Chemcrin/IntelligentTransformCart/代码/VibeCoding/工程纠错/628问题核验与修复方案.md

# 628 问题审查核验与修复方案

> 核验对象：`D:\STM32CubeIDE\workspace_1.19.0\smart_logistics_car_integrated_route_2026-06-17`  
> 原始问题文档：`C:\Users\CloudyRain\Desktop\待办\个性化物流小车\代码\628问题审查.md`  
> 核验日期：2026-06-28  
> 说明：本报告仅核验问题和给出可行方案，未修改工程源码。

## 1. 总结结论

原 Markdown 文档中的核心问题大多真实存在，但有几处需要校正严重度或前提条件：系统 8 MHz、固定路线自动启动、电机反馈空桩、栈预留与 IOC 不一致都可以从源码或构建产物直接确认；RS485 方向控制和上电使能风险依赖实际硬件；部分“致命”描述更适合改为“高优先级风险”，否则后续修复容易被夸大的影响带偏。

| 分类 | 数量 | 结论 |
|---|---:|---|
| 确认存在，建议优先处理 | 6 | F1、F2、C1、C3、C4、M1 |
| 部分成立或依赖硬件确认 | 5 | C2、M2、M3、M4、S5 |
| 成立但不属于必须立即修复 | 7 | M5、S1、S2、S3、S4、S6、冗余代码清理 |
| 原文需校正 | 3 | F1 的外设影响表述偏重、F2 对当前固定路线的直接影响偏重、C1 的“通过 RPi 命令启动路线”当前没有现成命令 |

## 2. 问题逐项核验表

| 编号  | 原问题 | 是否存在 | 核验证据 | 严重度校正 |
| --- | --- | --- | --- | --- |
| F1  | 系统时钟仅 8 MHz HSI，未启用 PLL | 确认存在 | `Core/Src/main.c:154-172` 使用 HSI、`PLL_NONE`、`SYSCLKSource=HSI`；`.ioc` 中 `RCC.PLLCLKFreq_Value=8000000` | 高优先级。性能确实低于 72 MHz，但 UART/I2C 不必然异常，HAL 会按当前 PCLK 配置分频 |
| F2  | 电机反馈读取为空桩 | 确认存在 | `Core/Src/motor_manager.c:86-89` 只有 `return MECANUM_OK;`；`StraightControl_Apply()` 依赖 `rpm_fb` | 高优先级。对直线轮差闭环真实有影响；对当前 Standalone 固定路线的直接影响有限，因为路线本身关闭直线闭环 |
| C1  | Standalone 模式 200ms 后自动行驶 | 确认存在 | `config.h:5` 为 `FIXED_ROUTE_STANDALONE_ENABLE=1U`；`competition_route.h:23-24` 自动启动；`competition_route.c:159-175` 200ms 后放行 | P0 安全项。上电自动开始第一步 3.3m 前进，必须先处理或在物理上架空车轮 |
| C2  | RS485 方向控制依赖硬件 | 部分成立 | `mecanum_config.h:71` 为 `MODBUS_USE_RS485_DIR_GPIO=0u`；`modbus_rtu.c:27-39` GPIO 控制条件编译为空 | 依赖硬件。若模块自动方向，没问题；若 MAX485/SP3485 这类 DE/RE 必需，则通信会失败或不稳定 |
| C3  | 栈空间可能不足 | 确认存在风险 | `STM32F103C8TX_FLASH.ld:42` 为 `0x400`；`.ioc` 为 `ProjectManager.StackSize=0x800`；`remote_cmd.su` 显示 `remote_send_status=704B`、`RemoteCmd_Loop=136B` | 高优先级。不是必然溢出，但 1024B 对 `snprintf` 和多层调用余量过窄 |
| C4  | 上电即使能所有电机 | 确认存在 | `ChassisControl_Init()` 在 `chassis_control.c:45` 调用 `MotorManager_EnableAll(1u)`；`ZDTX42_EnableMotor()` 使用 `wait_response=0` | 安全风险。是否误动依赖驱动器行为，但上电即使能不利于调试安全 |
| M1  | Modbus 固定长度接收 | 确认存在 | `modbus_rtu.c:121` 直接 `HAL_UART_Receive(..., rx_max_len, timeout_ms)` | 中优先级。异常帧或短帧会等到超时，未来读反馈后会放大控制周期抖动 |
| M2  | CRC 错误无重试 | 基本成立 | `modbus_rtu.c:132-133` CRC 错误直接返回；上层暂无重试 | 中优先级。当前反馈为空影响有限；实现反馈后应加入重试和错误计数 |
| M3  | 直线控制默认值与文档不一致 | 需按现代码确认 | `mecanum_config.h:50` 为 `0u`；当前路线 `CompetitionRoute_StartDefault()` 又主动 `Mecanum_EnableStraightControl(0U)` | 低到中。属于文档和行为一致性问题，不是运行阻断 |
| M4  | 固定路线旋转未启用 IMU 闭环 | 确认存在 | `competition_route.h:67-68` 为 `0U`；`competition_route.c:269-288` 按时间开环旋转 | 中优先级。若比赛要求角度精度，应做；若当前只为跑通路线，可先调时间和速度 |
| M5  | 两套传感器快照重复 | 确认存在 | `sensors.h` 定义 `SENSOR_Snapshot_t`；`sensor_bridge.h` 定义 `SensorSnapshot_t`；`sensor_bridge.c` 转换 | 低优先级。主要是维护成本和少量 RAM/CPU，不是安全阻断 |
| S1  | CSV/状态帧建议 DMA | 成立 | `remote_cmd.c` 多处 `HAL_UART_Transmit`；`csv_debug.c:76-80` 明确 TODO | 优化项。状态帧 360B 级别阻塞发送会拖慢主循环，尤其非 Standalone 模式 |
| S2  | 建议 IWDG | 成立 | `stm32f1xx_hal_conf.h` 中 IWDG 模块未启用；未见 IWDG 初始化 | 可靠性增强，不是当前功能错误 |
| S3  | 确认优化级别 | 成立且已确认 Debug 为 O0 | `Debug/*/subdir.mk` 使用 `-O0` | 发布前应切换到优化构建；调试期 `-O0` 可接受 |
| S4  | 屏蔽未用正运动学 | 成立但不建议优先做 | `Mecanum_ForwardKinematics` 仅定义未见调用；但函数本身小 | 低优先级。先修安全和通信，最后再裁剪 |
| S5  | USART1 建议中断接收 | 部分成立 | `usart.c` 只给 USART2 配了中断，USART1 当前阻塞式 Modbus | 取决于是否改异步 Modbus。若保留阻塞主从问答，USART1 中断不是必须 |
| S6  | 主循环顺序建议 | 成立 | `main.c:130-137` 先执行其他任务，后执行 `Mecanum_PeriodicTask()` | 优化项。非 Standalone 模式下状态发送/传感器可能延迟底盘周期 |

## 3. 需要修正原文的点

| 原文说法 | 建议修正 |
| --- | --- |
| F1 被定为“致命”，并推断 UART/I2C 时序会严重偏差 | 8 MHz 确实降低性能，但 HAL 会基于 PCLK 配置 UART/I2C 分频；更准确说法是性能余量和 DWT 微秒延时精度下降，外设并非必然失效 |
| F2 被定为“致命”，并直接关联整体不可运行 | 反馈空桩会让轮速差闭环无效，但当前固定路线是开环时间控制，且 `CompetitionRoute_StartDefault()` 主动关闭直线控制；它是控制精度问题，不是当前上电自动路线的唯一阻断 |
| C1 建议关闭自动启动后“通过 RPi 命令启动” | 当前 `remote_cmd.c` 没有固定路线启动命令，只有 `VEL/STOP/SC/...`。若关闭自动启动，需要新增 `ROUTE START/STOP/STATUS` 之类命令或按钮 GPIO |

## 4. 推荐修复优先级

| 阶段 | 目标 | 建议动作 | 备注 |
|---|---|---|---|
| Phase 0 | 上电安全 | 关闭自动路线启动，或增加物理启动条件；烧录/调试前架空车轮 | 最优先，避免上电直接运动 |
| Phase 1 | 时钟和基础配置 | 将系统时钟调整到 72 MHz 或明确保留 8 MHz 的理由；同步 `.ioc` 和 `SystemClock_Config()` | 若没有外部 8 MHz 晶振，可使用 HSI/2 x PLL，但 USART 精度不如 HSE |
| Phase 1 | 栈余量 | 将链接脚本 `_Min_Stack_Size` 至少同步为 `0x800`；减少 `remote_cmd` 大栈缓冲 | `.su` 已显示单函数 704B，1024B 太紧 |
| Phase 2 | 电机通信可靠性 | `MotorManager_EnableAll/SetWheelRpm` 聚合返回错误，不要总返回 OK；使能命令按需等待响应 | 先有错误可见性，再谈闭环 |
| Phase 2 | 电机反馈 | 实现轮询式 `MotorManager_UpdateFeedback()`，每 50ms 读 1 个电机或每周期读 1 个，避免 4 路连续超时 | 不建议一次读 4 个阻塞 40ms |
| Phase 2 | RS485 硬件确认 | 确认模块是否自动方向；若需 DE/RE，启用 `MODBUS_USE_RS485_DIR_GPIO` 并配置 GPIO | 这条必须结合实物或原理图 |
| Phase 3 | 路线精度 | 固定路线旋转使用 IMU yaw 闭环；平移距离长期应引入编码器/里程计 | 当前仅靠时间开环，地面和电压变化会漂 |
| Phase 4 | 性能和维护 | 状态输出改 DMA 或拆短帧；合并传感器快照；裁剪未用功能 | 等 P0/P1 修完后再做 |

## 5. 可行解决方案

### 5.1 自动启动安全方案

| 方案 | 改动量 | 优点 | 缺点 | 推荐场景 |
|---|---:|---|---|---|
| A. 默认关闭 `COMPETITION_ROUTE_AUTO_START` | 小 | 最安全，上电不动 | 需要新增启动方式或手动改宏 | 调试、日常开发 |
| B. 保留自动启动，但增加 GPIO 按键/拨码使能 | 中 | 不依赖 RPi，比赛可一键启动 | 需要占用一个 GPIO 并做消抖 | 现场比赛 |
| C. 新增 RPi 命令 `ROUTE START/STOP/STATUS` | 中 | 可远程控制路线，便于测试 | 当前协议没有，需要加接口 | 带树莓派运行 |
| D. 保留当前自动启动，仅物理架空调试 | 零代码 | 不改软件 | 人为失误风险高 | 仅临时验证 |

建议采用 A + C：默认不上电自跑，同时补一个明确的路线启动命令。若最终比赛必须脱离 RPi，再加 B。

### 5.2 时钟方案

| 方案 | 条件 | 做法 | 风险 |
|---|---|---|---|
| HSE 8 MHz + PLL x9 到 72 MHz | 板上有外部 8 MHz 晶振 | `RCC_OSCILLATORTYPE_HSE`、`PLLSource=HSE`、`PLLMUL=9`、APB1 分频 2、Flash latency 2 | 需要确认晶振实物存在 |
| HSI/2 + PLL x16 到 64 MHz | 无 HSE | 使用 HSI 分频进 PLL | HSI 精度较差，串口波特率余量较差 |
| 保留 8 MHz | 性能需求低且已实测稳定 | 明确注释并调整控制周期/超时预期 | 不适合浮点控制和高频状态输出 |

### 5.3 电机反馈和 Modbus 方案

| 方案 | 说明 | 建议 |
|---|---|---|
| 轮询反馈 | `MotorManager_UpdateFeedback()` 每次只读一个电机，下一次读下一个 | 推荐，避免 4 个电机连续超时拖垮 20ms 控制周期 |
| 连续反馈 | 每 50ms 连续读 4 个电机 | 不推荐，任何掉线都会叠加超时 |
| 读反馈重试 | CRC/超时重试 1 次，累计 `timeout_cnt/crc_error_cnt` | 推荐，避免偶发总线噪声直接污染状态 |
| 命令错误上报 | `MotorManager_SetWheelRpm()` 只要任一电机失败就返回错误 | 推荐，让底盘层能进入故障或降级 |

### 5.4 栈和串口输出方案

| 问题 | 证据 | 方案 |
|---|---|---|
| 链接脚本仍是 1024B 栈 | `_Min_Stack_Size=0x400`，而 `.ioc` 是 `0x800` | 将 `.ld` 同步到 `0x800` 或 `0x1000` |
| 状态发送单函数栈大 | `remote_send_status=704B`、`remote_send_imu=672B`、`remote_send_sensors=600B` | 缩小局部 `tx[]`，拆分发送，减少局部小数组 |
| `snprintf` 引入 libc 栈和代码 | `.map` 显示 `snprintf/_svfprintf_r` 被引入 | 对高频状态帧改轻量格式化或固定字段发送 |

## 6. 建议先不做的事

| 项目 | 原因 |
|---|---|
| 立即大规模裁剪 VL53L1/JY61P/remote_cmd | 当前最大风险不是 Flash 空间，而是上电安全、时钟、栈、反馈和错误处理 |
| 直接把所有 Modbus 改成中断/DMA | 改动面大，先用轮询反馈和短超时把风险降下来 |
| 直接启用 IMU 旋转闭环 | Standalone 模式当前不初始化 I2C/IMU，必须先恢复传感器初始化或切回非 Standalone |
| 合并传感器快照结构 | 维护优化，放在安全和通信问题之后更稳 |

## 7. 最小落地路径

| 步骤  | 内容 | 验证方式 |
| --- | --- | --- |
| 1 | 关闭自动路线启动或增加启动门控 | 上电后状态保持 `IDLE/WAIT_ARM`，车轮不转 |
| 2 | 修正系统时钟并重新生成 Cube 配置 | `HAL_RCC_GetHCLKFreq()` 返回预期频率，串口通信正常 |
| 3 | 链接脚本栈改到 `0x800` 或 `0x1000` | `.map` 中 `_Min_Stack_Size` 更新 |
| 4 | 电机命令错误不再被吞掉 | 拔掉某个电机后 `online=0` 或返回错误可见 |
| 5 | 轮询读取电机反馈 | `rpm_fb` 能随电机转速变化，`SC ?` 能看到左右轮反馈 |
| 6 | 确认 RS485 模块方向控制 | 实测发送波形和响应稳定，无响应时再启用 GPIO DE/RE |
| 7 | 根据比赛需求做 IMU 旋转闭环 | 90 度旋转重复误差进入目标范围 |

## 8. 结论

原 Markdown 中的问题不是“凭空猜测”，大部分都能在当前工程中找到证据。真正需要马上拦住的是上电自动行驶、时钟配置、栈余量和电机通信错误不可见；电机反馈空桩也需要尽快补，但建议用轮询方式实现，避免把控制周期拖坏。RS485 方向控制必须结合实际模块型号判断，不能单靠源码定性为错误。

本次未修改任何源码。下一步如果要动代码，建议先按 Phase 0 和 Phase 1 做最小安全修复，再编译和上车验证。
