Chemcrin/IntelligentTransformCart/代码/VibeCoding/工程纠错/629工程整改指南.md

## 项目背景
基于STM32的智能物流小车，其底盘电机通过RS485总线控制。由于硬件设计限制，RS485接口当前仅具备单向发送能力，无法接收来自电机驱动器的状态回传信号。
#  核心需求
## 1. 电机只发不收开环控制确认
在保证小车能正常完成前进、后退、转向等基本运动功能的前提下，确认电机控制策略调整为**只发不收的开环控制**。软件架构必须彻底移除对电机反馈数据的依赖，仅保留控制指令下发通路。
故可以移除一些用于接收电机运行状态回传的函数比如空实现的`MotorManager_UpdateFeedback()` 

## 2. 陀螺仪辅助纠偏功能完善

### **总体思路**

| 项目 | 方案 B 设计 |
| ----- | --- |
| 保留内容  | 固定路线、ZDT 电机下发、原来的时间开环距离控制全部保留 |
| 新增内容  | 只启用 IMU yaw 数据；只在直线前进/后退时做轻量纠偏 |
| 控制方式  | 进入直线段时记录当前 yaw 为目标航向，行驶中持续比较当前 yaw 和目标 yaw |
| 修正方式  | yaw 偏左/偏右时叠加很小的 `wz`，让四轮 RPM 自动产生差速修正 |
| 回退策略  | IMU 无效、未校准、数据超时、偏差异常时，立即退回原来的开环直行 |
| 不启用内容 | 不启用激光、不启用树莓派、不启用完整 `Board_App`，避免旧逻辑干扰 |

推荐的数据流是：

```
固定路线目标速度 vy
        ↓
读取 IMU yaw
        ↓
计算 yaw_error = target_yaw - current_yaw
        ↓
PID/比例控制得到 correction_wz
        ↓
修正速度: vx 不变, vy 不变, wz += correction_wz
        ↓
麦轮逆运动学
        ↓
四个 ZDT 电机 RPM
```

**直线纠偏触发条件**

| 条件 | 建议规则 |
| --- | --- |
| 只在直线段启用 | `abs(vy) > 0.03 m/s` |
| 不在横移时启用 | `abs(vx) < 0.01 m/s` |
| 不在主动旋转时启用  | `abs(wz) < 0.01 rad/s` |
| IMU 必须有效 | `imu_valid == 1` |
| IMU 必须完成校准 | `imu_calibrated == 1` |
| yaw 数据不能超时 | 当前 tick 与 IMU 最后更新时间差不超过阈值 |
| 偏差异常时退出 | 例如 yaw 偏差超过 `20~30 deg`，不要强行纠偏 |

**关键点：不要边走边做陀螺仪零偏校准，启动前校准传感器，行驶中保持航向。**

| 概念 | 建议 |
| --- | --- |
| 陀螺仪零偏校准 | 在小车静止时完成，上电后静止 2~3 秒 |
| 直线行驶纠偏 | 不是重新校准陀螺仪，而是“保持进入直线段时的 yaw” |
| `ZERO`/yaw 归零 | 在出发前做，不在直线运动中频繁归零 |
| 直线段目标 yaw | 每进入一个新的前进/后退段时记录一次当前 yaw |
**推荐实施步骤**

|阶段|做什么|目的|
|---|---|---|
|1|保持 `FIXED_ROUTE_STANDALONE_ENABLE = 1U`|保证现有固定路线能力不被破坏|
|2|单独启用 `MX_I2C1_Init()`、`IMU_App_Init()`、`IMU_App_Loop()`|只接入陀螺仪，不拉起激光和树莓派逻辑|
|3|上电后等待 IMU 校准完成，或超时后继续开环|防止因为 IMU 不可用导致小车不跑|
|4|固定路线启动时允许直线纠偏|只改变直线段表现|
|5|`StraightControl_Apply()` 中根据 yaw 偏差输出小 `wz`|用麦轮差速修正方向|
|6|IMU 异常时自动关闭纠偏|保留原来的开环直行能力|
|7|实车逐步调小/调大 PID 参数|避免蛇形摆动或修正不足|

**建议参数初值**

|参数|建议初值|说明|
|---|---|---|
|yaw 纠偏最大 `wz`|`0.15 rad/s`|先小一点，避免摆动|
|yaw 死区|`1.0~2.0 deg`|小误差不修正|
|yaw 比例系数 `Kp`|`0.8~1.2`|先只用 P 或极小 PI|
|积分 `Ki`|`0~0.03`|初期可先不用|
|微分 `Kd`|`0~0.02`|抑制摆动，谨慎加|
|IMU 启动等待|`2000~3000 ms`|给静止校准留时间|
|IMU 失效超时|`200~500 ms`|超时直接开环|

**安全回退逻辑**

|场景|处理|
|---|---|
|IMU 没初始化成功|路线继续按原开环直行|
|`imu_valid = 0`|不叠加 `wz`|
|`imu_calibrated = 0`|不叠加 `wz`|
|yaw 突跳过大|本段放弃纠偏|
|修正量超过限制|clamp 到最大 `wz`|
|小车进入横移/旋转段|自动重置直线纠偏状态|

我建议最终做成两个开关：  
`IMU_ASSIST_ENABLE` 控制是否单独启用 IMU；  
`ROUTE_STRAIGHT_YAW_ASSIST_ENABLE` 控制固定路线直线段是否使用 yaw 纠偏。

## 3. 运行路径修改
根据实际的比赛场地进行小车实际运行路径的修改：单位mm
左移         180
前行       3400
逆时针转    90
前行        800
停止60s （夹球）
逆时针转    90
前行       1000
停止30s （扫码）
右移         220
前行       1350
左移         220
前行         500
右移         220

## 4. 串口信号微调
现在需要你将电机发送给uart3的信号，同时发送给uart1（pa9\pa10引脚），不需要调整发送的内容与格式，保证uart1发送的信号与uart3一致，也保证其他功能不受影响。先列举出你这次调整会涉及的代码文件以及main.c中的有关部分，暂不直接修改代码

## 5.激光模块移除

**审查结论**

| 问题 | 判断 |
| --- | --- |
| 项目里是否有激光传感器代码 | 有，主要是 [laser_app.c](D:/STM32CubeIDE/workspace_1.19.0/history/Core/Src/laser_app.c)、[atk_ms53l1m.c](D:/STM32CubeIDE/workspace_1.19.0/history/Core/Src/atk_ms53l1m.c) 及对应头文件 |
| `main.c` 是否写了激光相关控制 | 有，[main.c (line 44)](D:/STM32CubeIDE/workspace_1.19.0/history/Core/Src/main.c:44) 定义 `APP_LASER_STOP_LEVEL`，[151 行 (line 151)](D:/STM32CubeIDE/workspace_1.19.0/history/Core/Src/main.c:151) 根据 `snap.laser_valid` / `snap.laser_warning` 决定是否急停 |
| 激光模块是否实际生效 | 是，当前主循环把激光状态作为小车运动 Demo 的前置安全条件 |
| 未检测到激光会不会导致不发车 | 会。`laser_valid == false` 时会设置外部急停，且不会执行 `App_RunMotionDemo()` |
| 删除激光代码是否可行 | 可行，但不能只删 `laser_app.*`，需要同步改 `main.c`、`board_app.*`、`sensors.*`、`sensor_bridge.*` 等依赖点 |
| 删除后主要影响 | 小车不再因激光缺失/过近急停，能减少 I2C/VL53 编译依赖，但会失去前方近距保护 |

**关键调用链**

|环节|文件/位置|作用|
|---|---|---|
|初始化激光|[board_app.c (line 9)](D:/STM32CubeIDE/workspace_1.19.0/history/Core/Src/board_app.c:9)|`Board_App_Init()` 调用 `Laser_App_Init()`|
|周期轮询激光|[sensors.c (line 41)](D:/STM32CubeIDE/workspace_1.19.0/history/Core/Src/sensors.c:41)|`sensor_update()` 调用 `Laser_App_Loop()`|
|转换为上层状态|[sensor_bridge.c (line 43)](D:/STM32CubeIDE/workspace_1.19.0/history/Core/Src/sensor_bridge.c:43)|激光无效时 `distance_m = -1.0f`，`laser_valid = false`|
|主循环急停判断|[main.c (line 151)](D:/STM32CubeIDE/workspace_1.19.0/history/Core/Src/main.c:151)|激光无效或 warning 达到 3 级就 `ChassisControl_SetExternalEmergency(1U)`|
|急停落地|[chassis_control.c (line 129)](D:/STM32CubeIDE/workspace_1.19.0/history/Core/Src/chassis_control.c:129)|外部急停触发 `ChassisControl_EmergencyStop()`，最终调用电机急停|

**删除/移除激光相关代码时的改动范围**

| 类型  | 文件 | 建议处理 |
| --- | --- | --- |
| 可删除 | `Core/Src/laser_app.c`、`Core/Inc/laser_app.h` | 激光应用层 |
| 可删除 | `Core/Src/atk_ms53l1m.c`、`Core/Inc/atk_ms53l1m.h` | ATK-MS53L1M/VL53L1 驱动封装 |
| 必改  | [main.c](D:/STM32CubeIDE/workspace_1.19.0/history/Core/Src/main.c) | 移除 `APP_LASER_STOP_LEVEL` 和基于 `snap.laser_valid` 的急停门控，直接运行运动逻辑或改为其他安全条件 |
| 必改  | [board_app.c](D:/STM32CubeIDE/workspace_1.19.0/history/Core/Src/board_app.c) | 去掉 `#include "laser_app.h"` 和 `Laser_App_Init()` |
| 必改  | [sensors.c](D:/STM32CubeIDE/workspace_1.19.0/history/Core/Src/sensors.c) / [sensors.h](D:/STM32CubeIDE/workspace_1.19.0/history/Core/Inc/sensors.h) | 去掉激光字段、`Laser_App_Loop()`、`atk_ms53l1m.h` 依赖 |
| 必改  | [sensor_bridge.c](D:/STM32CubeIDE/workspace_1.19.0/history/Core/Src/sensor_bridge.c) / [sensor_bridge.h](D:/STM32CubeIDE/workspace_1.19.0/history/Core/Inc/sensor_bridge.h) | 去掉 `Laser_*` 查询接口、`laser_valid`、`laser_warning`、距离字段或改成固定安全值 |
| 可选  | `.ioc` / I2C1 配置 | 如果 IMU 仍使用 I2C1，就不能删除 I2C1；如果没有其他 I2C 设备，才可移除 PB6/PB7/I2C1 |
| 可选  | `.cproject` / include path | 若补过 VL53L1 API 路径，删除后可清理；当前项目内没有发现 `vl53l1_api.h/.c` |

补充一点：当前工程中 [atk_ms53l1m.c (line 2)](D:/STM32CubeIDE/workspace_1.19.0/history/Core/Src/atk_ms53l1m.c:2) 引用了 `vl53l1_api.h`，但我在该项目目录内没有找到 VL53L1 API 文件。如果没有外部 include/source 路径补齐，这部分本身就会造成编译问题。删除激光模块反而可以消除这条依赖，但代价就是失去激光避障/急停保护。

因为激光模块的删除，现在需要移除代码中有关激光避障/急停保护，要求你针对刚刚整理出来的文件进行修改包括：

| 类型 | 文件 | 建议处理 |
| --- | --- | --- |
| 删除 | `Core/Src/laser_app.c`、`Core/Inc/laser_app.h` | 激光应用层 |
| 删除 | `Core/Src/atk_ms53l1m.c`、`Core/Inc/atk_ms53l1m.h` | ATK-MS53L1M/VL53L1 驱动封装 |
| 必改 | [main.c](D:/STM32CubeIDE/workspace_1.19.0/history/Core/Src/main.c) | 移除 `APP_LASER_STOP_LEVEL` 和基于 `snap.laser_valid` 的急停门控，直接运行运动逻辑或改为其他安全条件 |
| 必改 | [board_app.c](D:/STM32CubeIDE/workspace_1.19.0/history/Core/Src/board_app.c) | 去掉 `#include "laser_app.h"` 和 `Laser_App_Init()` |
| 必改 | [sensors.c](D:/STM32CubeIDE/workspace_1.19.0/history/Core/Src/sensors.c) / [sensors.h](D:/STM32CubeIDE/workspace_1.19.0/history/Core/Inc/sensors.h) | 去掉激光字段、`Laser_App_Loop()`、`atk_ms53l1m.h` 依赖 |
| 必改 | [sensor_bridge.c](D:/STM32CubeIDE/workspace_1.19.0/history/Core/Src/sensor_bridge.c) / [sensor_bridge.h](D:/STM32CubeIDE/workspace_1.19.0/history/Core/Inc/sensor_bridge.h) | 去掉 `Laser_*` 查询接口、`laser_valid`、`laser_warning`、距离字段或改成固定安全值 |
| 可选（也进行修改） | `.cproject` / include path | 若补过 VL53L1 API 路径，删除后可清理；当前项目内没有发现 `vl53l1_api.h/.c` |
同时解决当前工程中 [atk_ms53l1m.c (line 2)](D:/STM32CubeIDE/workspace_1.19.0/history/Core/Src/atk_ms53l1m.c:2) 引用了 `vl53l1_api.h`的虚拟引用问题，删除该include path即可
现在需要你直接对代码进行修改，保证不影响其他模块的前提下移除干净有关激光的代码文件及main.c有关内容，

## 6. 树莓派上位机控制
现在我的树莓派通过一根typeC的数据线连接在了stm32开发板的typeC接口上，该C口连接的是连接了uart2的一颗ch340N芯片。现在我的stm32可以使用uart2串口通信接收相关树莓派信号，我需要你提供新增树莓派控制stm32从而控制小车底盘的硬件连接方式、控制逻辑，具体实现方式，32会接收到怎么样的数据，如何根据这些数据控制小车底盘移动，如何在现有运行路径中增加中断，从而调控小车位置。不需要你直接修改代码，先梳理思路，给出一份完整的方案Markdown文档
