Chemcrin/IntelligentTransformCart/代码/VibeCoding/Docs/STM32CubeIDE工程无法识别解决方案.md

# STM32CubeIDE 工程在工作区创建后无法识别的解决方案

本文档用于指导其他 Agent 处理以下常见问题：

- 已经把 STM32CubeIDE 工程目录放入 `workspace_1.19.0`，但 IDE 的 Project Explorer 中看不见。
- 工程目录内有 `.project`、`.cproject`、`.ioc`，但 STM32CubeIDE 仍无法识别或导入异常。
- 通过导入命令后项目出现，但构建失败，原因来自工程元数据或基础头文件缺失。

## 一、典型现象

| 现象 | 常见含义 |
|---|---|
| 工程文件夹在 workspace 目录内，但 IDE 不显示 | Eclipse/CubeIDE workspace 元数据未注册该项目 |
| 手工创建 `.metadata\.plugins\org.eclipse.core.resources\.projects\项目名` 后仍不显示 | Eclipse 的工程树状态不只依赖这个目录，还依赖内部索引和资源树 |
| `File > Import > Existing Projects into Workspace` 扫描不到或报错 | `.project` 或 `.cproject` 可能损坏，或选择的 workspace 不一致 |
| headless import 输出 `Opening '项目名'` | 工程已被 CubeIDE 正式打开/注册 |
| headless import 输出 XML fatal error | `.cproject`、`.project` 或 `.settings` 中 XML 格式有误 |
| IDE 打开后仍看不到项目 | 实际启动的 CubeIDE 可能使用了另一个 workspace |

## 二、根本原因分析

### 1. 把工程目录放进 workspace 不等于导入工程

STM32CubeIDE 基于 Eclipse/CDT。Eclipse 并不会因为某个文件夹出现在 workspace 下，就自动把它显示为项目。

一个可识别工程至少需要：

| 文件/目录 | 作用 |
|---|---|
| `.project` | Eclipse 项目描述，包含项目名和 nature |
| `.cproject` | CDT/CubeIDE 构建配置 |
| `.mxproject` | CubeMX/CubeIDE 生成记录 |
| `*.ioc` | CubeMX 外设和工程配置 |
| `.metadata` 注册信息 | 当前 workspace 内部项目索引 |

因此，仅复制目录通常不够，最可靠方式是使用 CubeIDE 自带 headless import 注册。

### 2. 可能存在多套 CubeIDE 安装路径

本机曾出现过类似情况：

| 路径 | 说明 |
|---|---|
| `D:\STM32CubeIDE\STM32CubeIDE_1.19.0\...` | 目录存在，但其中可能不是实际启动的 IDE |
| `D:\STM32CubeIDE_1.19.0\STM32CubeIDE\stm32cubeide.exe` | 快捷方式真实指向的 IDE |

如果 Agent 在错误的安装目录下找命令行工具，或用户打开的是另一套 IDE，就会出现“命令行注册了，但图形界面看不到”的错觉。

应优先解析开始菜单快捷方式，确认真实 `stm32cubeide.exe` 路径。

### 3. workspace 选择不一致

即使工程已经导入到：

```text
D:\STM32CubeIDE\workspace_1.19.0
```

如果用户启动 IDE 时选择了其他 workspace，Project Explorer 中仍然看不到该工程。

必须确认 STM32CubeIDE 启动时 Workspace Launcher 中选择的是目标 workspace。

### 4. `.cproject` XML 损坏会导致导入异常

示例错误：

```text
[Fatal Error] :67:11: 元素类型 "inputType" 必须由匹配的结束标记 "</inputType>" 终止。
```

实际原因可能是 `.cproject` 中标签写错，例如：

```xml
<inputType ...>
    <additionalInput kind="additionalinputdependency" paths="$(USER_OBJS)"/>
    <additionalInput kind="additionalinput" paths="$(LIBS)"/>
</additionalInput>
```

正确写法：

```xml
<inputType ...>
    <additionalInput kind="additionalinputdependency" paths="$(USER_OBJS)"/>
    <additionalInput kind="additionalinput" paths="$(LIBS)"/>
</inputType>
```

这种错误会让 CubeIDE 反复报 XML fatal error，并影响工程识别、索引、构建配置加载。

## 三、推荐处理流程

### Step 1：确认工程目录基础结构

目标工程目录示例：

```text
D:\STM32CubeIDE\workspace_1.19.0\Final_Smart627
```

检查根目录是否至少包含：

| 必需项 | 示例 |
|---|---|
| `.project` | `D:\STM32CubeIDE\workspace_1.19.0\Final_Smart627\.project` |
| `.cproject` | `D:\STM32CubeIDE\workspace_1.19.0\Final_Smart627\.cproject` |
| `.ioc` | `Final_Smart627.ioc` |
| `Core` | `Core\Inc`、`Core\Src` |
| `Drivers` | HAL、CMSIS |
| 链接脚本 | 如 `STM32F103C8TX_FLASH.ld` |

PowerShell 检查命令：

```powershell
Get-ChildItem -LiteralPath 'D:\STM32CubeIDE\workspace_1.19.0\Final_Smart627' -Force |
    Select-Object Name,Mode,Length,LastWriteTime
```

### Step 2：检查 `.project` 工程名

```powershell
Get-Content -LiteralPath 'D:\STM32CubeIDE\workspace_1.19.0\Final_Smart627\.project'
```

确认：

```xml
<name>Final_Smart627</name>
```

项目名必须与预期一致。大小写不一定必须和目录完全一致，但建议保持一致。

### Step 3：确认真实 CubeIDE 命令行工具路径

优先检查常见安装路径：

```powershell
Get-ChildItem -LiteralPath 'D:\STM32CubeIDE_1.19.0\STM32CubeIDE' -Force |
    Select-Object Name,Mode,Length,LastWriteTime
```

应能看到：

```text
stm32cubeide.exe
stm32cubeidec.exe
headless-build.bat
```

如果不确定用户实际打开的是哪一个 CubeIDE，可解析开始菜单快捷方式：

```powershell
$lnk = 'C:\ProgramData\Microsoft\Windows\Start Menu\Programs\STMicroelectronics\STM32CubeIDE 1.19.0\STM32CubeIDE 1.19.0.lnk'
$ws = New-Object -ComObject WScript.Shell
$s = $ws.CreateShortcut($lnk)
[pscustomobject]@{
    TargetPath       = $s.TargetPath
    Arguments        = $s.Arguments
    WorkingDirectory = $s.WorkingDirectory
    IconLocation     = $s.IconLocation
}
```

### Step 4：使用 CubeIDE headless import 正式导入项目

不要只手工改 `.metadata`，优先使用 CubeIDE 官方 headless import。

命令模板：

```powershell
& 'D:\STM32CubeIDE_1.19.0\STM32CubeIDE\stm32cubeidec.exe' `
  --launcher.suppressErrors `
  -nosplash `
  -application org.eclipse.cdt.managedbuilder.core.headlessbuild `
  -data 'D:\STM32CubeIDE\workspace_1.19.0' `
  -import 'D:\STM32CubeIDE\workspace_1.19.0\Final_Smart627'
```

成功时常见输出：

```text
Create.
Opening 'Final_Smart627'.
```

或：

```text
Opening 'Final_Smart627'.
```

说明工程已经被 CubeIDE 工程模型打开并注册。

### Step 5：确认 workspace 注册列表

```powershell
Get-ChildItem -LiteralPath 'D:\STM32CubeIDE\workspace_1.19.0\.metadata\.plugins\org.eclipse.core.resources\.projects' -Force |
    Select-Object Name,Mode,LastWriteTime
```

应能看到：

```text
Final_Smart627
```

注意：看到这个目录并不一定代表图形 IDE 一定显示，但 headless import 成功后再出现这个目录，可信度较高。

### Step 6：如导入时出现 XML 错误，先修复 `.cproject`

常用定位命令：

```powershell
$i = 0
Get-Content -LiteralPath 'D:\STM32CubeIDE\workspace_1.19.0\Final_Smart627\.cproject' |
    ForEach-Object {
        $i++
        if ($i -ge 45 -and $i -le 85) {
            '{0,4}: {1}' -f $i, $_
        }
    }
```

检查所有 `inputType`、`tool` 标签：

```powershell
Select-String -LiteralPath 'D:\STM32CubeIDE\workspace_1.19.0\Final_Smart627\.cproject' `
    -Pattern '<inputType|</inputType>|<tool |</tool>'
```

XML 校验：

```powershell
[xml](Get-Content -LiteralPath 'D:\STM32CubeIDE\workspace_1.19.0\Final_Smart627\.cproject' -Raw) | Out-Null
```

若报错：

```text
The 'inputType' start tag ... does not match the end tag of 'additionalInput'
```

可修复错误结束标签：

```powershell
$path = 'D:\STM32CubeIDE\workspace_1.19.0\Final_Smart627\.cproject'
$text = Get-Content -LiteralPath $path -Raw
$text = $text -replace '</additionalInput>', '</inputType>'
Set-Content -LiteralPath $path -Value $text -Encoding UTF8
[xml](Get-Content -LiteralPath $path -Raw) | Out-Null
```

修复后重新执行 headless import。

### Step 7：执行 Debug 构建验证

导入成功不代表源码一定能编译。建议继续跑一次构建：

```powershell
& 'D:\STM32CubeIDE_1.19.0\STM32CubeIDE\stm32cubeidec.exe' `
  --launcher.suppressErrors `
  -nosplash `
  -application org.eclipse.cdt.managedbuilder.core.headlessbuild `
  -data 'D:\STM32CubeIDE\workspace_1.19.0' `
  -printErrorMarkers `
  -markerType all `
  -cleanBuild 'Final_Smart627/Debug'
```

成功输出类似：

```text
Build Finished. 0 errors, 3 warnings.
Headless build completed successfully
```

生成文件示例：

```text
D:\STM32CubeIDE\workspace_1.19.0\Final_Smart627\Debug\Final_Smart627.elf
```

## 四、常见源码级补救

### 1. `unknown type name 'int32_t'`

错误示例：

```text
../Core/Inc/config.h:94:5: error: unknown type name 'int32_t'
```

原因：头文件中使用 `int32_t`，但未包含 `<stdint.h>`。

修复：

```c
#ifndef CONFIG_H
#define CONFIG_H

#include <stdint.h>

#ifdef __cplusplus
extern "C" {
#endif
```

PowerShell 自动补充示例：

```powershell
$path = 'D:\STM32CubeIDE\workspace_1.19.0\Final_Smart627\Core\Inc\config.h'
$text = Get-Content -LiteralPath $path -Raw
if ($text -notmatch '#include\s+<stdint\.h>') {
    $text = $text -replace '#define CONFIG_H\s*', "#define CONFIG_H`r`n`r`n#include <stdint.h>`r`n"
    Set-Content -LiteralPath $path -Value $text -Encoding UTF8
}
```

### 2. `implicit declaration of function 'Error_Handler'`

警告示例：

```text
warning: implicit declaration of function 'Error_Handler'
```

通常不阻塞构建，但建议确保 `main.h` 中声明：

```c
void Error_Handler(void);
```

并确保外设源文件包含了 `main.h`。

## 五、不推荐的做法

| 做法 | 原因 |
|---|---|
| 只复制工程目录到 workspace | Eclipse 不会自动显示项目 |
| 只手动创建 `.metadata\.plugins\org.eclipse.core.resources\.projects\项目名` | workspace 内部还有资源树/索引，容易不完整 |
| 直接删除整个 `.metadata` | 会破坏用户已有工作区、断开其他项目 |
| 盲目覆盖 `.cproject` | 可能丢失 MCU、include path、sourceEntries、linker script 配置 |
| 未确认实际 CubeIDE 安装路径就导入 | 可能导入到了用户没有打开的 IDE/workspace |

## 六、Agent 操作建议

| 阶段 | 建议 |
|---|---|
| 读取工程 | 先看 `.project`、`.cproject`、`.ioc` |
| 判断 IDE 路径 | 解析快捷方式或检查 `stm32cubeidec.exe` 所在目录 |
| 注册项目 | 使用 headless import |
| 修复元数据 | 优先做最小修改，如 XML 标签闭合 |
| 验证结果 | 检查 workspace 注册列表，并运行 headless cleanBuild |
| 用户提示 | 告诉用户必须选择同一个 workspace |

## 七、完整示例流程

以 `Final_Smart627` 为例：

```powershell
# 1. 检查工程目录
Get-ChildItem -LiteralPath 'D:\STM32CubeIDE\workspace_1.19.0\Final_Smart627' -Force |
    Select-Object Name,Mode,Length,LastWriteTime

# 2. 检查 .project
Get-Content -LiteralPath 'D:\STM32CubeIDE\workspace_1.19.0\Final_Smart627\.project'

# 3. 校验 .cproject XML
[xml](Get-Content -LiteralPath 'D:\STM32CubeIDE\workspace_1.19.0\Final_Smart627\.cproject' -Raw) | Out-Null

# 4. 如有错误，修复常见错误标签
$path = 'D:\STM32CubeIDE\workspace_1.19.0\Final_Smart627\.cproject'
$text = Get-Content -LiteralPath $path -Raw
$text = $text -replace '</additionalInput>', '</inputType>'
Set-Content -LiteralPath $path -Value $text -Encoding UTF8
[xml](Get-Content -LiteralPath $path -Raw) | Out-Null

# 5. 正式导入
& 'D:\STM32CubeIDE_1.19.0\STM32CubeIDE\stm32cubeidec.exe' `
  --launcher.suppressErrors `
  -nosplash `
  -application org.eclipse.cdt.managedbuilder.core.headlessbuild `
  -data 'D:\STM32CubeIDE\workspace_1.19.0' `
  -import 'D:\STM32CubeIDE\workspace_1.19.0\Final_Smart627'

# 6. 检查注册
Get-ChildItem -LiteralPath 'D:\STM32CubeIDE\workspace_1.19.0\.metadata\.plugins\org.eclipse.core.resources\.projects' -Force |
    Select-Object Name,Mode,LastWriteTime

# 7. 构建验证
& 'D:\STM32CubeIDE_1.19.0\STM32CubeIDE\stm32cubeidec.exe' `
  --launcher.suppressErrors `
  -nosplash `
  -application org.eclipse.cdt.managedbuilder.core.headlessbuild `
  -data 'D:\STM32CubeIDE\workspace_1.19.0' `
  -printErrorMarkers `
  -markerType all `
  -cleanBuild 'Final_Smart627/Debug'
```

## 八、给用户的最终提示模板

处理完成后可以这样回复用户：

```text
已完成导入并注册。请重启 STM32CubeIDE，启动时确认 workspace 选择：

D:\STM32CubeIDE\workspace_1.19.0

Project Explorer 中应能看到 项目名。
如果 IDE 已经开着，可先尝试 File > Refresh；仍不显示则重启 IDE。
我已用 CubeIDE headless build 验证 Debug 配置可以正常构建。
```
