Chemcrin/IntelligentTransformCart/代码/VibeCoding/Docs/项目审查报告_2026-06-09.md

# `smart_logistics_car_integrated` 工程审查报告

## 1. 审查结论

| 项目 | 结论 |
| --- | --- |
| 工程路径 | `D:\STM32CubeIDE\workspace_1.19.0\smart_logistics_car_integrated` |
| 审查日期 | `2026-06-09` |
| 审查方式 | 静态代码审查 + 构建配置核对 + 当日下午修改痕迹梳理 |
| 总体判断 | 这份工程已经具备“底盘基础联调固件”的骨架，但还不能认定为“可稳定跑长距离直线、可直接写固定路径、可完整对外回传 IMU/激光数据”的完成态。 |
| 当前可确认能力 | IMU 采集、激光测距、底盘麦轮速度指令下发、远程串口控制、激光联锁急停、基础故障锁定 |
| 当前不能确认/尚未闭环 | 陀螺仪完整外部回传、激光完整外部回传、自动化 Bringup、自主路径执行、长距离直线稳定性、急停实际物理停止距离 |
| 是否需要调整 | 需要，且建议先做 `P0` 级调整，再进入树莓派视觉和机械臂联动阶段。 |

## 2. 下午修改内容识别

| 时间 | 文件 | 作用 | 当前状态 |
| --- | --- | --- | --- |
| `2026-06-09 15:21:52` | `UserModules/remote_cmd/remote_cmd.c` | 新增树莓派/上位机串口控制协议、心跳、状态上报、激光急停联锁 | 已加入构建，已接入主循环 |
| `2026-06-09 15:38:32` | `UserModules/bringup_mode/bringup_mode.c` | 新增电机地址检查、单轮点动、方向检查、激光急停验证 | 未加入当前构建 |
| `2026-06-09 15:51:29` | `UserModules/sensor_uart3_stream_test/sensor_uart3_stream_test.c` | 新增 IMU/激光 CSV 数据流调试模块 | 未加入当前构建，且与电机串口冲突 |
| `2026-06-09 17:30:59` | `Core/Src/main.c` | 将 `RemoteCmd` 接入系统初始化和主循环 | 已生效 |
| `2026-06-09 17:53:39` | `Core/Src/motor_manager.c` | 电机方向符号、反馈与故障判定逻辑调整 | 已生效 |
| `2026-06-09 18:02:56` | `Debug/*.elf` `Debug/*.map` | 说明工程在该时刻重新构建过 | 当前固件对应“`remote_cmd` 已接入”的版本 |

## 3. 当前工程实际能实现什么

| 能力 | 代码依据 | 现状判断 | 说明 |
| --- | --- | --- | --- |
| IMU 轮询采集 | `board_app.c:11-18`、`imu_app.c:69-87`、`jy61p.h:42-52` | 已具备 | `JY61P` 以 `10 ms` 周期轮询，启动时自动做陀螺仪静止零偏标定。 |
| 激光测距采集 | `laser_app.c:37-82`、`atk_ms53l1m.c:213-221` | 已具备 | `VL53L1` 测距周期设置为 `50 ms`，软件轮询节拍 `20 ms`。 |
| 统一传感器快照 | `sensors.c:6-46`、`sensor_bridge.c:9-44` | 已具备 | 已有内部快照接口，便于上层统一取数。 |
| 麦轮速度控制 | `mecanum.c:6-76`、`chassis_control.c:48-170` | 已具备基础能力 | 可按 `vx / vy / wz` 发送目标速度，带 RPM 限幅与加速度限幅。 |
| Modbus 电机驱动 | `zdt_x42_modbus.c:24-104`、`modbus_rtu.c:58-199` | 已具备 | `USART3` 作为电机总线。 |
| 电机反馈故障锁定 | `chassis_control.c:138-146`、`motor_manager.c:85-148` | 已具备，但仅用于故障检测 | 反馈用于“在线/超时/CRC”判断，不用于车体闭环控制。 |
| 远程串口控制 | `main.c:117-130`、`remote_cmd.h:40-45`、`remote_cmd.c:226-314` | 已具备 | 支持 `HB`、`VEL`、`STOP`、`ESTOP`、`CLR`、`ZERO`、`STAT?`。 |
| 激光触发急停 | `remote_cmd.c:168-195`、`atk_ms53l1m.h:21-27`、`atk_ms53l1m.c:105-120` | 已具备逻辑闭环 | 激光无效或“过近”时会锁死运动并下发急停。 |
| 航向清零 | `board_app.c:28-31`、`imu_app.c:88-93`、`remote_cmd.c:265-272` | 已具备 | 可在停止状态下执行 `ZERO`。 |

## 4. 当前工程还不能实现什么

| 项目 | 现状 | 判断 |
| --- | --- | --- |
| 陀螺仪数据外部回传 | 当前已编译固件只提供 `STAT` 状态帧，内容不包含 IMU 原始值/姿态值，`remote_cmd.c:140` 仅上报链路、速度、激光距离等。 | 不能算“已完成”  |
| 激光完整外部回传  | 当前 `STAT` 仅含 `dist` 和 `laser_warn`，没有原始值、滤波值、错误码全量外发。 | 只能算“部分完成” |
| 长距离直线稳定行驶 | 没有航向闭环、没有里程闭环、没有路径控制器。 | 目前不能保证 |
| 固定路径执行 | 缺少“走指定距离/转指定角度/到达目标点”的基础动作层。 | 尚未准备好 |

## 5. 需要立即关注的结构性问题

| 优先级  | 问题 | 依据 | 影响 | 建议 |
| ---- | --- | --- | --- | --- |
| `P0` | `sensor_uart3_stream_test` 与电机总线抢占同一串口 | `sensor_uart3_stream_test.c:49` 明写 `PB10_TX PB11_RX`；`usart.c:186-188` 显示这就是 `USART3`；`main.c:110` 已把 `huart3` 用于 `Mecanum_Init` | 若直接启用，会与电机 RS485 冲突  | 修改方式见任务书[工程修改任务书](../工程纠错/工程修改任务书.md) |
| `P0` | 当前底盘不是闭环直线控制 | `chassis_control.c:138-161` 只做反馈检查与限幅；`mecanum_kinematics.c:49` 的正解未被使用 | 速度下发能跑，但无法保证直线与里程精度  | 增加航向环、速度环、里程估计。 |
| `P1` | 电机反馈更新频率偏低 | `MotorManager_UpdateFeedback()` 每次只轮询一个电机；`chassis_control.c:138` 每 `50 ms` 才调用一次，因此四轮全量更新周期约 `200 ms` | 适合故障探测，不适合高质量闭环与里程估计 | 调整为每周期全轮读取，或提高总线调度策略。 |
| `P1` | IMU 运行期校准入口未开放给上位机 | `board_app.c:33-40` 有接口，但 `remote_cmd` 没有对应命令 | 实车调零、重新标定不方便 | 增加 `GYROCAL`、`ACCCAL`、`IMU?` 命令。 |

## 6. 对“陀螺仪、激光、麦轮稳定性”的判断

### 6.1 传感器回传现状

| 项目 | 现状 | 结论 | 修改方法 |
| --- | --- | --- | --- |
| 激光数据回传 | 已编译版本可通过 `STAT` 获得 `laser_ok`、`laser_warn`、`dist` | 具备简化回传  | 保持现状 |
| 陀螺仪数据回传 | 当前协议没有外发 yaw / gyro / calibration 状态 | 还不具备 | 小车、 |
| 全量 CSV 调试流 | `sensor_uart3_stream_test` 已写，但未编译且串口冲突 | 还不能直接使用 | 见文档[CSV模块修改任务书](../工程纠错/CSV模块修改任务书.md) 的细则 |
| | | | |

### 6.2 建议的传感器调试改造

| 优先级  | 改造项 | 建议 |
| ---- | --- | --- |
| `P0` | 传感器调试串口 | 把 `sensor_uart3_stream_test` 从 `USART3` 改到 `USART1(PA9/PA10)`，因为 `USART1` 当前只初始化未被业务使用。 |
| `P0` | 外部协议补充  | 在 `remote_cmd` 中新增 `IMU?`、`LASER?`、`SENS?`、`SENS_STREAM ON/OFF`，避免单独维护两套串口模块。 |
| `P1` | 上位机记录工具 | 用树莓派或 PC 记录 CSV，至少包含 `yaw`、`gyro_z`、`imu_calibrated`、`laser_raw`、`laser_filtered`、`target_vx/vy/wz`。 |

### 6.3 麦轮组运行稳定性判断

| 项目 | 现状判断 | 原因 |
| --- | --- | --- |
| 能不能动起来 | 可以 | 已有逆解、Modbus 下发、急停、超时停机。 |
| 能不能稳定做方向动作 | 可以做基础联调，但需要实测校向 | `g_motor_dir_sign` 默认全为 `1`，真实装车后通常要逐轮确认方向。 |
| 能不能稳定直线跑 | 不能直接下结论 | 当前没有用 IMU 或轮速反馈去纠偏。 |
| 能不能为写固定路径做准备 | 只能说“做了底层准备”，还没到“可以直接写路径”的阶段 | 缺少距离控制、航向控制、动作完成判据。 |

## 7. 陀螺仪零漂与累计误差是否能解决

| 问题 | 当前代码已有措施 | 能解决到什么程度 | 仍然缺什么 |
| --- | --- | --- | --- |
| 上电零漂 | `imu_app.c:72` 启动即调用 `JY61P_StartGyroCalibration()`；`jy61p.h:45` 设定 `200` 个样本；`jy61p.h:42` 采样周期 `10 ms` | 若上电时车体静止，约 `2 s` 后可得到较好的陀螺零偏均值 | 需要规范“上电静止”流程，并能让上位机看到 `imu_calibrated` 状态 |
| 航向归零 | `ZERO` 命令调用 `JY61P_ZeroYawReference()` | 可以把当前朝向重置为 `0` | 这只是参考系重置，不等于漂移被根治 |
| 累计误差 | `jy61p.c:183` 使用角度项 `0.02` 做航向融合 | 只能“抑制一部分漂移”，不能从工程上宣称“已经解决累计误差” | 缺少运行期重标定、温漂补偿、里程/外参融合、航向闭环 |
| 长距离直线 | 当前没有“以 yaw 误差修正 `wz`”的控制器 | 不能保证长距离直线 | 需要增加航向 PID、速度闭环、里程标定 |

### 结论

| 问题 | 结论 |
| --- | --- |
| 陀螺仪零漂能否解决 | 可以“通过静止标定显著减弱”，但不能简单认定为彻底解决。 |
| 陀螺仪累计误差能否解决 | 目前不能。当前代码只有基础融合与零点重置，没有完整的长期抑漂方案。 |
| 小车能否长距离直线行驶 | 现阶段不建议直接给出“可以”。最多只能做低速、短距离联调验证。 |

## 8. 激光近距离急停能力与急停距离判断

### 8.1 代码层急停条件

| 条目 | 代码依据 | 数值 |
| --- | --- | --- |
| 预警距离 | `atk_ms53l1m.h:21` | `600 mm` |
| 减速提示距离 | `atk_ms53l1m.h:22` | `300 mm` |
| 急停判定距离 | `atk_ms53l1m.h:23` | `150 mm` |
| 过近确认次数 | `atk_ms53l1m.h:27` | 连续 `2` 次 |
| 激光测量周期 | `atk_ms53l1m.c:221` | `50 ms` |
| 上层急停联锁 | `remote_cmd.c:168-195` | 激光无效或 `laser_warning >= 3` 立即锁车 |

### 8.2 可以实现什么

| 问题 | 结论 |
| --- | --- |
| 小车能否在激光识别近距离物体时急停 | 可以，前提是当前运动链路走的是 `RemoteCmd` 这条主流程，且激光在线。 |
| 急停是软件急停还是物理继电器断电 | 当前是软件/协议层急停，通过 `Mecanum_EmergencyStop()` 下发给电机。 |

### 8.3 “急停距离是多少”的准确回答

| 口径 | 结论 |
| --- | --- |
| 代码触发距离 | `150 mm` 过滤距离以内，且连续 `2` 次确认后触发 |
| 实际物理停止距离 | 不能仅靠源码给出，需要实车标定 |
| 为什么不能直接下结论 | 真实停止距离还受到 `50 ms` 测量周期、`2` 次确认延迟、主循环调度、Modbus 下发延迟、电机驱动器响应、车体惯性影响 |

### 8.4 按当前参数的理论接近量估算

| 车速 | 仅由“两次确认延迟”带来的额外接近量 |
| --- | --- |
| `0.05 m/s` | 约 `5 mm` |
| `0.20 m/s` | 约 `20 mm` |
| `0.60 m/s` | 约 `60 mm` |

上表还没有把串口发送延迟和机械惯性算进去，所以它只能作为“下限级估算”，不能代替实测。  
建议把“安全急停门限”先从 `150 mm` 提高到一个更保守的实测值，再做高速测试。

## 9. 现在是否适合开始“书写确定运行路径”

| 条件 | 当前状态 | 是否满足 |
| --- | --- | --- |
| 姿态可稳定获取 | 部分满足 | 有 yaw，但尚未闭环验证 |
| 距离可稳定控制 | 不满足 | 没有里程闭环 |
| 直线和转角可重复 | 不满足 | 还未完成底盘标定 |
| 急停边界已知 | 不满足 | 代码阈值已知，物理停止距离未知 |
| 传感器回传可记录分析 | 不满足 | 全量外部回传还没接通 |

### 结论

| 项目 | 判断 |
| --- | --- |
| 是否已经可以直接写固定路径 | 不建议 |
| 是否已经具备写路径前的底层准备 | 具备一部分，但必须先补齐标定、回传和闭环 |

## 10. 下一步工程架构方向：树莓派 + 两块 STM32

### 10.1 建议的职责分层

| 节点 | 主要职责 | 不建议承担的职责 |
| --- | --- | --- |
| 树莓派 | 视觉识别、目标理解、任务调度、路径规划、日志记录、上位机通信 | 直接做电机实时闭环、直接输出底层 PWM |
| 底盘 STM32 | IMU/激光采集、急停联锁、底盘速度闭环、路径动作原语执行 | 视觉推理、大量字符串处理 |
| 机械臂 STM32 | 关节控制、夹爪控制、限位/原点管理、动作执行反馈 | 视觉识别、全局任务规划 |

### 10.2 通信架构建议

| 阶段 | 建议方案 | 原因 |
| --- | --- | --- |
| 短期联调 | 树莓派 <-> 底盘 STM32：沿用 `USART2` 文本协议；树莓派 <-> 机械臂 STM32：独立 UART/USB-UART | 改动最小，最快出结果 |
| 中期稳定版 | 统一成“帧头 + 长度 + `msg_id` + `payload` + `CRC`”的二进制协议 | 文本协议便于联调，但不适合长期双板协同 |
| 长期扩展 | 形成“树莓派主控 + 两块 STM32 从控”的统一消息总线 | 便于新增传感器、机械臂状态和任务反馈 |

### 10.3 结合当前板级资源的建议

| 资源 | 现状 | 建议用途 |
| --- | --- | --- |
| `USART3 / PB10 PB11` | 已用于底盘电机 Modbus | 保持专用，不要再挂传感器调试流 |
| `USART2 / PA2 PA3` | 已用于 `RemoteCmd` | 作为树莓派到底盘 STM32 的主控制链路 |
| `USART1 / PA9 PA10` | 已初始化，但业务层未使用 | 优先给“调试回传”或“第二块 STM32 通道”使用 |

### 10.4 推荐的消息层划分

| 方向 | 建议消息 |
| --- | --- |
| 树莓派 -> 底盘 STM32 | `HB`、`SET_VEL`、`STOP`、`ESTOP`、`ZERO_YAW`、`RUN_SEGMENT`、`CLEAR_FAULT` |
| 底盘 STM32 -> 树莓派 | `STATUS`、`IMU`、`LASER`、`ODOM`、`FAULT`、`ESTOP_REASON` |
| 树莓派 -> 机械臂 STM32 | `HOME`、`SET_JOINTS`、`SET_POSE`、`GRIP_OPEN/CLOSE`、`PICK`、`PLACE` |
| 机械臂 STM32 -> 树莓派 | `ARM_STATUS`、`AT_TARGET`、`LIMIT`、`FAULT` |

### 10.5 项目目录方向建议

| 目录 | 内容 |
| --- | --- |
| `chassis_stm32/` | 当前底盘工程，继续负责底盘、IMU、激光、安全联锁 |
| `arm_stm32/` | 新建机械臂控制工程 |
| `rpi_controller/` | 视觉识别、任务规划、日志记录、双 STM32 通信 |
| `protocol/` | 通用消息定义、CRC、帧格式、命令枚举 |

## 11. 建议的执行顺序

| 顺序 | 任务 | 目标 |
| --- | --- | --- |
| `1` | 修正调试模块接入问题 | 让 `bringup_mode` 能编译，让传感器回传真正可用 |
| `2` | 打通 IMU/激光完整回传 | 能记录数据，才能判断零漂、滤波、急停门限 |
| `3` | 完成麦轮方向与参数标定 | 解决轮向、轮径、底盘几何参数误差 |
| `4` | 增加航向闭环与基础里程控制 | 让“小车能走直、能转准、能走指定距离” |
| `5` | 实测急停门限 | 把 `150 mm` 代码阈值转成真实安全距离 |
| `6` | 建立路径动作原语 | 例如“前进 X 米”“左移 X 米”“转角 θ” |
| `7` | 接入树莓派视觉 | 让树莓派只发任务与目标，不直接做底层闭环 |
| `8` | 新建机械臂 STM32 协议与控制 | 与底盘分层解耦，避免后期逻辑缠绕 |

## 12. 最终结论

| 问题 | 结论 |
| --- | --- |
| 这份工程现在可以实现什么 | 可以完成传感器基础采集、底盘速度控制、树莓派/上位机串口控车、激光联锁急停。 |
| 这份工程是否需要调整 | 需要，而且应先完成调试链路、传感器回传、底盘闭环和急停标定，再进入视觉与机械臂阶段。 |
| 陀螺仪零漂和累计误差能否解决 | 当前只能部分减弱，不能认定已彻底解决。 |
| 小车能否长距离直线行驶 | 以当前代码状态，不建议直接下这个结论。 |
| 小车能否对近距离物体急停 | 逻辑上可以；代码触发门限约为 `150 mm` 且连续 `2` 次确认，但真实停止距离必须实测。 |
| 下一步项目方向 | 树莓派做视觉与任务层，两块 STM32 分别负责底盘实时控制和机械臂实时控制，统一通信协议逐步从文本联调协议升级为二进制帧协议。 |
