Chemcrin/IntelligentTransformCart/代码/VibeCoding/Docs/CubeIDE导入与IOC配置.md

# CubeIDE 导入与 IOC 配置

## 新建工程

| 项目 | 配置 |
|---|---|
| IDE | STM32CubeIDE |
| 工程类型 | STM32 Project |
| MCU | 选择实际控制板芯片；当前代码按 STM32F1 HAL 编写 |
| 代码生成 | 建议开启 Generate peripheral initialization as pair of `.c/.h` files |

## IOC 外设配置

| 外设 | 配置项 | 推荐值 |
|---|---|---|
| I2C1 | Mode | I2C |
| I2C1 | SCL/SDA | PB6/PB7 |
| I2C1 | Speed | 100 kHz 起步，稳定后可试 400 kHz |
| I2C1 | 用途 | JY61P 地址 `0x50`，ATK-MS53L1M 地址 `0x29` |
| USART3 | Mode | Asynchronous |
| USART3 | TX/RX | PB10/PB11 |
| USART3 | Baud | 115200 |
| USART3 | Word/Parity/Stop | 8 bit / None / 1 stop |
| RS485_DIR GPIO | 默认 | 不配置、不占用 GPIO |
| SYS | Debug | Serial Wire |

## RS485 接线说明

| 项目 | 说明 |
|---|---|
| 官方接线方式 | 电机/驱动板接 `12-32V`、`GND`、`RS485_A`、`RS485_B` |
| MCU 侧 | 只需要 UART TX/RX 连接到 RS485 模块；模块输出 A/B 接电机总线 |
| 方向控制 | 默认不使用 `RS485_DIR`，代码中 `MODBUS_USE_RS485_DIR_GPIO` 为 `0u` |
| 何时才需要 GPIO | 如果换成普通 TTL-RS485 模块，且模块需要 MCU 控制 DE/RE，才配置方向脚 |

如果将来需要 DE/RE 方向脚，请在 CubeMX 中把某个 GPIO 命名为 `RS485_DIR`，并把 [mecanum_config.h](</C:/Users/CloudyRain/Documents/New project/smart_logistics_car_integrated/Core/Inc/mecanum_config.h>) 中：

```c
#define MODBUS_USE_RS485_DIR_GPIO         0u
```

改为：

```c
#define MODBUS_USE_RS485_DIR_GPIO         1u
```

## 需要加入的 Include Paths

| 路径 |
|---|
| `Core/Inc` |
| `Drivers/VL53L1X/core/inc` |
| `Drivers/VL53L1X/platform/inc` |

## 需要参与编译的源码

| 路径 |
|---|
| `Core/Src/*.c` |
| `Drivers/VL53L1X/core/src/*.c` |
| `Drivers/VL53L1X/platform/src/*.c` |

## main.c 合并方式

将 [main_integrated_example.c](</C:/Users/CloudyRain/Documents/New project/smart_logistics_car_integrated/Templates/main_integrated_example.c>) 的用户代码合并到 CubeMX 生成的 `Core/Src/main.c`：

| 区域 | 操作 |
|---|---|
| Includes | 增加 `board_app.h`、`sensor_bridge.h`、`mecanum.h`、`chassis_control.h` |
| Init | 在 `MX_GPIO_Init()`、`MX_I2C1_Init()`、`MX_USART3_UART_Init()` 后调用 `Board_App_Init()` 和 `Mecanum_Init(&huart3)` |
| while(1) | 按示例顺序调用 `Board_App_Loop()`、`Sensor_GetSnapshot()`、安全判断、`Mecanum_PeriodicTask()` |

## 烧录前检查表

| 检查项 | 标准 |
|---|---|
| I2C | PB6/PB7 上拉正常，JY61P 与 ATK-MS53L1M 地址不冲突 |
| RS485 | A/B 未接反；默认不需要 RS485 方向脚 |
| 电机地址 | FL/FR/RL/RR 分别为 `0x01/0x02/0x03/0x04` |
| 车轮 | 首次测试必须架空 |
| 急停 | 激光遮挡到 150 mm 内时底盘停止 |
