Chemcrin/IntelligentTransformCart/代码/VibeCoding/项目链接文档/工程变量总览.md

# 智能物流小车 工程变量总览

> 文档版本：V1.0  
> 最后更新：2026-05-26  
> 作    用：汇总各模块使用的变量名，避免命名冲突和歧义
> 各个工程间的整合桥接请参考文档 [[智能物流小车-传感器桥接层文档]] （将持续更新，现在是传感器与麦轮模块的整合）

---

## 目录

1. [IMU 传感器变量](#1-imu-传感器变量)
2. [激光测距变量](#2-激光测距变量)
3. [桥接层 API](#3-桥接层-api)
4. [运动学与控制变量](#4-运动学与控制变量)
5. [电机 Modbus 变量](#5-电机-modbus-变量)
6. [配置宏参数](#6-配置宏参数)
7. [跨模块变量对照表](#7-跨模块变量对照表)

---

## 1. IMU 传感器变量

**来源：** `board_app.h` / `board_app.c`（V3 GPT 代码，`ATK_JY_NewVer_GPT` 工程）  
**类型：** 全局变量，`volatile` 修饰，供中断和主循环共享  
**物理层：** I2C1 → JY61P

### 1.1 全局变量（推荐使用 g_ 前缀）

```c
// ===== 姿态角 =====
extern volatile float  g_imu_car_yaw_est_deg;    /* 融合偏航角，deg */
extern volatile float  g_imu_car_pitch_deg;       /* 俯仰角，deg */
extern volatile float  g_imu_car_roll_deg;        /* 横滚角，deg */

// ===== 角速度 =====
extern volatile float  g_imu_gyro_yaw_dps;        /* 偏航角速度，deg/s */

// ===== 加速度 =====
extern volatile float  g_imu_acc_forward_g;       /* 前向加速度，g */
extern volatile float  g_imu_acc_right_g;         /* 右向加速度，g */
extern volatile float  g_imu_acc_down_g;          /* 向下加速度，g */

// ===== 温度与状态 =====
extern volatile float  g_imu_temperature_c;        /* 温度，℃ */
extern volatile uint8_t g_imu_valid;               /* 数据有效标志 */
extern volatile uint8_t g_imu_calibrated;          /* 校准完成标志 */
```

### 1.2 兼容变量名（无 g_ 前缀，供旧代码过渡）

| 兼容名 | 映射到 | 说明 |
|---|---|---|
| `car_yaw_est_deg` | `g_imu_car_yaw_est_deg` | 建议新代码用 g_ 前缀 |
| `car_pitch_deg` | `g_imu_car_pitch_deg` | |
| `car_roll_deg` | `g_imu_car_roll_deg` | |
| `gyro_yaw_dps` | `g_imu_gyro_yaw_dps` | |
| `acc_forward_g` | `g_imu_acc_forward_g` | |
| `acc_right_g` | `g_imu_acc_right_g` | |
| `acc_down_g` | `g_imu_acc_down_g` | |
| `temperature_c` | `g_imu_temperature_c` | |
| `imu_valid` | `g_imu_valid` | |
| `imu_calibrated` | `g_imu_calibrated` | |

### 1.3 已移除的旧字段

V2.3 及之前版本中存在，V3 已移除的变量名（不再使用）：

| 移除的旧名 | 移除原因 |
| --- | --- |
| `imu.ax_g` / `imu.ay_g` / `imu.az_g` | 改为独立全局变量 `g_imu_acc_*_g` |
| `imu.gx_dps` / `imu.gy_dps` / `imu.gz_dps` | 代码只保留 yaw 轴角速度 |
| `imu.error_count` | 代码中已无此变量 |
| `imu.last_update_ms` | 代码中已无此变量 |

---

## 2. 激光测距变量

**来源：** `board_app.h` / `board_app.c`（V3 GPT 代码）  
**物理层：** I2C1 → ATK-MS53L1M / VL53L1X

### 2.1 全局变量

```c
// ===== 距离数据 =====
extern volatile uint16_t g_laser_raw_distance_mm;         /* 最新原始距离，mm */
extern volatile uint16_t g_laser_filtered_distance_mm;     /* 滤波后稳定距离，mm */
extern volatile uint16_t g_laser_distance_mm;              /* 对外输出距离，mm */

// ===== 状态标志 =====
extern volatile uint8_t  g_laser_valid;                   /* 距离数据是否有效 */
extern volatile uint8_t  g_laser_ok;                      /* 模块是否在线 */
extern volatile uint8_t  g_laser_is_warning;              /* 预警标志，< 600 mm */
extern volatile uint8_t  g_laser_is_slow;                 /* 减速标志，< 300 mm */
extern volatile uint8_t  g_laser_is_too_close;            /* 停车标志，< 150 mm */

// ===== 时间 =====
extern volatile uint32_t g_laser_last_valid_ms;           /* 最近有效距离的时间戳 */
```

### 2.2 预警等级对照

```c
// 三个标志位组合 → 等级
// g_laser_is_warning  | g_laser_is_slow  | g_laser_is_too_close  →  等级
//        0            |        0         |         0             →  0（正常）
//        1            |        0         |         0             →  1（预警）
//        1            |        1         |         0             →  2（减速）
//        1            |        1         |         1             →  3（停车）
```

---

## 3. 桥接层 API

**来源：** `sensor_bridge.h` / `sensor_bridge.c`  
**作用：** 将传感器层变量转换为运动控制层需要的单位（rad/m）

### 3.1 函数接口

```c
// ===== IMU =====
float  JY61P_GetYawRad(void);           // g_imu_car_yaw_est_deg * DEG_TO_RAD → rad
float  JY61P_GetGyroZRadS(void);        // g_imu_gyro_yaw_dps * DEG_TO_RAD → rad/s
float  JY61P_GetPitchDeg(void);         // g_imu_car_pitch_deg → deg（直传）
float  JY61P_GetRollDeg(void);          // g_imu_car_roll_deg → deg（直传）
bool   JY61P_IsDataValid(void);         // g_imu_valid → bool
bool   JY61P_IsCalibrated(void);        // g_imu_calibrated → bool

// ===== 激光 =====
bool   Laser_GetDistance(float *d);     // g_laser_filtered_distance_mm / 1000 → m
uint16_t Laser_GetRawDistanceMm(void);  // g_laser_raw_distance_mm → mm（直传）
uint8_t  Laser_GetWarningLevel(void);   // 三标志组合 → 0/1/2/3
bool   Laser_IsOnline(void);            // g_laser_ok → bool
```

### 3.2 快照结构体

```c
typedef struct {
    float    yaw_rad;           /* 偏航角，单位 rad       ← g_imu_car_yaw_est_deg */
    float    gyro_z_rads;       /* 角速度，单位 rad/s     ← g_imu_gyro_yaw_dps */
    float    pitch_deg;         /* 俯仰角，单位 deg       ← g_imu_car_pitch_deg */
    float    roll_deg;          /* 横滚角，单位 deg       ← g_imu_car_roll_deg */
    float    distance_m;        /* 激光距离，单位 m       ← g_laser_filtered_distance_mm */
    bool     imu_valid;         /* IMU 有效               ← g_imu_valid */
    bool     imu_calibrated;    /* IMU 已校准             ← g_imu_calibrated */
    bool     laser_valid;       /* 激光有效               ← g_laser_valid */
    uint8_t  laser_warning;     /* 预警等级 0-3           ← 三标志组合 */
} SensorSnapshot_t;

// 获取快照
void Sensor_GetSnapshot(SensorSnapshot_t *snap);
```

### 3.3 内部缓存变量

```c
// sensor_bridge.c 内部使用，不对外暴露
static SensorSnapshot_t s_snap_cache;    /* 快照缓存 */
static bool             s_snap_valid;    /* 缓存有效性 */
```

---

## 4. 运动学与控制变量

**来源：** 麦轮运动控制系统设计文档  
**作用：** 底盘运动学计算、状态管理

### 4.1 运动学结构体

```c
// ===== 底盘速度 =====
typedef struct {
    float vx;       /* x 方向速度，m/s */
    float vy;       /* y 方向速度，m/s */
    float omega;    /* 绕 z 轴角速度，rad/s */
} ChassisVel_t;

// ===== 轮速 =====
typedef struct {
    float wheel_rpm[4];     /* FL, FR, RL, RR，带符号 RPM */
} WheelRpm_t;
```

### 4.2 运动学函数

```c
/* 逆运动学：底盘速度 → 四个轮子 RPM */
void Mecanum_InverseKinematics(
    const ChassisVel_t *cmd,
    float yaw_rad,          /* 当前偏航角，rad（来自桥接层） */
    bool field_oriented,    /* true = 全局坐标系速度 */
    float rpm_limit,        /* RPM 限幅 */
    WheelRpm_t *out
);

/* 正运动学：四个轮子 RPM → 底盘速度估计 */
void Mecanum_ForwardKinematics(
    const float wheel_rpm[4],
    float *vx_est, float *vy_est, float *omega_est
);
```

### 4.3 姿态估计（桥接层 + 运动学）

```c
// pose_estimator.c
static float pose_x;          /* 全局 x 坐标，m */
static float pose_y;          /* 全局 y 坐标，m */
// pose.theta 直接由 JY61P_GetYawRad() 提供，不自行积分
```

### 4.4 运动控制状态机

```c
// chassis_control.c
typedef enum {
    CHASSIS_IDLE,
    CHASSIS_ALIGN,
    CHASSIS_MOVE,
    CHASSIS_SLOWDOWN,
    CHASSIS_ARRIVED,
    CHASSIS_STOP,
    CHASSIS_FAULT,
    CHASSIS_EMERGENCY_STOP
} ChassisState_t;

static ChassisState_t g_chassis_state;           /* 当前状态 */
static float          g_theta_ref;               /* 航向锁定目标角度，rad */
static float          g_vx_user, g_vy_user;      /* 用户目标速度，m/s */
static float          g_omega_user;              /* 用户目标角速度，rad/s */
```

### 4.5 控制参数

```c
/* 航向保持 PD */
static float Kp_yaw;           /* 航向比例系数 */
static float Kd_yaw;           /* 航向阻尼系数 */

/* 转向角度环 */
static float Kp_turn;          /* 转向比例系数 */
static float Kd_turn;          /* 转向阻尼系数 */

/* 沿墙距离 P */
static float Kp_wall;          /* 沿墙比例系数 */

/* 安全检测 */
static float theta_tol;        /* 到达角度容差，rad */
static float gyro_tol;         /* 到达角速度容差，rad/s */
```

---

## 5. 电机 Modbus 变量

**来源：** 麦轮运动控制系统设计文档 + ZDT_X57_V2 Modbus 手册  
**物理层：** USART1 → RS485 → Modbus-RTU → ZDT-X42-V2 电机驱动器

### 5.1 电机地址

```c
#define MOTOR_ADDR_FL    0x01      /* 前左轮 FL */
#define MOTOR_ADDR_FR    0x02      /* 前右轮 FR */
#define MOTOR_ADDR_RL    0x03      /* 后左轮 RL */
#define MOTOR_ADDR_RR    0x04      /* 后右轮 RR */
#define MOTOR_ADDR_BROAD 0x00      /* 广播地址 */
```

### 5.2 Modbus 寄存器地址

```c
// ===== 写寄存器 =====
#define ZDT_REG_SPEED_CTRL    0x00E6   /* 速度模式控制（4 个寄存器） */
//   Reg1 (0x00E6): 方向 CW=0x0000 / CCW=0x0001
//   Reg2 (0x00E7): 加速度 RPM/s, uint16
//   Reg3 (0x00E8): 速度 RPM, uint16
//   Reg4 (0x00E9): 同步标志 0x0000=立即 / 0x0100=缓存

#define ZDT_REG_ENABLE        0x00E0   /* 使能控制（2 个寄存器） */
//   Reg1 (0x00E0): 0xAB01=使能 / 0xAB00=失能
//   Reg2 (0x00E1): 同步标志

#define ZDT_REG_STOP          0x00FE   /* 立即停止（1 个寄存器） */
//   Reg1 (0x00FE): 0x9800=紧急停止

#define ZDT_REG_SYNC_TRIGGER  0x00FF   /* 同步触发（1 个寄存器） */
//   Reg1 (0x00FF): 0x6600=触发所有缓存

#define ZDT_REG_CHANGE_ID     0x00A2   /* 修改设备地址（2 个寄存器） */

// ===== 读寄存器 =====
#define ZDT_REG_SPEED_FB      0x0044   /* 实时转速反馈（2 个寄存器） */
//   Reg1 (0x0044): 符号 0=正 / 1=负
//   Reg2 (0x0045): 转速绝对值, uint16

#define ZDT_REG_SYSTEM_STATUS 0x0078   /* 系统状态参数（17 个寄存器） */
```

### 5.3 Modbus 功能码

```c
#define MODBUS_FUNC_READ  0x04   /* 读输入寄存器 */
#define MODBUS_FUNC_WRITE_SINGLE 0x06  /* 写单个寄存器 */
#define MODBUS_FUNC_WRITE_MULTI  0x10  /* 写多个寄存器 */
```

### 5.4 电机管理变量

```c
// motor_manager.c
static uint16_t g_motor_rpm_fb[4];           /* 四轮反馈转速, RPM */
static uint8_t  g_motor_online[4];           /* 四轮在线状态 */
static uint8_t  g_motor_fault[4];            /* 四轮故障标志 */
static uint32_t g_motor_comm_timeout_cnt[4]; /* 通信超时计数 */

// 方向标定
static int8_t motor_dir_sign[4];             /* +1 或 -1，实车标定 */

// 当前命令
static uint16_t g_motor_cmd_speed[4];        /* 当前下发的目标转速 */
static uint8_t  g_motor_cmd_dir[4];          /* 当前下发的方向 */

// 缩放系数
static float ZDT_SPEED_MODE_SCALE;           /* 默认 1.0，联调后确认 */
static float ZDT_SPEED_FEEDBACK_SCALE;       /* 默认 1.0，联调后确认 */
```

### 5.5 Modbus 桥接中间变量

```c
// modbus_rtu.c
static uint8_t  modbus_tx_buf[32];           /* 发送缓冲区 */
static uint8_t  modbus_rx_buf[32];           /* 接收缓冲区 */
static uint16_t modbus_tx_len;               /* 发送长度 */
static uint16_t modbus_rx_len;               /* 已接收长度 */
static uint8_t  modbus_addr;                 /* 当前请求的目标地址 */

// Modbus 事务状态机
typedef enum {
    MB_IDLE,
    MB_BUILD,
    MB_TX_EN,
    MB_TX_SEND,
    MB_WAIT_TC,
    MB_RX_EN,
    MB_WAIT_RESP,
    MB_PARSE,
    MB_DONE,
    MB_ERROR,
    MB_GAP
} ModbusState_t;

static ModbusState_t g_modbus_state;
```

---

## 6. 配置宏参数

**来源：** 各模块的配置头文件

### 6.1 机械参数

```c
/* ===== 麦克纳姆轮底盘 ===== */
#define MECANUM_WHEEL_DIAMETER_M    0.075f     /* 轮径，m */
#define MECANUM_TRACK_WIDTH_M       0.320f     /* 轮距，m */
#define MECANUM_WHEEL_BASE_M        0.220f     /* 轴距，m */
#define MECANUM_K_M                 0.270f     /* 旋转耦合臂长，(L+W)/2 */
```

### 6.2 通信参数

```c
#define MODBUS_BAUDRATE             115200     /* Modbus 波特率 */
#define MODBUS_INTER_FRAME_GAP_MS   1u         /* 帧间保护间隔，ms */
#define MODBUS_RESPONSE_TIMEOUT_MS  5u         /* 响应超时，ms */
```

### 6.3 控制周期

```c
#define CHASSIS_CTRL_PERIOD_MS      20u        /* 主控制周期，ms */
#define MOTOR_FEEDBACK_PERIOD_MS    40u        /* 四轮反馈轮询周期，ms */
#define LASER_UPDATE_PERIOD_MS      50u        /* 激光数据更新周期，ms */
```

### 6.4 运动限制

```c
#define RPM_LIMIT                   500        /* 最大轮速限制，RPM */
#define OMEGA_LIMIT                 3.14f      /* 最大角速度，rad/s */
#define ACC_LIMIT_RPM_S             2000       /* 最大轮加速度，RPM/s */
```

### 6.5 传感器阈值

```c
/* 激光距离阈值（与 g_laser_is_* 对应） */
#define LASER_WARNING_MM            600        /* 预警阈值，mm */
#define LASER_SLOW_MM               300        /* 减速阈值，mm */
#define LASER_STOP_MM               150        /* 停车阈值，mm */

/* 姿态异常阈值 */
#define POSE_ABNORMAL_PITCH_DEG     12.0f      /* 俯仰异常阈值，deg */
#define POSE_ABNORMAL_ROLL_DEG      12.0f      /* 横滚异常阈值，deg */
```

### 6.6 其他配置

```c
#define PI                          3.14159265f
#define DEG_TO_RAD                  0.01745329252f
#define RAD_TO_DEG                  57.29577951f
```

---

## 7. 跨模块变量对照表

### 7.1 从传感器层到运动控制层

| 传感器层全局变量 | 桥接层 API | 运动控制层使用 | 单位变化 |
|---|---|---|---|
| `g_imu_car_yaw_est_deg` | `JY61P_GetYawRad()` | 航向保持、转向 | deg → rad |
| `g_imu_gyro_yaw_dps` | `JY61P_GetGyroZRadS()` | 角速度阻尼 | deg/s → rad/s |
| `g_imu_car_pitch_deg` | `JY61P_GetPitchDeg()` | 姿态安全检测 | deg 不变 |
| `g_imu_car_roll_deg` | `JY61P_GetRollDeg()` | 姿态安全检测 | deg 不变 |
| `g_laser_filtered_distance_mm` | `Laser_GetDistance()` | 距离限速、沿墙 | mm → m |
| `g_laser_is_too_close` | `Laser_GetWarningLevel()` | 紧急停车 | 标志 → 等级 |
| `g_imu_valid` | `JY61P_IsDataValid()` | 控制有效性判断 | uint8 → bool |
| `g_imu_calibrated` | `JY61P_IsCalibrated()` | 初始化状态检查 | uint8 → bool |

### 7.2 从运动控制层到 Modbus

| 运动控制变量 | 桥接转换 | Modbus 寄存器 |
|---|---|---|
| `ChassisVel_t.vx` | 逆运动学 → `WheelRpm_t` | `0x00E6 Reg3`（转速） + `Reg1`（方向） |
| `ChassisVel_t.vy` | 同上 | 同上 |
| `ChassisVel_t.omega` | 同上 | 同上 |
| 同步触发命令 | — | `0x00FF` 广播 `0x6600` |
| 紧急停止 | — | `0x00FE` 广播 `0x9800` |

### 7.3 物理层引脚

| 外设 | 传感器层（V3） | 运动控制层 | 备注 |
|---|---|---|---|
| I2C1 | PB6(SCL) / PB7(SDA) | 不直接使用 | JY61P + VL53L1X 共用 |
| USART1 | PA9(TX) / PA10(RX) | Modbus 通信（经 RS485） | 电机控制链路 |
| USART2 | PA2(TX) / PA3(RX) | 树莓派通信（经 CH340N） | 暂不涉及运动控制 |

---

## 变更记录

| 版本 | 日期 | 变更 |
|---|---|---|
| V1.0 | 2026-05-26 | 初始版本，汇总传感器层、桥接层、运动控制层、Modbus 所有变量 |
