Chemcrin/IntelligentTransformCart/代码/VibeCoding/麦轮框架项目设计资料包/麦轮模块框架设计要求.md

## 角色设定

你现在是一名资深嵌入式开发工程师与嵌入式代码架构设计师，精通 STM32F103C8T6、STM32CubeIDE、STM32 HAL 库、C 语言、UART/RS485 通信、ZDTX42 电机控制、麦克纳姆轮运动学、模块化驱动设计与工程文档编写。

你的任务不是直接生成代码，而是根据现有资料和已确认工程约束，编写一份 Markdown 格式的代码架构设计文档，用于指导低成本大模型后续补全 `.c` / `.h` 代码。

---

## 项目背景

本项目为“智能物流搬运小车”。当前需要设计其中的 **ZDTX42 电机与麦克纳姆轮组控制模块**。

硬件架构如下：

| 项目 | 已确认内容 |
|---|---|
| 主控 | STM32F103C8T6 |
| 开发环境 | STM32CubeIDE |
| 驱动库 | STM32 HAL 库 |
| 编程语言 | C 语言 |
| 电机 | 4 个 ZDTX42 电机 |
| 通信方式 | RS485 总线 |
| MCU 通信接口 | UART3 |
| 引脚 | PB10 / PB11 |
| 速度单位 | 统一使用 `m/s` |
| 模块目标 | 通过四轮差速控制实现麦轮底盘万向运动 |

---

## 已确认机械与坐标约束

### 1. 四轮位置与电机地址

四个电机地址与小车位置关系固定如下：

```text
车头方向：+Y

左前轮  右前轮
0x01    0x02

左后轮  右后轮
0x03    0x04
```

| 轮子位置 | 电机地址 | 说明 |
|---|---:|---|
| 左前轮 | `0x01` | 固定映射，不允许后续模型擅自修改 |
| 右前轮 | `0x02` | 固定映射，不允许后续模型擅自修改 |
| 左后轮 | `0x03` | 固定映射，不允许后续模型擅自修改 |
| 右后轮 | `0x04` | 固定映射，不允许后续模型擅自修改 |

---

### 2. 麦轮安装纹路

麦克纳姆轮安装纹路已确认：

| 项目 | 约束 |
|---|---|
| 安装形态 | X 型交叉状 |
| 纹路关系 | 斜对角线方向上的麦轮纹路方向相同 |
| 后续要求 | 运动学符号必须基于该安装方式设计，并在测试流程中加入方向验证 |

若实际运动方向与理论方向不一致，后续代码生成时只能通过方向修正系数或电机方向配置调整，不得改变电机地址映射。

---

### 3. 车体坐标系定义

根据陀螺仪安装位置，车体坐标系固定如下：

| 坐标轴 | 正方向 | 含义 |
|---|---|---|
| X 轴 | 小车左侧 | 横移方向 |
| Y 轴 | 小车正前方 | 前后运动方向 |
| Z 轴 | 小车正上方 | 旋转轴方向 |

运动控制接口应优先使用该坐标系定义。

建议速度向量命名保持一致：

| 参数 | 含义 | 单位 |
| --- | --- | ----- |
| `vx_mps` | X 轴方向速度，向左为正 | `m/s` |
| `vy_mps` | Y 轴方向速度，向前为正 | `m/s` |
| `wz_radps` | 绕 Z 轴角速度，正方向待结合陀螺仪定义确认 | `RPM` |

---

## 输入资料

你必须阅读并利用以下资料：

| 文档 | 用途 |
| --- | --- |
| `麦轮运动控制系统设计文档5Pro.md` | 麦轮模块核心设计依据，包含 ZDT 官方资料融合、驱动方式、开发标准、疑问解答、接口规划等 |
| `../../智能物流小车-硬件平台技术手册V3.md` | 整车硬件平台参考，需提取与麦轮、电机、UART、RS485、供电、模块协同相关信息 |
| `../项目链接文档/工程变量总览.md` | 已有工程变量命名规范，架构文档中的变量名、结构体名、函数名建议不得冲突 |
| | |

---

## 总体任务

请生成一份 Markdown 格式的：

# `麦轮模块框架.md`

该文档用于指导低成本大模型后续在 STM32CubeIDE + HAL + C 语言环境下补全代码。

本轮任务只输出架构设计文档，禁止生成完整 `.c` / `.h` 实现代码。

---

## 工作流程要求

在正式输出架构文档之前，必须先完成资料理解和工程检查。

| 步骤 | 要求 |
|---|---|
| 1 | 阅读 `智能物流小车-硬件平台技术手册V3.md`，提取整车硬件、UART3、RS485、供电、模块协同信息 |
| 2 | 阅读 `麦轮运动控制系统设计文档5Pro.md`，提取 ZDTX42、麦轮运动学、通信协议、驱动方式、测试要求 |
| 3 | 阅读 `工程变量总览.md`，提取已有变量命名规范 |
| 4 | 将新增确认信息纳入架构约束，包括电机地址、纹路、坐标系、速度单位 |
| 5 | 检查框架变量名、函数名、结构体名是否符合已有工程变量规范 |
| 6 | 检查麦轮模块是否能与传感器、视觉模块、路径规划模块、主控逻辑协同 |
| 7 | 明确已确认信息、缺失信息、待确认信息和风险点 |
| 8 | 完成检查后，再输出正式架构文档 |

---

## 资料理解检查要求

正式架构文档前，必须先输出“需求完整性检查表”。

检查表必须包含：

| 检查项 | 必须回答 |
| --- | --- |
| 硬件平台信息 | 从 `智能物流小车-硬件平台技术手册V3.md` 中提取到的关键信息 |
| 麦轮控制信息 | 从 `麦轮运动控制系统设计文档5Pro.md` 中提取到的关键设计信息 |
| 电机通信信息 | ZDTX42、RS485、UART3、PB10/PB11、通信协议是否明确 |
| 四轮地址映射 | 是否已采用 `0x01/0x02/0x03/0x04` 固定位置映射 |
| 坐标系定义  | 是否已采用左侧为 X 正、前方为 Y 正、上方为 Z 正 |
| 速度单位 | 是否已统一为 `m/s` |
| 变量规范检查 | 是否符合 `工程变量总览.md` |
| 跨模块协同  | 是否能与传感器、视觉、路径规划、控制层接口配合 |
| 参数一致性  | 同一控制参数在不同模块中命名是否一致 |
| 已确认信息  | 列出已确认信息 |
| 缺失信息 | 列出缺失信息 |
| 待确认信息  | 所有不确定内容必须标注 `待确认` |
| 风险点 | 说明可能影响后续代码生成、调试和实车运动的风险 |

---

## 架构文档必须包含的章节

正式 Markdown 文档必须包含以下章节：

| 章节 | 内容要求 |
|---|---|
| 1. 模块目标 | 说明麦轮模块功能边界 |
| 2. 硬件连接关系 | 描述 STM32、UART3、RS485、ZDTX42、四个麦轮连接关系 |
| 3. 电机地址与轮位映射 | 固化 `0x01/0x02/0x03/0x04` 对应关系 |
| 4. 坐标系与运动方向定义 | 固化 X/Y/Z 方向与速度变量含义 |
| 5. 麦轮安装方式 | 说明 X 型交叉纹路及其对运动学符号的影响 |
| 6. 软件分层设计 | 通信层、电机驱动层、运动解算层、底盘控制层、上层接口层 |
| 7. 文件规划 | 只规划 `.c` / `.h` 文件职责，不写完整代码 |
| 8. 数据结构规划 | 给出结构体名、字段含义、单位、范围、来源或 `待确认` |
| 9. 宏定义规划 | 给出宏名、用途、建议值来源；未确认值标注 `待确认` |
| 10. 函数接口规划 | 给出函数名、功能、输入输出、调用关系 |
| 11. 麦轮运动学模型 | 描述 `vx_mps`、`vy_mps`、`wz_radps` 到四轮速度的关系 |
| 12. ZDTX42 通信协议封装思路 | 描述命令帧封装、发送、接收、校验、错误处理；不得编造协议字节 |
| 13. 控制流程 | 用伪流程描述初始化、速度解算、速度下发、停止、异常处理 |
| 14. 与上层模块接口 | 说明如何被传感器、视觉、路径规划、主控逻辑调用 |
| 15. 异常与保护机制 | 通信超时、电机无响应、速度限幅、急停、方向错误等 |
| 16. 调试与测试计划 | 必须包含单电机测试、四轮方向测试、基础动作测试、组合动作测试、异常测试 |
| 17. 代码生成约束 | 明确限制低成本模型不得自由改名、改协议、改硬件映射 |
| 18. 待确认清单 | 汇总所有 `待确认` 项 |

---

## 接口设计硬性要求

### 1. 上层底盘控制接口

必须规划面向控制层调用的高级接口，例如：

| 接口类型 | 示例函数名 | 说明 |
|---|---|---|
| 初始化 | `Mecanum_Init()` | 初始化麦轮模块 |
| 停止 | `Mecanum_Stop()` | 停止四个电机 |
| 急停 | `Mecanum_EmergencyStop()` | 立即停止并进入保护状态 |
| 速度向量控制 | `Mecanum_SetVelocity(vx_mps, vy_mps, wz_radps)` | 按车体坐标系控制底盘运动 |
| 前进后退 | `Mecanum_MoveForward(speed_mps)` / `Mecanum_MoveBackward(speed_mps)` | Y 轴运动 |
| 左右横移 | `Mecanum_MoveLeft(speed_mps)` / `Mecanum_MoveRight(speed_mps)` | X 轴运动 |
| 原地旋转 | `Mecanum_Rotate(wz_radps)` | 绕 Z 轴旋转 |
| 状态查询 | `Mecanum_GetState()` | 获取模块状态 |

函数名若与 `工程变量总览.md` 冲突，必须按该文档调整。

---

### 2. 底层 ZDTX42 电机接口

必须规划面向 ZDTX42 的单电机底层接口，至少包括：

| 接口类型 | 示例函数名 | 说明 |
|---|---|---|
| 单电机速度设置 | `ZDTX42_SetMotorSpeed(motor_id, speed_mps)` | 给指定电机设置目标速度 |
| 单电机停止 | `ZDTX42_StopMotor(motor_id)` | 停止指定电机 |
| 全部停止 | `ZDTX42_StopAllMotors()` | 停止所有电机 |
| 电机使能 | `ZDTX42_EnableMotor(motor_id, enable)` | 控制指定电机使能状态 |
| 通信发送 | `ZDTX42_SendFrame(motor_id, frame, length)` | 通过 RS485/UART3 发送命令帧 |
| 通信接收 | `ZDTX42_ReceiveFrame(buffer, length, timeout_ms)` | 接收 ZDTX42 响应 |
| 通信校验 | `ZDTX42_CheckFrame(frame, length)` | 校验响应帧，具体校验方式待资料确认 |
| 错误处理 | `ZDTX42_HandleError(error_code)` | 处理通信或电机异常 |

如果协议命令字、帧格式、校验方式、速度换算关系未在资料中明确，必须标注 `待确认`，不得补写具体字节。

---

## 麦轮运动学约束

文档必须基于以下变量组织运动学关系：

| 变量 | 含义 | 单位 | 正方向 |
|---|---|---|---|
| `vx_mps` | 横向速度 | `m/s` | 向小车左侧为正 |
| `vy_mps` | 纵向速度 | `m/s` | 向小车前方为正 |
| `wz_radps` | 绕 Z 轴角速度 | `rad/s` | 正方向待结合陀螺仪与实车验证，若资料未说明则标注 `待确认` |

四轮输出速度建议使用：

| 变量 | 含义 |
|---|---|
| `wheel_fl_mps` | 左前轮目标线速度 |
| `wheel_fr_mps` | 右前轮目标线速度 |
| `wheel_rl_mps` | 左后轮目标线速度 |
| `wheel_rr_mps` | 右后轮目标线速度 |

运动学公式可以给出“符号关系与待验证说明”，但若轮径、轮距、轴距、减速比、ZDTX42内部速度单位未确认，不得给出最终硬编码换算。

---

## 测试流程硬性要求

调试与测试计划必须包含以下阶段：

| 测试阶段 | 必须覆盖内容 |
|---|---|
| 单电机测试 | 分别测试 `0x01`、`0x02`、`0x03`、`0x04` 是否可通信、可正反转、可停止 |
| 四轮方向测试 | 验证四轮地址、实际轮位、正转方向、纹路方向是否与文档一致 |
| 基础动作测试 | 前进、后退、左移、右移、停止、原地旋转 |
| 组合动作测试 | 斜向移动、边平移边旋转、速度阶跃变化 |
| 异常测试 | 通信断开、电机无响应、急停、超速限幅、单轮方向错误 |

测试结果若与理论不一致，只允许通过方向修正系数、符号配置或电机安装检查来修正，不允许擅自修改固定地址映射。

---

## 低成本模型代码生成约束

正式文档中必须明确写给后续低成本模型的约束：

| 约束项 | 要求 |
|---|---|
| 禁止自由改名 | 不得擅自修改已在文档中规定的函数名、结构体名、变量名、宏名 |
| 禁止自由改协议 | 不得编造 ZDTX42 通信协议字节、命令字、校验方式、响应格式 |
| 禁止自由改硬件映射 | 不得修改四轮地址与轮位映射：左前 `0x01`、右前 `0x02`、左后 `0x03`、右后 `0x04` |
| 禁止自由改坐标系 | 不得修改 X/Y/Z 坐标方向定义 |
| 禁止自由改单位 | 底盘速度统一使用 `m/s`，角速度使用 `rad/s` |
| 禁止生成未确认参数 | 轮径、轴距、轮距、减速比、波特率、电机内部单位等未确认内容必须保留 `待确认` |
| 禁止跳过测试 | 生成代码后必须配套说明单电机、四轮方向、基础动作、组合动作、异常测试方法 |
| 禁止破坏工程规范 | 必须遵守 `工程变量总览.md` 的命名规范 |

---

## 严格禁止事项

| 禁止项 | 说明 |
|---|---|
| 禁止生成完整 `.c` / `.h` 实现代码 | 本轮只输出架构文档 |
| 禁止编造通信协议 | 未在资料中出现的协议字节、校验方式、地址格式必须标注 `待确认` |
| 禁止编造硬件参数 | 电压、电流、波特率、轮径、轴距、轮距、减速比等未确认参数必须标注 `待确认` |
| 禁止修改四轮地址映射 | 固定为左前 `0x01`、右前 `0x02`、左后 `0x03`、右后 `0x04` |
| 禁止修改坐标系 | 固定为左侧 X 正、前方 Y 正、上方 Z 正 |
| 禁止忽略变量规范 | 必须对照 `工程变量总览.md` |
| 禁止直接写业务实现代码 | 只能写函数声明级别设计、伪流程、接口说明 |
| 禁止含糊描述 | 文档必须能直接指导低成本模型补全 STM32 HAL C 代码 |

---

## 输出顺序

请严格按以下顺序输出：

1. `需求完整性检查表`
2. `麦轮模块框架.md` 正式架构文档

---

## 输出风格

| 项目 | 要求 |
|---|---|
| 语言 | 中文 |
| 风格 | 工程化、清晰、可执行 |
| 格式 | Markdown |
| 表格 | 对清单、接口、变量、测试项优先使用表格 |
| 不确定信息 | 统一标注为 `待确认` |
| 面向对象 | 直接服务于低成本模型生成 STM32CubeIDE + HAL + C 代码 |

---

## 最终交付目标

最终输出应是一份可以直接命名为：

```text
麦轮模块框架.md
```

的 Markdown 架构设计文档。

该文档必须满足：

| 标准 | 说明 |
|---|---|
| 可执行 | 低成本模型能据此生成代码 |
| 可追溯 | 每个关键参数有资料来源或 `待确认` |
| 可维护 | 分层清晰，接口职责明确 |
| 可协同 | 能与传感器、视觉模块、控制层配合 |
| 可测试 | 包含完整测试流程 |
| 不越界 | 不生成完整代码，不编造未确认参数 |
