Chemcrin/IntelligentTransformCart/代码/VibeCoding/项目链接文档/工程整合指南.md

# 智能物流小车 工程整合指南

> 文档版本：V1.0  
> 最后更新：2026-05-26  
> 作用：基于 GPT 版传感器工程（ATK_JY_NewVer_GPT），整合桥接层与麦轮运动控制

---

## 1. 整体架构

```
主循环 (while(1))
    │
    ├── Board_App_Loop()
    │       ├── IMU_App_Loop()      ← 读 JY61P → 更新全局变量 g_imu_*
    │       └── Laser_App_Loop()    ← 读 VL53L1X → 更新全局变量 g_laser_*
    │
    ├── Sensor_GetSnapshot()        ← 桥接层：deg→rad, mm→m → SensorSnapshot_t
    │
    ├── Chassis_ControlTask()       ← 运动控制层（新建）
    │       ├── 读快照 → 航向保持 / 距离限速 / 安全检测
    │       └── Mecanum_InverseKinematics() → WheelRpm_t
    │
    └── Motor_Manager_Send()       ← Modbus：将轮速发到四轮电机
```

---

## 2. 文件清单（新工程需要有的文件）

### 2.1 来自 GPT 版（已有，不要动）

| 文件 | 路径 | 作用 |
|---|---|---|
| `jy61p.c` / `jy61p.h` | `Core/Src` / `Core/Inc` | JY61P I2C 驱动（硬件读写 + 滤波 + 校准） |
| `imu_app.c` / `imu_app.h` | 同上 | IMU 应用层，同步全局变量 `g_imu_*` |
| `atk_ms53l1m.c` / `atk_ms53l1m.h` | 同上 | VL53L1X I2C 驱动 |
| `laser_app.c` / `laser_app.h` | 同上 | 激光应用层，同步全局变量 `g_laser_*` |
| `board_app.c` / `board_app.h` | 同上 | 板级聚合，`Board_App_Loop()` 统一调度 |

### 2.2 桥接层（新建 ✅ 已写完）

| 文件 | 路径 | 作用 |
|---|---|---|
| `sensor_bridge.c` / `sensor_bridge.h` | `Core/Src` / `Core/Inc` | 单位转换，SensorSnapshot_t |

### 2.3 运动控制层（需从零新建）

| 文件 | 路径 | 作用 |
|---|---|---|
| `mecanum_kinematics.c` / `.h` | `Core/Src` / `Core/Inc` | 麦克纳姆轮正/逆运动学 |
| `chassis_control.c` / `.h` | `Core/Src` / `Core/Inc` | 底盘控制状态机 + 安全逻辑 |
| `motor_manager.c` / `.h` | `Core/Src` / `Core/Inc` | Modbus 电机管理（发送/接收） |
| `modbus_rtu.c` / `.h` | `Core/Src` / `Core/Inc` | Modbus-RTU 协议层 |

---

## 3. 在 CubeIDE 中的添加步骤

### 第 1 步：新建 STM32 工程

- 以 GPT 版工程为基础直接复制一份
- 或者新建 CubeMX 工程后，把 GPT 版的 `Core/Src` 和 `Core/Inc` 文件全部拷贝进去
- **注意保持** `main.h` 中 I2C1 的配置（PB6/PB7）

### 第 2 步：添加桥接层文件

将 `sensor_bridge.c` 复制到 `Core/Src/`，`sensor_bridge.h` 复制到 `Core/Inc/`

### 第 3 步：在 CubeIDE 中将新文件加入编译

```
Project → Properties → C/C++ Build → Settings → MCU GCC Compiler → Include paths
添加：Core/Inc

然后在 Project Explorer 中右键 Core/Src → Add Files... 添加新的 .c 文件
```

### 第 4 步：修改 main.c

```c
#include "board_app.h"
#include "sensor_bridge.h"
// #include "chassis_control.h"    // 后续添加

int main(void)
{
    HAL_Init();
    SystemClock_Config();
    MX_GPIO_Init();
    MX_I2C1_Init();
    MX_USART1_UART_Init();      /* Modbus 用 */
    // MX_USART2_UART_Init();    /* 树莓派通信，可选 */

    Board_App_Init();            /* 初始化 IMU + 激光 */

    while (1)
    {
        Board_App_Loop();        /* 更新传感器数据 */

        SensorSnapshot_t snap;
        Sensor_GetSnapshot(&snap);  /* 桥接层：获取单位转换后的快照 */

        /* 在这里插入 Chassis_ControlTask(&snap) */

        HAL_Delay(10);           /* 约 100 Hz 主循环 */
    }
}
```

---

## 4. 传感器数据流验证

加完桥接层后，先在 main loop 里验证数据是否畅通：

```c
// main.c —— 验证代码
void Debug_PrintSnapshot(void)
{
    SensorSnapshot_t snap;
    Sensor_GetSnapshot(&snap);

    printf("yaw=%.1f deg (%.3f rad), ", snap.yaw_rad * 57.3f, snap.yaw_rad);
    printf("gyro_z=%.1f dps (%.3f rad/s), ", snap.gyro_z_rads * 57.3f, snap.gyro_z_rads);
    printf("dist=%.0f mm (%.3f m), ", snap.distance_m * 1000.0f, snap.distance_m);
    printf("warning=%d, imu_ok=%d, laser_ok=%d\r\n",
           snap.laser_warning, snap.imu_valid, snap.laser_valid);
}
```

预期输出（转车时）：
```
yaw=45.2 deg (0.789 rad), gyro_z=12.5 dps (0.218 rad/s), dist=320 mm (0.320 m), warning=2, imu_ok=1, laser_ok=1
```

---

## 5. 后续开发路线图

```
阶段 1 ─── 传感器验证（本周）
    ✅ 确认 I2C 正常通信
    ✅ 确认 g_imu_car_yaw_est_deg 随车转动变化
    ✅ 确认 g_laser_filtered_distance_mm 随距离变化
    ✅ 桥接层验证：Sensor_GetSnapshot() 返回值正确
                      ↓
阶段 2 ─── 电机控制（下周）
    □ USART1 → RS485 → Modbus 通信调通
    □ 单电机正反转 + 速度控制
    □ 四电机广播同步
    □ motor_manager 流程验证
                      ↓
阶段 3 ─── 运动学 + 状态机（再下周）
    □ Mecanum_InverseKinematics 算法验证
    □ Chassis_ControlTask 状态机
    □ 航向保持 PD 调参
    □ 激光距离限速 + 安全停障
                      ↓
阶段 4 ─── 整机联调
    □ 直行/后退
    □ 横移
    □ 原地旋转
    □ 航向保持直行
    □ 遇障停车
```

---

## 6. 注意事项

| 注意点 | 说明 |
|---|---|
| **I2C 总线** | JY61P + VL53L1X 共用 I2C1（PB6/PB7），不要同时占用 |
| **IMU 安装方向** | GPT 版默认 +Y 向前，+X 向右。如果实际安装方向不同，改 `jy61p.h` 中的 `JY61P_SIGN_CAR_*` 宏 |
| **Modbus 优先级** | 电机控制通过 USART1 走 RS485，和传感器 I2C 两条独立链路，不冲突 |
| **主循环频率** | 建议 50~100 Hz（10~20 ms），太快则 I2C 频繁读取可能增加噪声 |
| **快照一致性** | `Board_App_Loop()` 先更新传感器，`Sensor_GetSnapshot()` 紧接着读取，保证快照内所有数据来自同一时刻 |
| **调试串口** | 建议用 USART2（PA2/PA3）接 CH340N 打印调试信息，不干扰 USART1 的 Modbus 通信 |

---

## 变更记录

| 版本 | 日期 | 变更 |
|---|---|---|
| V1.0 | 2026-05-26 | 初始版本，整合 GPT 版 + 桥接层 + 麦轮运动控制 |
