Chemcrin/IntelligentTransformCart/代码/VibeCoding/姿态模块资料包/传感器代码架构设计_决策标注版.md

# JY61P 与 ATK-MS53L1M / VL53L1X 传感器模块代码架构设计文档（决策标注版）

> 项目：智能物流搬运小车  
> 主控：STM32C8T6，按 STM32F103C8T6 类资源进行架构设计  
> 开发环境：STM32CubeIDE 1.19.0、STM32 HAL、C 语言  
> 本文档边界：只输出 Markdown 架构设计，不生成 `.c` / `.h` 完整实现代码。  
> 标注规则：凡资料或需求未完全明确、但为了后续代码实现必须确定的内容，均使用 `【已决策，需验证】` 标注。

---

## 0. 代决策标注清单

| 编号 | 不清晰点 | 本文决策 | 标注 |
|---|---|---|---|
| D-01 | “STM32C8T6”具体完整型号未展开 | 架构按 STM32F103C8T6 类资源处理，外设名使用 STM32F1 HAL 常见命名 | 【已决策，需验证】 |
| D-02 | JY61P 的 Z 轴方向未由用户明确说明 | 默认 JY61P 板面朝上，软件中预留符号宏修正 Z 轴和 yaw 方向 | 【已决策，需验证】 |
| D-03 | JY61P 姿态角与车体系 Roll/Pitch/Yaw 的映射存在安装旋转 | 以“+Y 朝前、+X 朝右”为准，输出车体系姿态字段，不直接让上层使用 JY61P 原始 Roll/Pitch | 【已决策，需验证】 |
| D-04 | JY61P 累计误差无法靠单一算法彻底消除 | 使用上电静止零偏校准、运行中零速更新、分段航向归零、互补滤波、控制误差限幅组合抑制 | 【已决策，需验证】 |
| D-05 | 是否使用卡尔曼滤波 | 默认不使用卡尔曼滤波；采用一阶低通、互补滤波、中值滤波、滑动平均和异常值剔除 | 【已决策，需验证】 |
| D-06 | ATK-MS53L1M 官方资料与 VL53L1X 直连关系 | 直接按 VL53L1X 直连 I2C 设备设计，模块命名保留 `ms53l1m_`，底层语义按 VL53L1X | 【已决策，需验证】 |
| D-07 | VL53L1X 初始化细节是否展开 | 不展开 ID、Long 模式、Timing Budget、Inter-measurement 等寄存器细节，只保留“默认启动封装”接口 | 【已决策，需验证】 |
| D-08 | 电机 UART1 协议未提供 | 传感器层不定义电机协议，只提供传感器快照和安全标志给运动控制层；电机层通过 UART1 PA9/PA10 自行发送命令 | 【已决策，需验证】 |
| D-09 | I2C 总线恢复是否允许重新初始化 I2C1 | 允许统一传感器层在故障恢复时调用 HAL I2C DeInit/Init 或重新进入 `MX_I2C1_Init()` | 【已决策，需验证】 |
| D-10 | I2C 上拉到 5V 后软件恢复方式 | 总线恢复 GPIO 操作只允许开漏或拉低，不允许主动输出高电平 | 【已决策，需验证】 |

---

# 需求完整性检查表

| 检查项 | 判断 | 说明 | 建议补充内容 |
|---|---|---|---|
| 1. 是否说明了最终目标，而不是只描述了一个模糊愿望？ | 是 | 目标明确：生成 JY61P 与 ATK-MS53L1M/VL53L1X 的 Markdown 代码架构设计文档，用于指导后续 `.c/.h` 补全。 | 无。 |
| 2. 是否提供了当前工程状态、文件路径、代码或日志？ | 部分满足 | 用户已说明工程路径可忽略；未提供现有源码和编译日志。本轮是架构设计，不强依赖。 | 后续真正写代码前，建议提供 `Core/Inc`、`Core/Src`、`.ioc`、已有 `main.c` 和编译日志。 |
| 3. 是否写清了硬件、工具链、库版本和外设连接？ | 是 | 已明确 STM32C8T6、STM32CubeIDE 1.19.0、I2C1 PB6/PB7、JY61P I2C1、VL53L1X 直连、I2C 上拉 5V、UART1 PA9/PA10 电机。 | 无。 |
| 4. 是否说明了本轮允许修改和禁止修改的范围？ | 是 | 本轮只生成 Markdown 架构文档，不生成 `.c/.h` 完整实现代码。 | 无。 |
| 5. 是否定义了可观察、可测试的验收标准？ | 是 | 本文第 14 节定义编译、初始化、IMU、激光测距、I2C 总线、电机接口等验收标准。 | 无。 |
| 6. 是否说明了旧功能中哪些必须回归验证？ | 部分满足 | 已明确电机使用 UART1 PA9/PA10；其他旧功能未说明。本文把最低回归项定义为 UART1 电机通信、主循环实时性、I2C1 双传感器读取。 | 若后续已有树莓派通信、急停、上位机协议等旧功能，需要补充回归项。 |
| 7. 是否要求输出测试步骤和未验证风险？ | 是 | 本文第 15 节为测试步骤，第 16 节为未验证风险。 | 无。 |
| 8. 如果是改进需求，是否同步修改了验收标准？ | 是 | 本文按用户补充条件删除 RTOS/DMA/I2C 初始化细节验收，新增 UART1 电机接口、I2C 总线恢复、车体系映射、JY61P 累计误差抑制等验收项。 | 无。 |

---

# 正式 Markdown 架构文档

## 资料理解与确认结论

### 从项目 Markdown / 任务说明中提取到的需求

| 类别 | 提取到的需求 |
|---|---|
| 项目类型 | 智能物流搬运小车。 |
| 主控 | STM32C8T6，架构按 STM32F103C8T6 类资源设计。 |
| 开发环境 | STM32CubeIDE 1.19.0、STM32 HAL、C 语言。 |
| 负责模块 | JY61P 姿态传感器；ATK-MS53L1M 激光测距模块，实际按 VL53L1X 直连处理。 |
| 当前边界 | 只输出 Markdown 架构设计，不生成 `.c/.h` 完整实现代码。 |
| 传感器总线 | 两个传感器共用 I2C1，SCL = PB6，SDA = PB7。 |
| 电机接口 | UART1，TX = PA9，RX = PA10。 |
| 数据目标 | JY61P 输出姿态、角速度、加速度；VL53L1X 输出车头前方距离。 |
| 控制目标 | 为后续电机控制、避障、姿态修正、路径控制提供实时数据。 |
| 特别要求 | JY61P 必须设计累计误差抑制方案，不能只写读取角度。 |

### 从 JY61P 资料中提取到的关键点

| 类别 | 关键点 | 设计结论 |
|---|---|---|
| 通信方式 | JY61P 支持 I2C/IIC 与 UART | 本项目按 I2C1 设计。 |
| I2C 地址 | 默认 7-bit 地址 `0x50` | HAL 地址为 `0xA0`。 |
| I2C 速率 | JY61P 支持较高 I2C 速率 | 本项目线长远小于 10 cm，但共总线，建议先使用 100 kHz；稳定后可评估 400 kHz。 |
| 数据寄存器 | 加速度、角速度、姿态角、温度寄存器可连续读取 | 推荐读取 `0x34~0x40`。 |
| 字节序 | 16 bit 数据，低字节在前 | 解析时按 little-endian 合成 `int16_t`。 |
| 加速度换算 | `raw / 32768 * 16g` | 输出单位建议保留 g。 |
| 角速度换算 | `raw / 32768 * 2000 °/s` | 输出单位为 deg/s。 |
| 角度换算 | `raw / 32768 * 180°` | 输出单位为 deg。 |
| 温度换算 | `raw / 100 ℃` | 温度保留为诊断字段。 |
| 校准 | 支持内部校准和 offset 寄存器 | 本项目优先做软件零偏，不频繁写传感器内部配置。 |
| 累计误差 | 航向角可能随时间和震动漂移 | 使用软件组合策略抑制。 |

### 从 ATK-MS53L1M / VL53L1X 资料与用户补充中提取到的关键点

| 类别 | 关键点 | 设计结论 |
|---|---|---|
| 模块定位 | ATK-MS53L1M 为激光测距模块 | 本项目用于车头正前方测距。 |
| 实际芯片 | 用户确认使用 VL53L1X 直连 | 直接按 VL53L1X I2C 设备设计。 |
| 通信方式 | I2C1 | SCL = PB6，SDA = PB7。 |
| I2C 地址 | VL53L1X 默认 7-bit `0x29` | HAL 地址为 `0x52`。 |
| 初始化细节 | 用户要求 VL53L1X ID、Long、Timing Budget、Inter-measurement 等参数可忽略 | 架构中只保留默认启动封装接口，不展开底层寄存器。 |
| 距离单位 | mm | 上层统一使用 mm。 |
| 有效范围 | 4 m 级测距模块 | 默认有效范围 40~4000 mm。 |
| 稳定性 | 单个车头激光存在毛刺和视野限制 | 使用中值滤波、滑动平均、异常值剔除、近距离优先策略。 |

### 从原理图 / 补充信息中确认的引脚连接

| 信号 | STM32C8T6 引脚 | 用途 | 状态 |
|---|---|---|---|
| I2C1_SCL | PB6 | JY61P + VL53L1X 共用 SCL | 已确认 |
| I2C1_SDA | PB7 | JY61P + VL53L1X 共用 SDA | 已确认 |
| UART1_TX | PA9 | 电机通信发送 | 已确认 |
| UART1_RX | PA10 | 电机通信接收 | 已确认 |
| I2C 上拉 | 5V | I2C 高电平上拉 | 已确认，但软件需严格保持开漏 |
| JY61P 轴向 | +Y 朝前，+X 朝右 | 车体系映射依据 | 已确认 |

---

## 1. 总体设计目标

JY61P 与 VL53L1X 组成小车底层感知模块，向运动控制层提供实时、稳定、带状态标志的数据。

| 模块 | 作用 | 主要输出 | 上层用途 |
|---|---|---|---|
| JY61P | 姿态与惯性测量 | 车体系 yaw、pitch、roll、角速度、加速度、温度、校准状态 | 直线纠偏、坡度判断、侧倾保护、震动/急停检测、姿态异常检测 |
| ATK-MS53L1M / VL53L1X | 车头前方距离检测 | 原始距离、滤波距离、近距离标志、超时/错误状态 | 避障、减速、停车、安全距离判断 |
| 统一传感器层 | 调度、状态聚合、快照缓存 | `SENSOR_Snapshot_t` | 电机控制、任务控制、调试上报 |

总体目标：

1. 传感器采集不阻塞主循环。
2. 任一 I2C 设备异常时，不永久拖死另一设备。
3. JY61P 累计误差通过代码侧校准与控制策略抑制。
4. VL53L1X 距离输出需要滤波、异常剔除和近距离优先保护。
5. 传感器层不直接控制电机，只向运动控制层提供可信数据和故障标志。

---

## 2. 模块拆分

### 2.1 推荐文件结构

```text
Core/
  Inc/
    jy61p.h
    atk_ms53l1m.h
    sensors.h
    car_pose.h          可选
  Src/
    jy61p.c
    atk_ms53l1m.c
    sensors.c
```

### 2.2 文件职责

| 文件 | 职责 | 必须包含内容 | HAL 关系 | 主循环关系 |
|---|---|---|---|---|
| `jy61p.h` | JY61P 对外接口和类型声明 | 寄存器宏、状态枚举、姿态结构体、校准结构体、API 声明 | 声明需要 `I2C_HandleTypeDef *` | 被 `sensors.h` 或 `main.c` 引用 |
| `jy61p.c` | JY61P I2C 读写、解析、校准、滤波、状态机 | 寄存器读写、连续读取、物理量换算、车体系映射、累计误差抑制 | 使用传入的 `hi2c1` 指针 | 由 `sensor_update()` 周期调用 |
| `atk_ms53l1m.h` | VL53L1X/ATK 测距模块对外接口 | 地址宏、距离结构体、状态枚举、API 声明 | 声明需要 `I2C_HandleTypeDef *` | 被 `sensors.h` 或 `main.c` 引用 |
| `atk_ms53l1m.c` | VL53L1X 默认启动、距离读取、滤波、错误处理 | 默认启动封装、距离读取、滤波、超时处理 | 使用传入的 `hi2c1` 指针 | 由 `sensor_update()` 周期调用 |
| `sensors.h` | 统一传感器管理层接口 | 统一快照结构体、故障位、统一 API | 接收 `&hi2c1` | 供 `main.c` 与电机控制层调用 |
| `sensors.c` | 调度两个传感器、生成快照、总线恢复 | 周期调度、错误隔离、I2C bus recovery、快照缓存 | 可调用 HAL I2C 恢复流程 | 主循环每轮或按周期调用 |
| `car_pose.h` | 可选车体系类型定义 | 车体系姿态、速度、坐标轴说明 | 无 | 供传感器层和控制层共用 |

### 2.3 与 DMA / 中断 / 定时器关系

| 项目 | 设计 |
|---|---|
| RTOS | 不使用。 |
| I2C DMA | 不使用。 |
| I2C 中断 | 不使用。 |
| I2C 读取 | 主循环轮询 + 短超时。 |
| SysTick | 只提供 `HAL_GetTick()` 时间基准，不在中断里读 I2C。 |
| UART1 电机 | 可由电机模块决定轮询或中断；传感器架构只要求不被传感器轮询阻塞。 |

---

## 3. 命名规范

### 3.1 文件命名

| 模块 | 文件名 |
|---|---|
| JY61P | `jy61p.h`、`jy61p.c` |
| ATK-MS53L1M / VL53L1X | `atk_ms53l1m.h`、`atk_ms53l1m.c` |
| 统一传感器层 | `sensors.h`、`sensors.c` |
| 车体姿态类型 | `car_pose.h` |

### 3.2 前缀规范

| 类型 | 前缀 | 示例 |
|---|---|---|
| JY61P 宏 | `JY61P_` | `JY61P_I2C_ADDR_7BIT` |
| JY61P 函数 | `jy61p_` | `jy61p_update()` |
| JY61P 类型 | `JY61P_..._t` | `JY61P_Device_t` |
| ATK/VL53L1X 宏 | `MS53L1M_` | `MS53L1M_I2C_ADDR_7BIT` |
| ATK/VL53L1X 函数 | `ms53l1m_` | `ms53l1m_get_distance()` |
| 统一传感器宏 | `SENSOR_` | `SENSOR_DATA_TIMEOUT_MS` |
| 统一传感器函数 | `sensor_` | `sensor_get_snapshot()` |
| 车体系变量 | `car_` | `car_yaw_est_deg` |

### 3.3 禁止或避免的命名

| 不推荐命名 | 推荐替代 |
|---|---|
| `data` | `jy61p_raw_frame`、`ms53l1m_distance_data` |
| `buf` | `jy61p_rx_buffer`、`ms53l1m_i2c_buffer` |
| `angle` | `jy61p_yaw_deg`、`car_pitch_deg` |
| `distance` | `ms53l1m_filtered_distance_mm` |
| `state` | `jy61p_state`、`sensor_system_state` |

---

## 4. 硬件连接与外设配置

### 4.1 I2C1 硬件连接

| 设备 | 信号 | STM32C8T6 引脚 | 外设 | 地址 |
|---|---|---|---|---|
| JY61P | SCL | PB6 | I2C1 | `0x50` |
| JY61P | SDA | PB7 | I2C1 | `0x50` |
| VL53L1X | SCL | PB6 | I2C1 | `0x29` |
| VL53L1X | SDA | PB7 | I2C1 | `0x29` |

### 4.2 UART1 电机连接

| 设备 | 信号 | STM32C8T6 引脚 | 外设 |
|---|---|---|---|
| 电机控制器 | TX | PA9 | UART1 |
| 电机控制器 | RX | PA10 | UART1 |

### 4.3 I2C 地址分配

| 设备 | 7-bit 地址 | HAL 地址 | 冲突情况 |
|---|---:|---:|---|
| JY61P | `0x50` | `0xA0` | 无冲突 |
| VL53L1X | `0x29` | `0x52` | 无冲突 |

### 4.4 CubeIDE 配置要求

| 项目 | 配置 |
|---|---|
| I2C 初始化 | 由 CubeIDE 生成 `MX_I2C1_Init()`，传感器驱动不负责初始化外设。 |
| I2C 模式 | 7-bit 地址模式。 |
| I2C 速率 | 建议 100 kHz 起步；若稳定，可评估 400 kHz。 |
| PB6/PB7 | I2C 复用开漏。 |
| I2C 上拉 | 已确认上拉到 5V，软件不得主动输出高电平。 |
| DMA | 不启用。 |
| RTOS | 不使用。 |
| HAL 句柄 | `hi2c1`，通过初始化函数传给传感器模块。 |

### 4.5 I2C 5V 上拉注意事项

I2C 上拉到 5V 已由用户确认。软件侧必须遵守：

1. PB6/PB7 必须保持开漏或输入状态，不得配置为推挽输出高电平。
2. 总线恢复时，如果临时切 GPIO 模式，只允许输出低电平或释放总线，不允许主动输出高电平。
3. 传感器读取必须短超时，避免因 SDA 被拉低导致主循环长时间阻塞。
4. I2C 恢复完成后必须恢复 CubeIDE 生成的 I2C1 配置。

---

## 5. JY61P 架构设计

### 5.1 模块目标

JY61P 模块对上层提供车体系姿态与惯性数据：

| 输出 | 单位 | 用途 |
|---|---|---|
| `car_yaw_est_deg` | deg | 直线纠偏、转向判断。 |
| `car_pitch_deg` | deg | 坡度、车头上抬/下压判断。 |
| `car_roll_deg` | deg | 侧倾判断。 |
| `gyro_yaw_dps` | deg/s | 转向角速度辅助。 |
| `acc_forward_g` | g | 启动、急停、碰撞检测。 |
| `acc_right_g` | g | 侧向冲击检测。 |
| `acc_down_g` | g | 震动和重力方向判断。 |
| `temperature_c` | ℃ | 诊断。 |
| `imu_valid` | bool | 是否允许用于控制。 |
| `imu_calibrated` | bool | 是否完成零偏校准。 |

### 5.2 通信方式

| 项目 | 设计 |
|---|---|
| 外设 | I2C1。 |
| 引脚 | PB6/PB7。 |
| 7-bit 地址 | `0x50`。 |
| HAL 地址 | `0xA0`。 |
| 数据访问 | 主机主动读取寄存器。 |
| UART 模式 | 不使用。 |

### 5.3 初始化流程

| 步骤 | 处理 |
|---|---|
| 1 | `jy61p_init()` 接收 `I2C_HandleTypeDef *` 和当前时间戳。 |
| 2 | 保存 `hi2c1` 指针、地址、默认参数。 |
| 3 | 等待或确认模块上电稳定，建议系统上电后 1000 ms 内不强依赖数据。 |
| 4 | 使用短超时检测 `0x50` 是否应答。 |
| 5 | 读取 `0x34~0x40` 一组数据，确认不是全 0 或全 `0xFF`。 |
| 6 | 初始化滤波器、状态机、错误计数、校准缓存。 |
| 7 | 进入 `JY61P_STATE_RUNNING` 或 `JY61P_STATE_CALIBRATING`。 |

### 5.4 寄存器读取规划

推荐一次连续读取 `0x34~0x40` 共 13 个 16-bit 寄存器，即 26 字节。

| 数据 | 寄存器 | 字节数 | 换算 |
|---|---:|---:|---|
| AX | `0x34` | 2 | `raw / 32768 * 16g` |
| AY | `0x35` | 2 | `raw / 32768 * 16g` |
| AZ | `0x36` | 2 | `raw / 32768 * 16g` |
| GX | `0x37` | 2 | `raw / 32768 * 2000 °/s` |
| GY | `0x38` | 2 | `raw / 32768 * 2000 °/s` |
| GZ | `0x39` | 2 | `raw / 32768 * 2000 °/s` |
| Roll | `0x3D` | 2 | `raw / 32768 * 180°` |
| Pitch | `0x3E` | 2 | `raw / 32768 * 180°` |
| Yaw | `0x3F` | 2 | `raw / 32768 * 180°` |
| TEMP | `0x40` | 2 | `raw / 100 ℃` |

### 5.5 数据帧格式理解

| 数据来源 | 本项目是否使用 | 说明 |
|---|---|---|
| I2C 寄存器读取 | 使用 | 每个寄存器为 16 bit，低字节在前。没有 UART 帧头和 SUM 校验。 |
| UART 主动输出帧 | 不使用 | 不解析 `0x55` 帧头格式。 |

I2C 模式下数据有效性依靠：

1. HAL I2C 返回值。
2. 数据范围检查。
3. 连续样本跳变检查。
4. 时间戳超时检查。
5. 静止物理约束检查。

### 5.6 数据接收方式

| 方式 | 是否使用 | 原因 |
|---|---|---|
| I2C 轮询 | 使用 | 裸机主循环、数据量小、实现稳定。 |
| I2C 中断 | 不使用 | 当前需求不需要。 |
| I2C DMA | 不使用 | 用户明确不使用 DMA。 |
| UART 中断/DMA | 不使用 | JY61P 不走 UART。 |

### 5.7 车体系映射

已知安装方向：JY61P +Y 朝车前，+X 朝车右。

| 车体系字段 | 来源 | 标注 |
|---|---|---|
| `acc_forward_g` | JY61P `acc_y_g` | 已确认 |
| `acc_right_g` | JY61P `acc_x_g` | 已确认 |
| `acc_down_g` | 默认 `-acc_z_g` | 【已决策，需验证】 |
| `gyro_pitch_dps` | JY61P `gyro_x_dps` | 【已决策，需验证】 |
| `gyro_roll_dps` | JY61P `gyro_y_dps` | 【已决策，需验证】 |
| `gyro_yaw_dps` | JY61P `gyro_z_dps` | 符号需实测 |
| `car_pitch_deg` | JY61P `roll_deg` 加符号修正 | 【已决策，需验证】 |
| `car_roll_deg` | JY61P `pitch_deg` 加符号修正 | 【已决策，需验证】 |
| `car_yaw_deg` | JY61P `yaw_deg` 加符号修正 | 【已决策，需验证】 |

建议预留符号宏：

| 宏名 | 默认值 | 用途 |
|---|---:|---|
| `JY61P_SIGN_CAR_PITCH` | `+1` | 修正车体 pitch 方向。 |
| `JY61P_SIGN_CAR_ROLL` | `+1` | 修正车体 roll 方向。 |
| `JY61P_SIGN_CAR_YAW` | `+1` | 修正车体 yaw 方向。 |
| `JY61P_SIGN_ACC_DOWN` | `-1` | 修正 down 方向。 |

### 5.8 数据解析流程

| 步骤 | 处理 |
|---|---|
| 1 | 从 `0x34` 连续读取 26 字节。 |
| 2 | 每两个字节按低字节在前合成为 `int16_t`。 |
| 3 | 换算加速度、角速度、姿态角、温度。 |
| 4 | 扣除软件角速度零偏。 |
| 5 | 执行车体系映射和符号修正。 |
| 6 | 执行一阶低通滤波和 yaw wrap。 |
| 7 | 执行静止判据、跳变检查、范围检查。 |
| 8 | 数据有效才更新对外缓存和 `last_valid_ms`。 |
| 9 | 数据无效只更新错误计数，不覆盖最近有效快照。 |

### 5.9 数据有效性判断

| 检查项 | 建议规则 |
|---|---|
| I2C 返回值 | 必须为 `HAL_OK`。 |
| 原始数据 | 不应连续多次全 0 或全 `0xFF`。 |
| 加速度 | 单轴不超过 ±16 g；静止时模长接近 1 g。 |
| 角速度 | 单轴不超过 ±2000 °/s。 |
| 姿态角 | yaw/roll 在 -180~180，pitch 按实际输出范围检查。 |
| 时间戳 | 超过 `JY61P_DATA_TIMEOUT_MS` 未更新则 invalid。 |
| 跳变 | 静止状态下姿态角大跳变标记为可疑。 |

### 5.10 滤波策略

| 数据 | 滤波方式 | 说明 |
|---|---|---|
| Roll/Pitch | 一阶低通 | 抑制震动毛刺。 |
| Yaw | 互补滤波 + wrap | 结合 gyro 积分与 JY61P yaw。 |
| 加速度 | 原始值 + 轻低通双输出 | 原始值用于急停/冲击，滤波值用于趋势判断。 |
| 角速度 | 扣零偏后一阶低通 | 用于 yaw 估计与运动状态判断。 |
| 温度 | 慢速更新 | 仅诊断，不参与闭环。 |

### 5.11 累计误差抑制方案

本项目不使用卡尔曼滤波。JY61P 累计误差通过组合策略抑制。

#### 5.11.1 上电静止零偏校准

| 项目 | 设计 |
|---|---|
| 触发条件 | 系统上电、电机未使能、小车静止。 |
| 采样周期 | 10 ms。 |
| 采样次数 | 200 次，约 2 s。 |
| 采样内容 | 三轴 gyro、三轴 acc、yaw。 |
| 静止判据 | 三轴角速度小于阈值，加速度模长在 0.95~1.05 g，姿态变化小。 |
| 输出 | `gyro_bias_x/y/z_dps`、`yaw_zero_deg`、`imu_calibrated`。 |
| 保存 | 默认 RAM 保存，不频繁写 Flash。 |

#### 5.11.2 运行中静止零速更新

| 条件 | 建议值 |
|---|---:|
| 电机目标速度 | 0 |
| 静止持续时间 | ≥ 800 ms |
| 三轴角速度 | < 1.5 °/s |
| 加速度模长 | 0.95~1.05 g |

零速更新只缓慢修正 gyro 零偏，不频繁改 `yaw_zero_deg`，防止控制中 yaw 突跳。

#### 5.11.3 分段航向归零

| 场景 | 处理 |
|---|---|
| 每段直线开始 | 记录当前 `car_yaw_est_deg` 为 `yaw_target_deg`。 |
| 直线行驶中 | 使用 `wrap(yaw_target_deg - car_yaw_est_deg)` 作为纠偏误差。 |
| 到达目标点并静止 | 允许重置段内 yaw 参考。 |
| 转弯完成后 | 建立下一段直线的 yaw 目标。 |

#### 5.11.4 互补滤波

| 参数 | 建议值 |
|---|---:|
| gyro 积分权重 | 0.95~0.98 |
| JY61P yaw 修正权重 | 0.02~0.05 |
| yaw 控制误差限幅 | ±30° |
| 静止漂移报警 | 5 分钟超过 5°，需实测调整 |

概念流程：

1. 用扣零偏后的 `gyro_yaw_dps` 积分得到短期 yaw。
2. 用 JY61P 原始 yaw 作为低频参考。
3. 每次融合前对角度差做 wrap 到 -180~180。
4. 数据无效时冻结或降低 yaw 控制权重。
5. 数据超时时禁用 yaw 闭环。

### 5.12 与运动控制接口

| 传感器层提供 | 运动控制层使用 |
|---|---|
| `car_yaw_est_deg` | 直线纠偏。 |
| `car_pitch_deg` | 坡度限速。 |
| `car_roll_deg` | 侧倾保护。 |
| `acc_forward_g` | 急停、碰撞、启动检测。 |
| `gyro_yaw_dps` | 转向角速度辅助。 |
| `imu_valid`、`imu_calibrated` | 是否启用姿态闭环。 |

---

## 6. ATK-MS53L1M / VL53L1X 架构设计

### 6.1 模块目标

| 输出 | 单位 | 用途 |
|---|---|---|
| `raw_distance_mm` | mm | 原始测距，调试和滤波输入。 |
| `filtered_distance_mm` | mm | 避障与减速控制。 |
| `is_warning` | bool | 进入预警距离。 |
| `is_too_close` | bool | 进入硬停车距离。 |
| `range_valid` | bool | 距离是否可信。 |
| `last_valid_ms` | ms | 判断数据是否过期。 |
| `state` | enum | 初始化、运行、错误、超时状态。 |

### 6.2 通信与地址

| 项目 | 设计 |
|---|---|
| 实际芯片 | VL53L1X 直连。 |
| 模块命名 | 仍使用 `atk_ms53l1m.*` 和 `ms53l1m_` 前缀，方便对应硬件模块名。 |
| 外设 | I2C1。 |
| 引脚 | PB6/PB7。 |
| 7-bit 地址 | `0x29`。 |
| HAL 地址 | `0x52`。 |

### 6.3 初始化流程

| 步骤 | 处理 |
|---|---|
| 1 | `ms53l1m_init()` 接收 `I2C_HandleTypeDef *` 和当前时间戳。 |
| 2 | 保存地址 `0x29` 和 HAL 地址 `0x52`。 |
| 3 | 使用短超时检测设备 ready。 |
| 4 | 调用 VL53L1X 默认启动封装。 |
| 5 | 清空滤波缓存、错误计数、距离缓存。 |
| 6 | 进入 `MS53L1M_STATE_RUNNING`。 |

> VL53L1X 的 ID、Long 模式、Timing Budget、Inter-measurement 等细节按用户要求忽略，后续实现时由选定的底层 VL53L1X 库或默认启动函数内部处理。

### 6.4 测距模式选择

| 模式 | 是否使用 | 说明 |
|---|---|---|
| 连续测量 | 使用 | 适合小车实时避障。 |
| 单次测量 | 不作为默认 | 可作为调试接口保留。 |
| UART 输出 | 不使用 | 本项目 VL53L1X 直连 I2C。 |

### 6.5 测距周期和有效范围

| 参数 | 默认值 | 说明 |
|---|---:|---|
| 轮询周期 | 20 ms | 主循环查询是否有新距离。 |
| 数据超时 | 300~500 ms | 超过后禁止高速前进。 |
| 最小有效距离 | 40 mm | 小于该值通常不作为普通有效值，但可触发近距离异常。 |
| 最大有效距离 | 4000 mm | 4 m 级测距上限。 |
| 预警距离 | 600 mm | 限速或提醒。 |
| 减速距离 | 300 mm | 明显减速。 |
| 停车距离 | 150 mm | 请求电机立即停车。 |

### 6.6 数据读取流程

| 步骤 | 处理 |
|---|---|
| 1 | 检查状态是否为 `RUNNING`。 |
| 2 | 到达 20 ms 轮询周期后读取距离或查询 ready。 |
| 3 | 如果无新数据，立即返回，不阻塞等待。 |
| 4 | 如果有新数据，读取 raw distance。 |
| 5 | 执行范围检查和状态检查。 |
| 6 | 有效样本进入中值滤波。 |
| 7 | 中值结果进入滑动平均。 |
| 8 | 更新 `filtered_distance_mm`、`last_valid_ms`、标志位。 |
| 9 | 异常样本只更新错误计数，不覆盖稳定距离。 |

### 6.7 滤波与异常剔除

| 层级 | 方法 | 默认值 | 说明 |
|---|---|---:|---|
| 第一层 | 范围检查 | 40~4000 mm | 超出范围不进入普通滤波。 |
| 第二层 | 中值滤波 | 3 点 | 抑制单点毛刺。 |
| 第三层 | 滑动平均 | 5 点 | 平滑稳定距离。 |
| 第四层 | 跳变剔除 | 300 mm | 跳变过大时要求连续确认。 |
| 安全例外 | 近距离优先 | 2 次确认 | 连续两次低于停车阈值则立即置位 `is_too_close`。 |

### 6.8 单车头激光限制

| 限制 | 处理 |
|---|---|
| 只能检测正前方 | 控制层不得把它当成全向避障。 |
| 斜面、黑色、透明目标可能异常 | 用滤波与无效状态处理。 |
| 快速靠近障碍 | 近距离样本优先触发停车，不被平均滤波延迟。 |
| 数据失效 | 限速或停车。 |

---

## 7. 持续测量与实时更新机制

### 7.1 初始化阶段

| 顺序 | 操作 |
|---|---|
| 1 | `HAL_Init()`。 |
| 2 | 系统时钟初始化。 |
| 3 | GPIO、I2C1、UART1 等 CubeIDE 生成初始化。 |
| 4 | 调用 `sensor_init_all(&hi2c1)`。 |
| 5 | JY61P 检测地址 `0x50`，VL53L1X 检测地址 `0x29`。 |
| 6 | 启动 VL53L1X 默认连续测距。 |
| 7 | 启动或执行 JY61P 上电静止校准。 |
| 8 | 初始化统一快照和故障标志。 |

### 7.2 主循环调度

| 周期 | 任务 |
|---|---|
| 每轮循环 | 获取 `HAL_GetTick()`。 |
| 10 ms | `jy61p_update()`。 |
| 20 ms | `ms53l1m_update()`。 |
| 20 ms | `sensor_update_snapshot()`。 |
| 10~20 ms | 电机控制层读取快照，计算 UART1 电机命令。 |
| 500~1000 ms | 输出诊断日志。 |

### 7.3 数据缓存方式

| 缓存 | 说明 |
|---|---|
| JY61P 内部缓存 | 原始数据、滤波数据、校准参数、状态。 |
| VL53L1X 内部缓存 | 原始距离、滤波窗口、稳定距离、状态。 |
| 统一快照 | 将两个模块最近有效数据复制为 `SENSOR_Snapshot_t`。 |
| 旧数据策略 | 旧数据可用于显示和诊断；超时后 `valid=false`，不得用于闭环控制。 |

### 7.4 避免阻塞主循环

1. 不在 update 函数中使用长 `HAL_Delay()`。
2. I2C 读写使用 5~10 ms 短超时。
3. VL53L1X 未 ready 时直接返回。
4. JY61P 校准分步执行，不一次阻塞 2 秒。
5. 总线恢复有限次数执行，不无限重试。

### 7.5 I2C 总线恢复

建议统一传感器层提供：

| 接口 | 作用 |
|---|---|
| `sensor_i2c_check_bus()` | 检查 bus busy、SDA/SCL 状态。 |
| `sensor_i2c_recover_bus()` | 释放 I2C 总线，必要时 SCL 产生有限脉冲。 |
| `sensor_try_recover_device()` | 对单个设备按间隔重新检测。 |
| `sensor_mark_device_fault()` | 标记单设备故障，避免错误扩散。 |

总线恢复注意事项：

1. 因 I2C 上拉为 5V，恢复 GPIO 不能推挽输出高电平。
2. 恢复完成后重新进入 I2C 外设模式。
3. 恢复时不要无限阻塞主循环。
4. 一个设备错误时，先标记单设备 fault，再判断总线是否整体异常。

---

## 8. 与电机控制模块的配合方式

### 8.1 电机接口

| 项目 | 设计 |
|---|---|
| 电机通信外设 | UART1。 |
| TX | PA9。 |
| RX | PA10。 |
| 传感器层是否直接发电机命令 | 否。 |
| 电机协议 | 未提供，本文不定义协议帧。 |

### 8.2 传感器快照给电机控制层的数据

| 字段 | 用途 |
|---|---|
| `car_yaw_est_deg` | 直线纠偏。 |
| `car_yaw_rate_dps` | 转向动态判断。 |
| `car_pitch_deg` | 坡度/地形变化判断。 |
| `car_roll_deg` | 侧倾风险判断。 |
| `acc_forward_g` | 启动、急停、碰撞检测。 |
| `acc_right_g` | 侧向冲击检测。 |
| `laser_filtered_distance_mm` | 正前方避障。 |
| `laser_is_warning` | 限速。 |
| `laser_is_too_close` | 停车。 |
| `sensor_fault_flags` | 降级控制或报警。 |

### 8.3 典型控制策略

| 场景 | 控制层策略 |
|---|---|
| 正常直线行驶 | 使用 yaw 误差做 PID 或 P 修正。 |
| 坡度变大 | 降低最大速度。 |
| Roll 超安全阈值 | 停车或报警。 |
| 距离小于预警阈值 | 限速。 |
| 距离小于减速阈值 | 明显减速。 |
| 距离小于停车阈值 | 通过 UART1 请求电机立即停车。 |
| IMU 无效 | 禁用 yaw 闭环，限制速度。 |
| 激光无效 | 禁止高速前进或停车。 |
| 两传感器都无效 | 停车。 |

---

## 9. 状态机与错误处理

### 9.1 通用状态

| 状态 | 含义 |
|---|---|
| `UNINIT` | 未初始化。 |
| `INITING` | 初始化中。 |
| `RUNNING` | 正常运行。 |
| `CALIBRATING` | 校准中，主要用于 JY61P。 |
| `DATA_TIMEOUT` | 数据超时。 |
| `COMM_ERROR` | I2C 通信错误。 |
| `DATA_INVALID` | 数据不可信。 |
| `NEED_REINIT` | 需要重新初始化。 |
| `DISABLED` | 被上层禁用。 |

### 9.2 JY61P 状态机

| 状态 | 进入条件 | 退出条件 | 上层处理 | 是否允许旧数据 |
|---|---|---|---|---|
| `UNINIT` | 上电默认 | 调用初始化 | 不使用 | 否 |
| `INITING` | 初始化开始 | 成功或失败 | 等待 | 否 |
| `CALIBRATING` | 上电或命令触发校准 | 校准成功/失败 | 禁止高速运动 | 可显示，不建议闭环 |
| `RUNNING` | 初始化成功且数据有效 | 超时/错误/校准 | 正常使用 | 是 |
| `DATA_TIMEOUT` | 超时未更新 | 新有效数据恢复 | 禁用 yaw 闭环 | 只诊断 |
| `COMM_ERROR` | 连续 I2C 失败 | 恢复成功 | 降级或停车 | 只诊断 |
| `DATA_INVALID` | 数据范围或物理约束失败 | 连续有效样本恢复 | 不用于控制 | 否 |
| `NEED_REINIT` | 错误累计超阈值 | 重新初始化成功 | 触发恢复 | 否 |

### 9.3 VL53L1X 状态机

| 状态 | 进入条件 | 退出条件 | 上层处理 | 是否允许旧数据 |
|---|---|---|---|---|
| `UNINIT` | 上电默认 | 调用初始化 | 不使用 | 否 |
| `INITING` | 初始化开始 | 成功或失败 | 等待 | 否 |
| `RUNNING` | 初始化成功且距离有效 | 超时/错误 | 正常避障 | 是 |
| `DATA_TIMEOUT` | 长时间无新距离 | 新有效距离恢复 | 限速或停车 | 只短时显示 |
| `COMM_ERROR` | 连续 I2C 错误 | 恢复成功 | 禁止高速前进 | 否 |
| `DATA_INVALID` | 距离异常 | 连续有效样本恢复 | 不使用该距离 | 否 |
| `NEED_REINIT` | 错误超阈值 | 重新初始化成功 | 触发恢复 | 否 |

### 9.4 错误处理原则

| 错误等级 | 示例 | 处理 |
|---|---|---|
| 轻微 | 单次 I2C 失败、单次距离毛刺 | 错误计数加一，保留旧值。 |
| 中等 | 连续数次失败、短时超时 | 标记 invalid，控制层降级。 |
| 严重 | 总线卡死、长时间无数据 | 停车或禁止自动运行，触发总线恢复。 |
| 恢复 | 连续有效样本达到阈值 | 清除连续错误，恢复 running。 |

---

## 10. 推荐 API 设计

### 10.1 JY61P API

| 函数名 | 功能 | 输入参数 | 输出参数 | 返回值含义 | 调用时机 | 是否阻塞 | HAL 依赖 |
|---|---|---|---|---|---|---|---|
| `jy61p_init` | 初始化设备对象和通信检测 | I2C 句柄、地址、时间戳 | 设备对象状态 | 成功/失败 | 系统初始化 | 短阻塞 | I2C1 |
| `jy61p_update` | 周期读取并更新姿态 | 设备对象、时间戳 | 内部缓存 | 成功/错误/无效 | 10 ms 周期 | 短阻塞 | I2C1 |
| `jy61p_read_raw` | 读取原始寄存器 | 设备对象 | 原始缓存 | 成功/I2C 错误 | update 内部 | 短阻塞 | I2C1 |
| `jy61p_parse_raw` | 原始数据换算物理量 | 原始缓存 | 姿态/惯性数据 | 成功/无效 | update 内部 | 不阻塞 | 无 |
| `jy61p_get_attitude` | 获取最近姿态 | 设备对象 | 姿态副本 | 成功/无效 | 电机控制 | 不阻塞 | 无 |
| `jy61p_start_calibration` | 启动校准 | 设备对象、校准类型 | 状态变化 | 成功/条件不满足 | 上电或命令 | 不阻塞 | 无 |
| `jy61p_calibration_step` | 分步执行校准 | 设备对象、时间戳 | 进度 | 进行中/成功/失败 | 主循环 | 短阻塞 | I2C1 |
| `jy61p_set_yaw_zero` | 设置当前 yaw 为段内零位 | 设备对象 | 校准参数 | 成功/无效 | 直线段开始 | 不阻塞 | 无 |
| `jy61p_recover` | 错误恢复 | 设备对象、时间戳 | 状态变化 | 成功/失败 | 错误状态 | 短阻塞 | I2C1 |
| `jy61p_get_state` | 获取状态和错误 | 设备对象 | 状态副本 | 成功 | 任意时刻 | 不阻塞 | 无 |

### 10.2 ATK-MS53L1M / VL53L1X API

| 函数名 | 功能 | 输入参数 | 输出参数 | 返回值含义 | 调用时机 | 是否阻塞 | HAL 依赖 |
|---|---|---|---|---|---|---|---|
| `ms53l1m_init` | 初始化测距模块 | I2C 句柄、地址、时间戳 | 设备对象 | 成功/失败 | 系统初始化 | 短阻塞 | I2C1 |
| `ms53l1m_start_default` | 启动 VL53L1X 默认测距 | 设备对象 | 状态变化 | 成功/失败 | 初始化内 | 短阻塞 | I2C1 |
| `ms53l1m_update` | 周期读取距离 | 设备对象、时间戳 | 距离缓存 | 成功/未 ready/错误 | 20 ms 周期 | 短阻塞 | I2C1 |
| `ms53l1m_read_distance_raw` | 读取原始距离 | 设备对象 | 原始距离 mm | 成功/错误 | update 内部 | 短阻塞 | I2C1 |
| `ms53l1m_filter_update` | 更新滤波器 | 原始距离 | 稳定距离 | 成功/异常/样本不足 | 读取成功后 | 不阻塞 | 无 |
| `ms53l1m_get_distance` | 获取稳定距离 | 设备对象 | 距离副本 | 成功/无效 | 电机控制 | 不阻塞 | 无 |
| `ms53l1m_recover` | 错误恢复 | 设备对象、时间戳 | 状态变化 | 成功/失败 | 错误状态 | 短阻塞 | I2C1 |
| `ms53l1m_get_state` | 获取状态和错误 | 设备对象 | 状态副本 | 成功 | 任意时刻 | 不阻塞 | 无 |

### 10.3 统一传感器层 API

| 函数名 | 功能 | 输入参数 | 输出参数 | 调用时机 |
|---|---|---|---|---|
| `sensor_init_all` | 初始化 JY61P 和 VL53L1X | `&hi2c1`、时间戳 | 系统状态 | main 初始化 |
| `sensor_update` | 调度所有传感器 | 时间戳 | 更新内部快照 | 主循环 |
| `sensor_get_snapshot` | 获取统一快照 | 无 | `SENSOR_Snapshot_t` 副本 | 电机控制 |
| `sensor_get_fault_flags` | 获取故障位 | 无 | bitmask | 安全状态机 |
| `sensor_start_imu_calibration` | 触发 IMU 校准 | 校准类型 | 校准状态 | 上电或命令 |
| `sensor_i2c_recover_bus` | 恢复 I2C 总线 | 时间戳 | 恢复结果 | 总线异常 |
| `sensor_recover_all` | 尝试恢复所有错误设备 | 时间戳 | 系统状态 | 错误状态 |

---

## 11. 推荐数据结构设计

> 本节只描述结构体字段，不提供完整 C 代码。

### 11.1 `JY61P_RawData_t`

| 字段 | 类型建议 | 单位 | 说明 | 是否 volatile |
|---|---|---|---|---|
| `acc_raw_x/y/z` | `int16_t` | LSB | 原始加速度 | 否 |
| `gyro_raw_x/y/z` | `int16_t` | LSB | 原始角速度 | 否 |
| `roll_raw` | `int16_t` | LSB | 原始 Roll | 否 |
| `pitch_raw` | `int16_t` | LSB | 原始 Pitch | 否 |
| `yaw_raw` | `int16_t` | LSB | 原始 Yaw | 否 |
| `acc_x_g/y_g/z_g` | `float` | g | 换算后加速度 | 否 |
| `gyro_x_dps/y_dps/z_dps` | `float` | deg/s | 换算后角速度 | 否 |
| `temperature_c` | `float` | ℃ | 温度 | 否 |
| `sample_time_ms` | `uint32_t` | ms | 采样时间 | 否 |

### 11.2 `JY61P_Attitude_t`

| 字段 | 类型建议 | 单位 | 说明 | 上层权限 |
|---|---|---|---|---|
| `jy61p_roll_deg` | `float` | deg | 传感器原始 Roll 换算值 | 只读 |
| `jy61p_pitch_deg` | `float` | deg | 传感器原始 Pitch 换算值 | 只读 |
| `jy61p_yaw_deg` | `float` | deg | 传感器原始 Yaw 换算值 | 只读 |
| `car_roll_deg` | `float` | deg | 车体系横滚 | 只读 |
| `car_pitch_deg` | `float` | deg | 车体系俯仰 | 只读 |
| `car_yaw_deg` | `float` | deg | 车体系 yaw | 只读 |
| `car_yaw_est_deg` | `float` | deg | 互补滤波后的 yaw | 只读 |
| `valid` | `uint8_t` | - | 是否有效 | 只读 |
| `calibrated` | `uint8_t` | - | 是否校准 | 只读 |
| `last_valid_ms` | `uint32_t` | ms | 最近有效时间 | 只读 |

### 11.3 `JY61P_CalibParam_t`

| 字段 | 类型建议 | 单位 | 说明 |
|---|---|---|---|
| `gyro_bias_x_dps` | `float` | deg/s | X 轴角速度零偏。 |
| `gyro_bias_y_dps` | `float` | deg/s | Y 轴角速度零偏。 |
| `gyro_bias_z_dps` | `float` | deg/s | Z 轴角速度零偏。 |
| `yaw_zero_deg` | `float` | deg | 当前 yaw 零位。 |
| `calibrated` | `uint8_t` | - | 校准是否有效。 |
| `sample_count` | `uint16_t` | 次 | 校准采样数。 |
| `last_calib_ms` | `uint32_t` | ms | 最近校准时间。 |

### 11.4 `JY61P_Device_t`

| 字段 | 类型建议 | 说明 |
|---|---|---|
| `i2c` | `I2C_HandleTypeDef *` | I2C 句柄。 |
| `addr_7bit` | `uint8_t` | `0x50`。 |
| `addr_hal` | `uint16_t` | `0xA0`。 |
| `state` | `JY61P_State_t` | 当前状态。 |
| `last_error` | `JY61P_Error_t` | 最近错误。 |
| `error_count` | `uint16_t` | 总错误计数。 |
| `consecutive_error_count` | `uint16_t` | 连续错误计数。 |
| `raw` | `JY61P_RawData_t` | 原始数据。 |
| `attitude` | `JY61P_Attitude_t` | 姿态数据。 |
| `calib` | `JY61P_CalibParam_t` | 校准参数。 |
| `last_poll_ms` | `uint32_t` | 最近轮询时间。 |

### 11.5 `MS53L1M_Distance_t`

| 字段 | 类型建议 | 单位 | 说明 |
|---|---|---|---|
| `raw_distance_mm` | `uint16_t` | mm | 最近原始距离。 |
| `filtered_distance_mm` | `uint16_t` | mm | 稳定距离。 |
| `last_valid_distance_mm` | `uint16_t` | mm | 最近有效距离。 |
| `valid` | `uint8_t` | - | 是否有效。 |
| `is_warning` | `uint8_t` | - | 是否进入预警距离。 |
| `is_too_close` | `uint8_t` | - | 是否进入停车距离。 |
| `last_valid_ms` | `uint32_t` | ms | 最近有效时间。 |
| `sample_count` | `uint32_t` | 次 | 有效样本数。 |

### 11.6 `MS53L1M_Filter_t`

| 字段 | 类型建议 | 单位 | 说明 |
|---|---|---|---|
| `median_window` | `uint16_t[]` | mm | 中值滤波窗口。 |
| `avg_window` | `uint16_t[]` | mm | 平均滤波窗口。 |
| `median_count` | `uint8_t` | 次 | 中值样本数。 |
| `avg_count` | `uint8_t` | 次 | 平均样本数。 |
| `last_accepted_mm` | `uint16_t` | mm | 最近接受距离。 |
| `reject_count` | `uint16_t` | 次 | 异常剔除次数。 |

### 11.7 `MS53L1M_Device_t`

| 字段 | 类型建议 | 说明 |
|---|---|---|
| `i2c` | `I2C_HandleTypeDef *` | I2C 句柄。 |
| `addr_7bit` | `uint8_t` | `0x29`。 |
| `addr_hal` | `uint16_t` | `0x52`。 |
| `state` | `MS53L1M_State_t` | 当前状态。 |
| `last_error` | `MS53L1M_Error_t` | 最近错误。 |
| `distance` | `MS53L1M_Distance_t` | 距离数据。 |
| `filter` | `MS53L1M_Filter_t` | 滤波缓存。 |
| `error_count` | `uint16_t` | 总错误计数。 |
| `consecutive_error_count` | `uint16_t` | 连续错误计数。 |
| `last_poll_ms` | `uint32_t` | 最近轮询时间。 |

### 11.8 `SENSOR_Snapshot_t`

| 字段 | 类型建议 | 说明 |
|---|---|---|
| `imu_attitude` | `JY61P_Attitude_t` | 姿态数据副本。 |
| `laser_distance` | `MS53L1M_Distance_t` | 距离数据副本。 |
| `fault_flags` | `uint32_t` | 统一故障位。 |
| `snapshot_time_ms` | `uint32_t` | 快照时间。 |
| `imu_ok` | `uint8_t` | IMU 是否可用。 |
| `laser_ok` | `uint8_t` | 激光是否可用。 |
| `safe_to_move` | `uint8_t` | 是否允许正常移动。 |

---

## 12. 关键参数表

| 推荐宏名 | 默认值 | 单位 | 所属模块 | 是否需实测调整 | 说明 |
|---|---:|---|---|---|---|
| `JY61P_I2C_ADDR_7BIT` | `0x50` | - | JY61P | 否 | JY61P 地址。 |
| `JY61P_I2C_ADDR_HAL` | `0xA0` | - | JY61P | 否 | HAL 地址。 |
| `MS53L1M_I2C_ADDR_7BIT` | `0x29` | - | VL53L1X | 否 | VL53L1X 地址。 |
| `MS53L1M_I2C_ADDR_HAL` | `0x52` | - | VL53L1X | 否 | HAL 地址。 |
| `SENSOR_I2C_TIMEOUT_MS` | 5 | ms | 统一层 | 是 | I2C 短超时。 |
| `JY61P_UPDATE_PERIOD_MS` | 10 | ms | JY61P | 是 | 姿态刷新周期。 |
| `JY61P_DATA_TIMEOUT_MS` | 100 | ms | JY61P | 是 | 姿态数据超时。 |
| `JY61P_CALIB_SAMPLE_COUNT` | 200 | 次 | JY61P | 是 | 校准采样次数。 |
| `JY61P_CALIB_SAMPLE_PERIOD_MS` | 10 | ms | JY61P | 是 | 校准采样周期。 |
| `JY61P_GYRO_STILL_THRESHOLD_DPS` | 1.5 | °/s | JY61P | 是 | 静止角速度阈值。 |
| `JY61P_ACC_NORM_MIN_G` | 0.95 | g | JY61P | 是 | 静止加速度模长下限。 |
| `JY61P_ACC_NORM_MAX_G` | 1.05 | g | JY61P | 是 | 静止加速度模长上限。 |
| `JY61P_FILTER_ALPHA_ATT` | 0.3 | - | JY61P | 是 | 姿态一阶低通系数。 |
| `JY61P_YAW_FILTER_GYRO_WEIGHT` | 0.98 | - | JY61P | 是 | yaw 互补滤波 gyro 权重。 |
| `JY61P_YAW_FILTER_ANGLE_WEIGHT` | 0.02 | - | JY61P | 是 | yaw 互补滤波角度权重。 |
| `JY61P_YAW_CONTROL_LIMIT_DEG` | 30 | deg | 控制接口 | 是 | yaw 纠偏限幅。 |
| `MS53L1M_UPDATE_PERIOD_MS` | 20 | ms | VL53L1X | 是 | 测距轮询周期。 |
| `MS53L1M_DATA_TIMEOUT_MS` | 500 | ms | VL53L1X | 是 | 测距数据超时。 |
| `MS53L1M_MIN_VALID_MM` | 40 | mm | VL53L1X | 是 | 最小有效距离。 |
| `MS53L1M_MAX_VALID_MM` | 4000 | mm | VL53L1X | 是 | 最大有效距离。 |
| `MS53L1M_WARN_DISTANCE_MM` | 600 | mm | VL53L1X | 是 | 预警距离。 |
| `MS53L1M_SLOW_DISTANCE_MM` | 300 | mm | VL53L1X | 是 | 减速距离。 |
| `MS53L1M_STOP_DISTANCE_MM` | 150 | mm | VL53L1X | 是 | 停车距离。 |
| `MS53L1M_MEDIAN_WINDOW` | 3 | 次 | VL53L1X | 是 | 中值滤波窗口。 |
| `MS53L1M_AVG_WINDOW` | 5 | 次 | VL53L1X | 是 | 滑动平均窗口。 |
| `MS53L1M_JUMP_REJECT_MM` | 300 | mm | VL53L1X | 是 | 跳变剔除阈值。 |
| `SENSOR_I2C_RECOVER_PULSE_COUNT` | 9 | 次 | 统一层 | 是 | I2C 总线恢复 SCL 脉冲数。 |
| `SENSOR_FAULT_RECOVER_PERIOD_MS` | 1000 | ms | 统一层 | 是 | 故障恢复尝试间隔。 |

---

## 13. 文件组织建议

### 13.1 工程目录

```text
Core/
  Inc/
    jy61p.h
    atk_ms53l1m.h
    sensors.h
    car_pose.h
  Src/
    jy61p.c
    atk_ms53l1m.c
    sensors.c
    main.c
```

### 13.2 CubeIDE 生成代码注意事项

| 文件 | 处理方式 |
|---|---|
| `main.c` | 只能在 `USER CODE BEGIN` / `USER CODE END` 区域调用传感器初始化和周期更新。 |
| `i2c.c` / `i2c.h` | 由 CubeIDE 生成，不在传感器驱动中修改 I2C 初始化细节。 |
| `usart.c` / `usart.h` | UART1 电机配置由 CubeIDE 或电机模块处理。 |
| `jy61p.c/h` | 用户自建文件，不被 CubeMX 覆盖。 |
| `atk_ms53l1m.c/h` | 用户自建文件，不被 CubeMX 覆盖。 |
| `sensors.c/h` | 用户自建文件，不被 CubeMX 覆盖。 |

### 13.3 `main.c` 调用关系

初始化阶段：

1. HAL 初始化。
2. 系统时钟初始化。
3. GPIO 初始化。
4. I2C1 初始化。
5. UART1 初始化。
6. 调用 `sensor_init_all(&hi2c1)`。
7. 进入主循环。

主循环阶段：

1. 获取 `now_ms = HAL_GetTick()`。
2. 调用 `sensor_update(now_ms)`。
3. 电机控制层调用 `sensor_get_snapshot()`。
4. 电机控制层通过 UART1 输出控制命令。
5. 定期输出诊断日志。

---

## 14. 验收标准

### 14.1 编译层面

| 编号 | 验收标准 |
|---|---|
| C-01 | 工程在 STM32CubeIDE 1.19.0 中可编译通过。 |
| C-02 | 新增文件均加入工程编译路径。 |
| C-03 | 不出现 `jy61p_*`、`ms53l1m_*`、`sensor_*` 未定义引用。 |
| C-04 | 不与 CubeIDE 生成的 `hi2c1`、`MX_I2C1_Init()`、UART1 符号冲突。 |
| C-05 | 不启用 RTOS，不依赖 DMA。 |

### 14.2 初始化层面

| 编号 | 验收标准 |
|---|---|
| I-01 | I2C1 使用 PB6/PB7。 |
| I-02 | I2C 扫描或 ready 检测能发现 JY61P `0x50`。 |
| I-03 | I2C 扫描或 ready 检测能发现 VL53L1X `0x29`。 |
| I-04 | 初始化失败时系统不死循环，能进入错误状态。 |
| I-05 | PB6/PB7 不被配置为推挽高电平输出。 |

### 14.3 JY61P 数据读取层面

| 编号 | 验收标准 |
|---|---|
| J-01 | 静止水平放置时，姿态角输出稳定。 |
| J-02 | 手动旋转车体时 `car_yaw_est_deg` 连续变化。 |
| J-03 | 抬高车头时 `car_pitch_deg` 方向正确；若相反，通过符号宏修正。 |
| J-04 | 车体侧倾时 `car_roll_deg` 方向正确；若相反，通过符号宏修正。 |
| J-05 | 静止时扣零偏后的角速度接近 0。 |
| J-06 | 超过数据超时阈值未更新时，`imu_valid=false`。 |
| J-07 | I2C 读取失败不覆盖最近有效姿态数据。 |

### 14.4 JY61P 校准与误差抑制层面

| 编号 | 验收标准 |
|---|---|
| JC-01 | 上电静止约 2 s 后生成 gyro 零偏。 |
| JC-02 | 校准完成后 `imu_calibrated=true`。 |
| JC-03 | 运动中触发校准应被拒绝或延迟。 |
| JC-04 | 静止运行 5 min，yaw 漂移被记录，零速更新能降低后续漂移趋势。 |
| JC-05 | 每段直线开始能建立新的 `yaw_target_deg`。 |
| JC-06 | IMU 超时后电机控制层禁用 yaw 闭环。 |

### 14.5 VL53L1X 测距层面

| 编号 | 验收标准 |
|---|---|
| L-01 | VL53L1X 地址固定使用 `0x29`。 |
| L-02 | 距离单位统一为 mm。 |
| L-03 | 40~4000 mm 范围内距离变化能被读取。 |
| L-04 | 单次毛刺不会污染 `filtered_distance_mm`。 |
| L-05 | 距离低于 600 mm 时 `is_warning=true`。 |
| L-06 | 距离低于 150 mm 且连续确认时 `is_too_close=true`。 |
| L-07 | 距离数据超时后 `laser_ok=false`。 |

### 14.6 I2C 总线与连续运行

| 编号 | 验收标准 |
|---|---|
| B-01 | JY61P 与 VL53L1X 同时运行 30 min 不死机。 |
| B-02 | 任一设备断开后，系统能标记对应设备错误。 |
| B-03 | 任一设备异常后，另一个设备不应被永久拖死。 |
| B-04 | 总线异常后，统一传感器层可尝试 bus recovery。 |
| B-05 | 主循环无明显卡顿，UART1 电机控制仍能按周期运行。 |

### 14.7 与电机控制接口层面

| 编号 | 验收标准 |
|---|---|
| M-01 | 电机控制层能读取 `SENSOR_Snapshot_t`。 |
| M-02 | 激光 `is_too_close=true` 时，电机控制层可通过 UART1 请求停车。 |
| M-03 | JY61P 无效时，电机控制层禁用航向闭环。 |
| M-04 | VL53L1X 无效时，电机控制层禁止高速前进。 |
| M-05 | 传感器层不直接发送电机命令。 |

---

## 15. 测试步骤

### 15.1 单独测试 JY61P

| 项目 | 内容 |
|---|---|
| 测试目的 | 确认地址、寄存器读取、姿态换算、车体系映射。 |
| 操作方法 | 只连接 JY61P，周期打印 raw、gyro、acc、car_yaw、car_pitch、car_roll。 |
| 预期现象 | I2C 地址 `0x50` 应答；姿态随转动变化；静止角速度接近 0。 |
| 失败检查 | PB6/PB7 接反、上拉、电源、GND、HAL 地址是否左移、I2C 速率。 |

### 15.2 单独测试 VL53L1X

| 项目 | 内容 |
|---|---|
| 测试目的 | 确认地址、默认启动、距离读取和滤波。 |
| 操作方法 | 只连接 VL53L1X，检测 `0x29`，打印 raw 和 filtered 距离。 |
| 预期现象 | 障碍物移动时距离同步变化。 |
| 失败检查 | 地址、供电、上拉、VL53L1X 底层库绑定、SCL/SDA 接线。 |

### 15.3 两个传感器同时运行测试

| 项目 | 内容 |
|---|---|
| 测试目的 | 验证共用 I2C1 无冲突。 |
| 操作方法 | 同时连接两个传感器，运行 `sensor_update()`，打印状态和更新时间戳。 |
| 预期现象 | `0x50` 与 `0x29` 均能更新，错误计数不持续增加。 |
| 失败检查 | 总线被拉低、地址冲突、线束、上拉、电机噪声。 |

### 15.4 静止状态测试

| 项目 | 内容 |
|---|---|
| 测试目的 | 验证 IMU 零偏、yaw 漂移、激光固定距离稳定性。 |
| 操作方法 | 小车静止 5~10 min，记录 yaw、gyro、acc、固定障碍物距离。 |
| 预期现象 | gyro 零偏稳定；yaw 漂移可记录且受抑制；距离抖动在可接受范围。 |
| 失败检查 | 机械震动、IMU 固定、滤波参数、电源噪声、激光目标材质。 |

### 15.5 小车移动状态测试

| 项目 | 内容 |
|---|---|
| 测试目的 | 验证电机噪声下传感器仍稳定。 |
| 操作方法 | 低速直线运行，记录 yaw error、gyro、acc、laser 状态。 |
| 预期现象 | yaw 连续合理，I2C 错误不明显增加。 |
| 失败检查 | 电机电源噪声、地线回流、I2C 线束靠近电机线。 |

### 15.6 前方障碍物距离变化测试

| 项目 | 内容 |
|---|---|
| 测试目的 | 验证避障阈值和滤波。 |
| 操作方法 | 障碍物从 1000 mm 移动到 100 mm，观察 raw、filtered、warning、too_close。 |
| 预期现象 | 距离连续减小；600 mm 预警；300 mm 减速；150 mm 停车。 |
| 失败检查 | 目标材质、安装角度、滤波窗口过大、阈值设置。 |

### 15.7 姿态变化测试

| 项目 | 内容 |
|---|---|
| 测试目的 | 确认车体系映射和符号。 |
| 操作方法 | 抬高车头、压低车头、右倾、左倾、水平旋转。 |
| 预期现象 | `car_pitch_deg`、`car_roll_deg`、`car_yaw_est_deg` 方向符合控制层定义。 |
| 失败检查 | 修改 `JY61P_SIGN_*` 宏，不改底层寄存器解析。 |

### 15.8 通信异常测试

| 项目 | 内容 |
|---|---|
| 测试目的 | 验证短超时、错误隔离、总线恢复。 |
| 操作方法 | 运行中断开某个设备 SDA/SCL 或电源，再恢复。 |
| 预期现象 | 对应设备进入错误状态；系统不死机；恢复后可重新运行。 |
| 失败检查 | I2C 超时过长、恢复无限重试、GPIO 恢复方式错误。 |

### 15.9 长时间运行测试

| 项目 | 内容 |
|---|---|
| 测试目的 | 验证稳定性和漂移。 |
| 操作方法 | 静止和低速运动分别运行 30~60 min，记录日志。 |
| 预期现象 | 无死机；错误计数可控；距离持续刷新；yaw 漂移在可管理范围。 |
| 失败检查 | 供电、I2C 波形、电机噪声、滤波参数、校准策略。 |

---

## 16. 未验证风险

| 风险项 | 当前状态 | 影响 | 建议处理 |
|---|---|---|---|
| STM32C8T6 具体完整型号 | 用户给出 STM32C8T6，本文按 STM32F103C8T6 类资源处理 | 若具体芯片资源差异较大，外设或 Flash/RAM 可能不同 | 【已决策，需验证】实物丝印和 `.ioc` 最终确认。 |
| JY61P Z 轴方向 | 用户明确 X 朝右、Y 朝前；Z 未明确 | 可能导致 down、yaw、roll/pitch 符号不一致 | 【已决策，需验证】默认板面朝上，保留符号宏，实测后修正。 |
| JY61P 姿态角映射 | 安装方向导致 JY61P 原始 Roll/Pitch 与车体系不完全同名 | 上层若直接使用原始角度可能控制反向 | 【已决策，需验证】统一输出 `car_*` 字段，禁止上层直接使用原始角。 |
| JY61P yaw 累计误差 | 纯 IMU 航向无法完全消除漂移 | 长时间直线控制可能偏航 | 使用上电校准、零速更新、分段归零、互补滤波、误差限幅。 |
| 实车震动 | 未完成实车验证 | 姿态和角速度抖动 | 实测调整滤波系数、静止阈值、yaw 限幅。 |
| I2C 上拉 5V | 已确认 | GPIO 恢复若主动输出高电平可能有硬件风险 | 保持开漏；恢复过程只拉低或释放总线。 |
| I2C 共总线异常 | 两传感器共用 PB6/PB7 | 一个设备异常可能影响另一个设备 | 短超时、错误隔离、bus recovery、断开单设备验收测试。 |
| VL53L1X 默认启动封装 | 用户要求忽略底层细节，但后续仍需具体库实现 | 后续写代码时需要绑定 ST API、ATK 示例库或自写底层读写 | 【已决策，需验证】架构只暴露 `ms53l1m_start_default()`，实现阶段绑定具体库。 |
| VL53L1X 有效距离表现 | 按 40~4000 mm 设计 | 黑色、透明、斜面、强光可能异常 | 实测 100/150/300/600/1000/2000/4000 mm，调整阈值。 |
| 单个车头激光视野有限 | 已知限制 | 无法判断左右侧障碍 | 控制层仅作为正前方避障；后续需要侧向避障时增加传感器。 |
| UART1 电机协议 | 仅确认 PA9/PA10，未提供波特率和协议帧 | 传感器层能提供数据，但不能直接定义电机命令格式 | 【已决策，需验证】传感器层只输出快照，电机协议另行设计。 |
| 旧功能回归范围 | 其他旧功能未说明 | 集成传感器后可能影响已有功能 | 最低回归：UART1 电机收发、I2C1 双传感器、主循环不卡顿、距离触发停车、IMU 姿态保护。 |

---

## 附录：后续低成本模型补代码时的执行顺序建议

1. 先建立 `jy61p.h/c`、`atk_ms53l1m.h/c`、`sensors.h/c` 文件骨架。
2. 先实现 I2C ready 检测和状态机，不急于实现所有滤波。
3. 实现 JY61P 连续读取 `0x34~0x40` 与物理量换算。
4. 实现 JY61P 车体系映射和符号宏。
5. 实现 JY61P 上电静止零偏校准。
6. 实现 VL53L1X 默认启动封装和距离读取。
7. 实现 VL53L1X 中值滤波、滑动平均、近距离优先。
8. 实现 `SENSOR_Snapshot_t` 快照接口。
9. 实现 I2C 短超时、错误计数、错误状态机。
10. 最后实现 I2C bus recovery 和长时间运行日志。
