Chemcrin/IntelligentTransformCart/代码/VibeCoding/姿态模块资料包/传感器代码架构设计_精简版.md

# JY61P 与 ATK-MS53L1M / VL53L1X 传感器模块代码架构设计文档（精简版）

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

---

# 正式 Markdown 架构文档

## 资料理解与确认结论

### 从项目 Markdown / 任务说明中提取到的需求

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

### 从 JY61P 资料中提取到的关键点

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

### 从 ATK-MS53L1M / VL53L1X 资料与用户补充中提取到的关键点

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

### 从原理图 / 补充信息中确认的引脚连接

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

---

## 1. 总体设计目标

JY61P 与 VL53L1X 组成小车底层感知模块，向运动控制层提供实时、稳定、带状态标志的数据。

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

总体目标：

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

---

## 2. 模块拆分

### 2.1 推荐文件结构

```text
Core/
  Inc/
    jy61p.h
    atk_ms53l1m.h
    board_app.h 
    imu_app.h 
    laser_app.h 
  Src/
    jy61p.c
    atk_ms53l1m.c
    board_app.c 
    imu_app.c 
    laser_app.c 
```

### 2.2 文件职责

| 文件 | 职责 | 必须包含内容 | HAL 关系 | 主循环关系 |
| --- | --- | --- | --- | --- |
| `jy61p.h` | JY61P 对外接口和类型声明 | 寄存器宏、状态枚举、姿态结构体、校准结构体、API 声明  | 声明需要 `I2C_HandleTypeDef *` | 被 `sensors.h` 或 `main.c` 引用 |
| `jy61p.c` | JY61P I2C 读写、解析、校准、滤波、状态机 | 寄存器读写、连续读取、物理量换算、车体系映射、累计误差抑制 | 使用传入的 `hi2c1` 指针 | 由 `sensor_update()` 周期调用 |
| `atk_ms53l1m.h` | VL53L1X/ATK 测距模块对外接口 | 地址宏、距离结构体、状态枚举、API 声明 | 声明需要 `I2C_HandleTypeDef *` | 被 `sensors.h` 或 `main.c` 引用 |
| `atk_ms53l1m.c` | VL53L1X 默认启动、距离读取、滤波、错误处理 | 默认启动封装、距离读取、滤波、超时处理 | 使用传入的 `hi2c1` 指针 | 由 `sensor_update()` 周期调用 |
| **atk_ms53l1m.h/c** | **激光测距底层驱动**。，返回 | | 用VL53L1X API走I2C读取距离 | `g_laser_distance_mm` 等 |
| **laser_app.h/c** | **激光应用层** | | 封装底层驱动 | 提供 `Laser_App_Init()`、`Laser_App_Loop()`，对外暴露 `g_laser_*` 全局变量 |
| **jy61p.h/c** | **JY61P底层驱动** | | 通过USART3接收陀螺仪数据帧，解析加速度/角速度/角度 | |
| **imu_app.h/c** | **IMU应用层** | | 封装底层驱动 | 提供`IMU_App_Init()`、`IMU_App_Loop()`，对外暴露 `g_imu_*` 全局变量 |
| **board_app.h/c** | **板级统一入口** | | | 提供 `Board_App_Init()`、`Board_App_Loop()`、`Board_App_UartRxCpltCallback()`，main.c只需调这三个函数就能驱动所有传感器 |

**调用关系：**
```
main.c
  → Board_App_Init()     ← 统一初始化
  → Board_App_Loop()     ← 主循环调用
       → IMU_App_Loop()      ← 更新 g_imu_* 变量
       → Laser_App_Loop()    ← 更新 g_laser_* 变量
```

### 2.3 与 DMA / 中断 / 定时器关系

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

---

## 3. 命名规范

### 3.1 文件命名

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

### 3.2 前缀规范

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

### 3.3 禁止或避免的命名

| 不推荐命名 | 推荐替代 |
|---|---|
| `data` | `jy61p_raw_frame`、`ms53l1m_distance_data` |
| `buf` | `jy61p_rx_buffer`、`ms53l1m_i2c_buffer` |
| `angle` | `jy61p_yaw_deg`、`car_pitch_deg` |
| `distance` | `ms53l1m_filtered_distance_mm` |
| `state` | `jy61p_state`、`sensor_system_state` |

---

## 4. 硬件连接与外设配置

### 4.1 I2C1 硬件连接

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

### 4.2 UART1 电机连接

| 设备 | 信号 | STM32C8T6 引脚 | 外设 |
|---|---|---|---|
| 电机控制器 | TX | PA9 | UART1 |
| 电机控制器 | RX | PA10 | UART1 |

### 4.3 I2C 地址分配

| 设备 | 7-bit 地址 | HAL 地址 | 冲突情况 |
|---|---:|---:|---|
| JY61P | `0x50` | `0xA0` | 无冲突 |
| VL53L1X | `0x29` | `0x52` | 无冲突 |

### 4.4 CubeIDE 配置要求

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

### 4.5 I2C 5V 上拉注意事项

I2C 上拉到 5V 已由用户确认。软件侧必须遵守：

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

---

## 5. JY61P 架构设计

### 5.1 模块目标

JY61P 模块对上层提供车体系姿态与惯性数据：

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

### 5.2 通信方式

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

### 5.3 初始化流程

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

### 5.4 寄存器读取规划

推荐一次连续读取 `0x34~0x40` 共 13 个 16-bit 寄存器，即 26 字节。

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

### 5.5 数据帧格式理解

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

I2C 模式下数据有效性依靠：

1. HAL I2C 返回值。
2. 数据范围检查。
3. 连续样本跳变检查。
4. 时间戳超时检查。
5. 静止物理约束检查。

### 5.6 数据接收方式

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

### 5.7 车体系映射

已知安装方向：JY61P +Y 朝车前，+X 朝车右。

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

建议预留符号宏：

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

### 5.8 数据解析流程

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

### 5.9 数据有效性判断

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

### 5.10 滤波策略

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

### 5.11 累计误差抑制方案

本项目不使用卡尔曼滤波。JY61P 累计误差通过组合策略抑制。

#### 5.11.1 上电静止零偏校准

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

#### 5.11.2 运行中静止零速更新

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

零速更新只缓慢修正 gyro 零偏，不频繁改 `yaw_zero_deg`，防止控制中 yaw 突跳。

#### 5.11.3 分段航向归零

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

#### 5.11.4 互补滤波

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

概念流程：

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

### 5.12 与运动控制接口

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

---

## 6. ATK-MS53L1M / VL53L1X 架构设计

### 6.1 模块目标

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

### 6.2 通信与地址

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

### 6.3 初始化流程

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

> VL53L1X 的 ID、Long 模式、Timing Budget、Inter-measurement 等细节按用户要求忽略，后续实现时由选定的底层 VL53L1X 库或默认启动函数内部处理。

### 6.4 测距模式选择

| 模式 | 是否使用 | 说明 |
|---|---|---|
| 连续测量 | 使用 | 适合小车实时避障。 |
| 单次测量 | 不作为默认 | 可作为调试接口保留。 |
| UART 输出 | 不使用 | 本项目 VL53L1X 直连 I2C。 |

### 6.5 测距周期和有效范围

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

### 6.6 数据读取流程

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

### 6.7 滤波与异常剔除

| 层级 | 方法 | 默认值 | 说明 |
|---|---|---:|---|
| 第一层 | 中值滤波 | 3 点 | 抑制单点毛刺。 |
| 第二层 | 跳变剔除 | 300 mm | 突变过大时保留旧值，连续确认后更新。 |
| 安全例外 | 近距离优先 | 2 次确认 | 连续两次低于停车阈值则立即置位 `is_too_close`。 |

### 6.8 单车头激光限制

| 限制 | 处理 |
|---|---|
| 只能检测正前方 | 控制层不得把它当成全向避障。 |
| 斜面、黑色、透明目标可能异常 | 用滤波与无效状态处理。 |
| 快速靠近障碍 | 近距离样本优先触发停车，不被平均滤波延迟。 |
| 数据失效 | 限速或停车。 |

---

## 7. 持续测量与实时更新机制

### 7.1 初始化阶段

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

### 7.2 主循环调度

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

### 7.3 数据缓存方式

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

### 7.4 避免阻塞主循环

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

### 7.5 I2C 总线恢复

建议统一传感器层提供：

| 接口 | 作用 |
|---|---|

一个设备错误时先标记单设备 fault，不影响另一个设备读取。

---

## 8. 与电机控制模块的配合方式

### 8.1 电机接口

| 项目 | 设计 |
|---|---|
| 电机通信外设 | UART1。 |
| TX | PA9。 |
| RX | PA10。 |
| 传感器层是否直接发电机命令 | 否。 |
| 电机协议 | 未提供，本文不定义协议帧。 |

### 8.2 传感器快照给电机控制层的数据

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

### 8.3 典型控制策略

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

---

## 9. 状态机与错误处理

### 9.1 通用状态

| 状态 | 含义 |
|---|---|
| `RUNNING` | 正常运行。 |
| `CALIBRATING` | 校准中（仅 JY61P）。 |
| `ERROR` | 通信失败/数据异常。 |

### 9.2 JY61P 状态机

| 状态 | 进入条件 | 退出条件 | 上层处理 | 是否允许旧数据 |
|---|---|---|---|---|
| `RUNNING` | 数据有效，正常使用 | I2C失败/校准/超时 | 正常控制 | 是 |
| `CALIBRATING` | 上电或命令触发校准 | 校准完成 | 禁止高速运动 | 否 |
| `ERROR` | I2C失败/超时/数据异常 | 新有效数据恢复 | 降级或停车 | 只显示 |

### 9.3 VL53L1X 状态机

| 状态 | 进入条件 | 退出条件 | 上层处理 | 是否允许旧数据 |
|---|---|---|---|---|
| `RUNNING` | 正常读取中 | I2C失败/超时 | 正常避障 | 是 |
| `ERROR` | I2C失败/超时/距离异常 | 新有效距离恢复 | 限速或停车 | 否 |

### 9.4 错误处理原则

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

---

## 10. 推荐 API 设计

### 10.1 JY61P API

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

### 10.2 ATK-MS53L1M / VL53L1X API

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

### 10.3 统一传感器层 API

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

---

## 11. 推荐数据结构设计

> 本节只描述结构体字段，不提供完整 C 代码。

### 11.1 `JY61P_RawData_t`

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

### 11.2 `JY61P_Attitude_t`

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

### 11.3 `JY61P_CalibParam_t`

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

### 11.4 `JY61P_Device_t`

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

### 11.5 `MS53L1M_Distance_t`

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

### 11.6 `MS53L1M_Filter_t`

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

### 11.7 `MS53L1M_Device_t`

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

---

## 12. 关键参数表

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

---

## 13. 文件组织建议

### 13.1 工程目录

```text
Core/
  Inc/
    jy61p.h
    atk_ms53l1m.h
    sensors.h
    car_pose.h
  Src/
    jy61p.c
    atk_ms53l1m.c
    sensors.c
    main.c
```

### 13.2 CubeIDE 生成代码注意事项

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

### 13.3 `main.c` 调用关系

初始化阶段：

1. HAL 初始化。
2. 系统时钟初始化。
3. GPIO 初始化。
4. I2C1 初始化。
5. UART1 初始化。
6. 调用 `jy61p_init(&hi2c1)` 和 `ms53l1m_init(&hi2c1)`。
7. 进入主循环。

主循环阶段：

1. 获取 `now_ms = HAL_GetTick()`。
2. 调用 `jy61p_update(now_ms)` 和 `ms53l1m_update(now_ms)`。
3. 读取 `g_imu_*` 和 `g_laser_*` 公开变量。
4. 电机控制层通过 UART1 输出控制命令。
5. 定期输出诊断日志。

---

## 14. 验收标准

### 14.1 编译层面

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

### 14.2 初始化层面

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

### 14.3 JY61P 数据读取层面

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

### 14.4 JY61P 校准与误差抑制层面

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

### 14.5 VL53L1X 测距层面

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

### 14.6 I2C 总线与连续运行

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

| B-05 | 主循环无明显卡顿，UART1 电机控制仍能按周期运行。 |

### 14.7 与电机控制接口层面

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

---

## 15. 测试步骤

### 15.1 单独测试 JY61P

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

### 15.2 单独测试 VL53L1X

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

### 15.3 两个传感器同时运行测试

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

### 15.4 静止状态测试

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

### 15.5 小车移动状态测试

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

### 15.6 前方障碍物距离变化测试

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

### 15.7 姿态变化测试

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

### 15.8 通信异常测试

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

### 15.9 长时间运行测试

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

---

## 16. 未验证风险

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

---

## 附录：后续低成本模型补代码时的执行顺序建议

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
