Chemcrin/IntelligentTransformCart/代码/VibeCoding/姿态模块资料包/传感器代码架构设计_精简版V2.md

# JY61P 与 ATK-MS53L1M / VL53L1X 传感器模块代码架构设计文档（精简版）

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

---

# 正式 Markdown 架构文档

## 资料理解与确认结论

### 从项目 Markdown / 任务说明中提取到的需求

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

### 从 JY61P 资料中提取到的关键点

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

### 从 ATK-MS53L1M / VL53L1X 资料与用户补充中提取到的关键点

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

### 从原理图 / 补充信息中确认的引脚连接

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

---

## 1. 总体设计目标

JY61P 与 VL53L1X 组成小车底层感知模块，向运动控制层提供实时、稳定、带状态标志的数据。

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

总体目标：

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

---

## 2. 模块拆分

### 2.1 推荐文件结构

```text
Core/
  Inc/
    jy61p.h
    atk_ms53l1m.h
    board_app.h 
    imu_app.h 
    laser_app.h 
  Src/
    jy61p.c
    atk_ms53l1m.c
    board_app.c 
    imu_app.c 
    laser_app.c 
```

### 2.2 文件职责

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

**调用关系：**
```
main.c
  → Board_App_Init()     ← 统一初始化
  → Board_App_Loop()     ← 主循环调用
       → IMU_App_Loop()      ← 更新 g_imu_* 变量
       → Laser_App_Loop()    ← 更新 g_laser_* 变量
```

### 2.3 与 DMA / 中断 / 定时器关系

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

---

## 3. 命名规范

### 3.1 文件命名

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

### 3.2 前缀规范

| 类型 | 前缀 | 示例 |
|---|---|---|
| JY61P 宏 | `JY61P_` | `JY61P_I2C_ADDR_7BIT` |
| JY61P 函数 | `JY61P_` | `JY61P_ReadAll()` |
| JY61P 类型 | `JY61P_..._t` | `JY61P_Device_t` |
| ATK/VL53L1X 宏 | `ATK_MS53L1M_` | `ATK_MS53L1M_I2C_ADDR_8BIT` |
| ATK/VL53L1X 函数 | `ATK_MS53L1M_` | `ATK_MS53L1M_ReadDistance()` |
| 统一传感器宏 | `SENSOR_` | `SENSOR_DATA_TIMEOUT_MS` |
| 统一传感器函数 | `sensor_` | `sensor_get_snapshot()` |
| 车体系变量 | `car_` | `car_yaw_est_deg` |

### 3.3 禁止或避免的命名

| 不推荐命名 | 推荐替代 |
|---|---|
| `data` | `JY61P_RawFrame_t`、`ATK_MS53L1M_DistanceData_t` |
| `buf` | `jy61p_rx_buffer`、`ms53l1m_i2c_buffer` |
| `angle` | `JY61P_YawDeg`、`CarPitchDeg` |
| `distance` | `ATK_MS53L1M_FilteredDistanceMm` |
| `state` | `JY61P_State`、`SensorSystemState` |

---

## 4. 硬件连接与外设配置

### 4.1 I2C1 硬件连接

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

### 4.2 UART1 电机连接

| 设备 | 信号 | STM32C8T6 引脚 | 外设 |
|---|---|---|---|
| 电机控制器 | TX | PA9 | UART1 |
| 电机控制器 | RX | PA10 | UART1 |

### 4.3 I2C 地址分配

| 设备 | 7-bit 地址 | HAL 地址 | 冲突情况 |
|---|---:|---:|---|
| JY61P | `0x50` | `0xA0` | 无冲突 |
| VL53L1X | `0x29` | `0x52` | 无冲突 |

### 4.4 CubeIDE 配置要求

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

### 4.5 I2C 5V 上拉注意事项

I2C 上拉到 5V 已由用户确认。软件侧必须遵守：

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

---

## 5. JY61P 架构设计

### 5.1 模块目标

JY61P 模块对上层提供车体系姿态与惯性数据：

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

### 5.2 通信方式

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

### 5.3 初始化流程

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

### 5.4 寄存器读取规划

推荐一次连续读取 `0x34~0x40` 共 13 个 16-bit 寄存器，即 26 字节。

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

### 5.5 数据帧格式理解

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

I2C 模式下数据有效性依靠：

1. HAL I2C 返回值。
2. 数据范围检查。
3. 连续样本跳变检查。
4. 时间戳超时检查。
5. 静止物理约束检查。

### 5.6 数据接收方式

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

### 5.7 车体系映射

已知安装方向：JY61P +Y 朝车前，+X 朝车右。

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

建议预留符号宏：

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

### 5.8 数据解析流程

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

### 5.9 数据有效性判断

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

### 5.10 滤波策略

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

### 5.11 累计误差抑制方案

本项目不使用卡尔曼滤波。JY61P 累计误差通过组合策略抑制。

#### 5.11.1 上电静止零偏校准

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

#### 5.11.2 运行中静止零速更新

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

零速更新只缓慢修正 gyro 零偏，不频繁改 `yaw_zero_deg`，防止控制中 yaw 突跳。

#### 5.11.3 分段航向归零

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

#### 5.11.4 互补滤波

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

概念流程：

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

### 5.12 与运动控制接口

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

---

## 6. ATK-MS53L1M / VL53L1X 架构设计

### 6.1 模块目标

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

### 6.2 通信与地址

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

### 6.3 初始化流程

| 步骤 | 处理 |
|---|---|
| 1 | `ATK_MS53L1M_Init()` 接收 `I2C_HandleTypeDef *` 和当前时间戳。 |
| 2 | 保存地址 `0x29` 和 HAL 地址 `0x52`。 |
| 3 | 使用短超时检测设备 ready。 |
| 4 | 调用 VL53L1X 默认启动封装。 |
| 5 | 清空滤波缓存、错误计数、距离缓存。 |
| 6 | 进入 `ATK_MS53L1M_STATE_RUNNING`。 |

> VL53L1X 的 ID、Long 模式、Timing Budget、Inter-measurement 等细节按用户要求忽略，后续实现时由选定的底层 VL53L1X 库或默认启动函数内部处理。

### 6.4 测距模式选择

| 模式 | 是否使用 | 说明 |
|---|---|---|
| 连续测量 | 使用 | 适合小车实时避障。 |
| 单次测量 | 不作为默认 | 可作为调试接口保留。 |
| UART 输出 | 不使用 | 本项目 VL53L1X 直连 I2C。 |

### 6.5 测距周期和有效范围

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

### 6.6 数据读取流程

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

### 6.7 滤波与异常剔除

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

### 6.8 单车头激光限制

| 限制 | 处理 |
|---|---|
| 只能检测正前方 | 控制层不得把它当成全向避障。 |
| 斜面、黑色、透明目标可能异常 | 用滤波与无效状态处理。 |
| 快速靠近障碍 | 近距离样本优先触发停车，不被平均滤波延迟。 |
| 数据失效 | 限速或停车。 |

---

## 7. 持续测量与实时更新机制

### 7.1 初始化阶段

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

### 7.2 主循环调度

| 周期 | 任务 |
|---|---|
| 每轮循环 | 获取 `HAL_GetTick()`。 |
| 10 ms | `IMU_App_Loop()`（内部调用 `JY61P_ReadAll()`）。 |
| 20 ms | `ATK_MS53L1M_Update()`。 |
| 20 ms | `sensor_update_snapshot()`。 |
| 10~20 ms | 电机控制层读取快照，计算 UART1 电机命令。 |
| 500~1000 ms | 输出诊断日志。 |

### 7.3 数据缓存方式

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

### 7.4 避免阻塞主循环

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

### 7.5 I2C 总线恢复

建议统一传感器层提供：

| 接口 | 作用 |
|---|---|

一个设备错误时先标记单设备 fault，不影响另一个设备读取。

---

## 8. 与电机控制模块的配合方式

### 8.1 电机接口

| 项目 | 设计 |
|---|---|
| 电机通信外设 | UART1。 |
| TX | PA9。 |
| RX | PA10。 |
| 传感器层是否直接发电机命令 | 否。 |
| 电机协议 | 未提供，本文不定义协议帧。 |

### 8.2 传感器快照给电机控制层的数据

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

### 8.3 典型控制策略

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

---

## 9. 状态机与错误处理

### 9.1 通用状态

| 状态 | 含义 |
|---|---|
| `RUNNING` | 正常运行。 |
| `CALIBRATING` | 校准中（仅 JY61P）。 |
| `ERROR` | 通信失败/数据异常。 |

### 9.2 JY61P 状态机

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

### 9.3 VL53L1X 状态机

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

### 9.4 错误处理原则

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

---

## 10. 推荐 API 设计

### 10.1 JY61P API

| 函数名 | 功能 | 输入参数 | 输出参数 | 返回值含义 | 调用时机 | 是否阻塞 | HAL 依赖 |
|---|---|---|---|---|---|---|---|
| `JY61P_Init` | 初始化设备对象和通信检测 | I2C 句柄、地址、时间戳 | 设备对象状态 | 成功/失败 | 系统初始化 | 短阻塞 | I2C1 |
| `JY61P_Update` | 周期读取并更新姿态 | 设备对象、时间戳 | 内部缓存 | 成功/错误/无效 | 10 ms 周期 | 短阻塞 | I2C1 |
| `JY61P_ReadRaw` | 读取原始寄存器 | 设备对象 | 原始缓存 | 成功/I2C 错误 | update 内部 | 短阻塞 | I2C1 |
| `JY61P_ParseRaw` | 原始数据换算物理量 | 原始缓存 | 姿态/惯性数据 | 成功/无效 | update 内部 | 不阻塞 | 无 |
| `JY61P_GetAttitude` | 获取最近姿态 | 设备对象 | 姿态副本 | 成功/无效 | 电机控制 | 不阻塞 | 无 |
| `JY61P_StartCalibration` | 启动校准 | 设备对象、校准类型 | 状态变化 | 成功/条件不满足 | 上电或命令 | 不阻塞 | 无 |
| `JY61P_CalibrationStep` | 分步执行校准 | 设备对象、时间戳 | 进度 | 进行中/成功/失败 | 主循环 | 短阻塞 | I2C1 |
| `JY61P_SetYawZero` | 设置当前 yaw 为段内零位 | 设备对象 | 校准参数 | 成功/无效 | 直线段开始 | 不阻塞 | 无 |
| `JY61P_Recover` | 错误恢复 | 设备对象、时间戳 | 状态变化 | 成功/失败 | 错误状态 | 短阻塞 | I2C1 |
| `JY61P_GetState` | 获取状态和错误 | 设备对象 | 状态副本 | 成功 | 任意时刻 | 不阻塞 | 无 |

### 10.2 ATK-MS53L1M / VL53L1X API

| 函数名 | 功能 | 输入参数 | 输出参数 | 返回值含义 | 调用时机 | 是否阻塞 | HAL 依赖 |
|---|---|---|---|---|---|---|---|
| `ATK_MS53L1M_Init` | 初始化测距模块 | I2C 句柄、地址、时间戳 | 设备对象 | 成功/失败 | 系统初始化 | 短阻塞 | I2C1 |
| `ATK_MS53L1M_StartDefault` | 启动 VL53L1X 默认测距 | 设备对象 | 状态变化 | 成功/失败 | 初始化内 | 短阻塞 | I2C1 |
| `ATK_MS53L1M_Update` | 周期读取距离 | 设备对象、时间戳 | 距离缓存 | 成功/未 ready/错误 | 20 ms 周期 | 短阻塞 | I2C1 |
| `ATK_MS53L1M_ReadDistanceRaw` | 读取原始距离 | 设备对象 | 原始距离 mm | 成功/错误 | update 内部 | 短阻塞 | I2C1 |
| `ATK_MS53L1M_FilterUpdate` | 更新滤波器 | 原始距离 | 稳定距离 | 成功/异常/样本不足 | 读取成功后 | 不阻塞 | 无 |
| `ATK_MS53L1M_GetDistance` | 获取稳定距离 | 设备对象 | 距离副本 | 成功/无效 | 电机控制 | 不阻塞 | 无 |
| `ATK_MS53L1M_Recover` | 错误恢复 | 设备对象、时间戳 | 状态变化 | 成功/失败 | 错误状态 | 短阻塞 | I2C1 |
| `ATK_MS53L1M_GetState` | 获取状态和错误 | 设备对象 | 状态副本 | 成功 | 任意时刻 | 不阻塞 | 无 |

### 10.3 统一传感器层 API

| 函数名 | 功能 | 输入参数 | 输出参数 | 调用时机 |
|---|---|---|---|---|

---

## 11. 推荐数据结构设计

> 本节只描述结构体字段，不提供完整 C 代码。

### 11.1 `JY61P_RawData_t`

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

### 11.2 `JY61P_Attitude_t`

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

### 11.3 `JY61P_CalibParam_t`

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

### 11.4 `JY61P_Device_t`

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

### 11.5 `ATK_MS53L1M_Distance_t`

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

### 11.6 `ATK_MS53L1M_Filter_t`

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

### 11.7 `ATK_MS53L1M_Device_t`

| 字段 | 类型建议 | 说明 |
|---|---|---|
| `i2c` | `I2C_HandleTypeDef *` | I2C 句柄。 |
| `addr_7bit` | `uint8_t` | `0x29`。 |
| `addr_hal` | `uint16_t` | `0x52`。 |
| `state` | `ATK_MS53L1M_State_t` | 当前状态。 |
| `last_error` | `ATK_MS53L1M_Error_t` | 最近错误。 |
| `distance` | `ATK_MS53L1M_Distance_t` | 距离数据。 |
| `filter` | `ATK_MS53L1M_Filter_t` | 滤波缓存。 |
| `error_count` | `uint16_t` | 总错误计数。 |
| `consecutive_error_count` | `uint16_t` | 连续错误计数。 |
| `last_poll_ms` | `uint32_t` | 最近轮询时间。 |

---

## 12. 关键参数表

| 推荐宏名 | 默认值 | 单位 | 所属模块 | 是否需实测调整 | 说明 |
|---|---:|---|---|---|---|
| `JY61P_I2C_ADDR_7BIT` | `0x50` | - | JY61P | 否 | JY61P 地址。 |
| `JY61P_I2C_ADDR_HAL` | `0xA0` | - | JY61P | 否 | HAL 地址。 |
| `ATK_MS53L1M_I2C_ADDR_8BIT` | `0x29` | - | VL53L1X | 否 | VL53L1X 地址。 |
| `ATK_MS53L1M_I2C_ADDR_8BIT` | `0x52` | - | VL53L1X | 否 | HAL 地址。 |
| `SENSOR_I2C_TIMEOUT_MS` | 5 | ms | 统一层 | 是 | I2C 短超时。 |
| `JY61P_UPDATE_PERIOD_MS` | 10 | ms | JY61P | 是 | 姿态刷新周期。 |
| `JY61P_DATA_TIMEOUT_MS` | 100 | ms | JY61P | 是 | 姿态数据超时。 |
| `JY61P_CALIB_SAMPLE_COUNT` | 200 | 次 | JY61P | 是 | 校准采样次数。 |
| `JY61P_CALIB_SAMPLE_PERIOD_MS` | 10 | ms | JY61P | 是 | 校准采样周期。 |
| `JY61P_GYRO_STILL_THRESHOLD_DPS` | 1.5 | °/s | JY61P | 是 | 静止角速度阈值。 |
| `JY61P_ACC_NORM_MIN_G` | 0.95 | g | JY61P | 是 | 静止加速度模长下限。 |
| `JY61P_ACC_NORM_MAX_G` | 1.05 | g | JY61P | 是 | 静止加速度模长上限。 |
| `JY61P_FILTER_ALPHA_ATT` | 0.3 | - | JY61P | 是 | 姿态一阶低通系数。 |
| `JY61P_YAW_FILTER_GYRO_WEIGHT` | 0.98 | - | JY61P | 是 | yaw 互补滤波 gyro 权重。 |
| `JY61P_YAW_FILTER_ANGLE_WEIGHT` | 0.02 | - | JY61P | 是 | yaw 互补滤波角度权重。 |
| `JY61P_YAW_CONTROL_LIMIT_DEG` | 30 | deg | 控制接口 | 是 | yaw 纠偏限幅。 |
| `MS53L1M_UPDATE_PERIOD_MS` | 20 | ms | VL53L1X | 是 | 测距轮询周期。 |
| `MS53L1M_DATA_TIMEOUT_MS` | 500 | ms | VL53L1X | 是 | 测距数据超时。 |
| `MS53L1M_MIN_VALID_MM` | 40 | mm | VL53L1X | 是 | 最小有效距离。 |
| `MS53L1M_MAX_VALID_MM` | 4000 | mm | VL53L1X | 是 | 最大有效距离。 |
| `MS53L1M_WARN_DISTANCE_MM` | 600 | mm | VL53L1X | 是 | 预警距离。 |
| `MS53L1M_SLOW_DISTANCE_MM` | 300 | mm | VL53L1X | 是 | 减速距离。 |
| `MS53L1M_STOP_DISTANCE_MM` | 150 | mm | VL53L1X | 是 | 停车距离。 |
| `MS53L1M_MEDIAN_WINDOW` | 3 | 次 | VL53L1X | 是 | 中值滤波窗口。 |
| `MS53L1M_AVG_WINDOW` | 5 | 次 | VL53L1X | 是 | 滑动平均窗口。 |
| `MS53L1M_JUMP_REJECT_MM` | 300 | mm | VL53L1X | 是 | 跳变剔除阈值。 |
| `SENSOR_I2C_RECOVER_PULSE_COUNT` | 9 | 次 | 统一层 | 是 | I2C 总线恢复 SCL 脉冲数。 |
| `SENSOR_FAULT_RECOVER_PERIOD_MS` | 1000 | ms | 统一层 | 是 | 故障恢复尝试间隔。 |

---

## 13. 文件组织建议

### 13.1 工程目录

```text
Core/
  Inc/
    jy61p.h
    atk_ms53l1m.h
    board_app.h
    imu_app.h
    laser_app.h
  Src/
    jy61p.c
    atk_ms53l1m.c
    board_app.c
    imu_app.c
    laser_app.c
```

### 13.2 CubeIDE 生成代码注意事项

| 文件 | 处理方式 |
|---|---|
| `main.c` | 只能在 `USER CODE BEGIN` / `USER CODE END` 区域调用传感器初始化和周期更新。 |
| `i2c.c` / `i2c.h` | 由 CubeIDE 生成，不在传感器驱动中修改 I2C 初始化细节。 |
| `usart.c` / `usart.h` | UART1 电机配置由 CubeIDE 或电机模块处理。 |
| `jy61p.c/h` | 用户自建文件，不被 CubeMX 覆盖。 |
| `atk_ms53l1m.c/h` | 用户自建文件，不被 CubeMX 覆盖。 |
| `imu_app.c/h`、`laser_app.c/h` | 用户自建文件，不被 CubeMX 覆盖。 |

### 13.3 `main.c` 调用关系

初始化阶段：

1. HAL 初始化。
2. 系统时钟初始化。
3. GPIO 初始化。
4. I2C1 初始化。
5. UART1 初始化。
6. 调用 `Board_App_Init()`。
7. 进入主循环。

主循环阶段：

1. 获取 `now_ms = HAL_GetTick()`。
2. 调用 `Board_App_Loop()`。
3. 读取 `g_imu_*` 和 `g_laser_*` 公开变量。
4. 电机控制层通过 UART1 输出控制命令。
5. 定期输出诊断日志。

---

## 14. 验收标准

### 14.1 编译层面

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

### 14.2 初始化层面

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

### 14.3 JY61P 数据读取层面

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

### 14.4 JY61P 校准与误差抑制层面

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

### 14.5 VL53L1X 测距层面

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

### 14.6 I2C 总线与连续运行

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

| B-05 | 主循环无明显卡顿，UART1 电机控制仍能按周期运行。 |

### 14.7 与电机控制接口层面

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

---

## 15. 测试步骤

### 15.1 单独测试 JY61P

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

### 15.2 单独测试 VL53L1X

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

### 15.3 两个传感器同时运行测试

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

### 15.4 静止状态测试

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

### 15.5 小车移动状态测试

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

### 15.6 前方障碍物距离变化测试

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

### 15.7 姿态变化测试

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

### 15.8 通信异常测试

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

### 15.9 长时间运行测试

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

---

## 16. 未验证风险

| 风险项 | 当前状态 | 影响 | 建议处理 |
|---|---|---|---|
| STM32C8T6 具体完整型号 | 用户给出 STM32C8T6，本文按 STM32F103C8T6 类资源处理 | 若具体芯片资源差异较大，外设或 Flash/RAM 可能不同 | 【已决策，需验证】实物丝印和 `.ioc` 最终确认。 |
| JY61P Z 轴方向 | 用户明确 X 朝右、Y 朝前；Z 未明确 | 可能导致 down、yaw、roll/pitch 符号不一致 | 【已决策，需验证】默认板面朝上，保留符号宏，实测后修正。 |
| JY61P 姿态角映射 | 安装方向导致 JY61P 原始 Roll/Pitch 与车体系不完全同名 | 上层若直接使用原始角度可能控制反向 | 【已决策，需验证】统一输出 `car_*` 字段，禁止上层直接使用原始角。 |
| JY61P yaw 累计误差 | 纯 IMU 航向无法完全消除漂移 | 长时间直线控制可能偏航 | 使用上电校准、零速更新、分段归零、互补滤波、误差限幅。 |
| 实车震动 | 未完成实车验证 | 姿态和角速度抖动 | 实测调整滤波系数、静止阈值、yaw 限幅。 |
| I2C 上拉 5V | 已确认 | GPIO 恢复若主动输出高电平可能有硬件风险 | 保持开漏；恢复过程只拉低或释放总线。 |
| I2C 共总线异常 | 两传感器共用 PB6/PB7 | 一个设备异常可能影响另一个设备 | 短超时、错误隔离、bus recovery、断开单设备验收测试。 |
| VL53L1X 默认启动封装 | 用户要求忽略底层细节，但后续仍需具体库实现 | 后续写代码时需要绑定 ST API、ATK 示例库或自写底层读写 | 【已决策，需验证】架构只暴露 `ATK_MS53L1M_StartDefault()`，实现阶段绑定具体库。 |
| VL53L1X 有效距离表现 | 按 40~4000 mm 设计 | 黑色、透明、斜面、强光可能异常 | 实测 100/150/300/600/1000/2000/4000 mm，调整阈值。 |
| 单个车头激光视野有限 | 已知限制 | 无法判断左右侧障碍 | 控制层仅作为正前方避障；后续需要侧向避障时增加传感器。 |
| UART1 电机协议 | 仅确认 PA9/PA10，未提供波特率和协议帧 | 传感器层能提供数据，但不能直接定义电机命令格式 | 【已决策，需验证】传感器层只输出快照，电机协议另行设计。 |
| 旧功能回归范围 | 其他旧功能未说明 | 集成传感器后可能影响已有功能 | 最低回归：UART1 电机收发、I2C1 双传感器、主循环不卡顿、距离触发停车、IMU 姿态保护。 |

---

## 附录：后续低成本模型补代码时的执行顺序建议

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
