Chemcrin/IntelligentTransformCart/代码/VibeCoding/姿态模块资料包/姿态框架代码生成提示词.md

# 角色

你现在是一位资深嵌入式开发工程师，精通 STM32、C 语言、STM32CubeIDE、HAL 库、I2C 通信、传感器驱动、姿态解算、实时控制系统设计。

# 任务
本任务面向一个“智能物流搬运小车”项目。你需要接手其中的传感器姿态与距离感知部分，并根据现有代码架构文档，按照cubeIDE的格式，生成一份简洁、可用、稳定的代码文件，并将整理完成的代码文件夹ATK_JY61P_NewGen放在目录D:\AI_agent\Code下。
# 硬件架构
现有的硬件是一块stm32C8T6开发板，以及通过i2c1与32开发板连接的ATK-MS53L1M激光传感器和JY61P陀螺仪，他们均作为i2c1的从机，连接在pb6、pb7引脚下。具体细节请详细阅读[[传感器代码架构设计_精简版V2]]

# 项目要求与验收标准
请根据传感器代码架构设计_精简版.md这份文档进行代码的填充，需要你完成两个传感器数据的持续回传与数据读取，数据可小车的其他模块使用；在D:\AI_agent\Code下新建项目文件夹，名称为ATK_JY_NewVer_GPT，里面要按stm32cubeIDE的工程格式存放代码，包括core文件夹下的src和inc文件夹。验收标准是：能够按照md文件的里的要求完成代码任务，代码清晰简洁可用，能够持续获取两个传感器获得的信息，并且传入md文档里规范的变量名中。

# 工程自查
在生成代码前，请回复我是否有不理解不明白的部分，如果信息全面请开始填充代码。

# 项目收尾
在代码生成完成后，整理一份md文档，告知我项目都包含了什么代码文件，以及告诉我怎样导入cubeIDE，还有ioc的引脚配置方式
