Chemcrin/IntelligentTransformCart/代码/VibeCoding/姿态模块资料包/智能物流小车_JY61P与ATK-MS53L1M传感器代码架构设计.md

# 智能物流小车 JY61P 与 ATK-MS53L1M 传感器代码架构设计文档

> 文档用途：指导后续模型在 STM32CubeIDE + HAL + C 语言环境下补全 JY61P 姿态传感器与 ATK-MS53L1M 激光测距模块的 `.c` / `.h` 文件。  
> 当前边界：本文只做代码架构设计、接口设计、数据结构设计、测试与验收要求，不包含完整 `.c` / `.h` 实现代码。  
> 日期：2026-05-18  
> 目标 MCU：STM32C8T6，架构按 STM32F103C8T6 设计；若实物存在差异，标记为 `待确认`。  
*本文书写时有笔误，本文所有的MS53LM/ms53lm均为MS53L1M/ms53l1m*
*为节约PCB布板时间，i2c1供电均为5V，后期代码请适配5V而不是3.3V*
## 1. 需求完整性检查表

| 检查项 | 判断 | 说明 | 建议补充内容 |
| --- | ---- | --- | --- |
| 是否说明了最终目标，而不是只描述模糊愿望 | 是 | 目标明确：为 JY61P 与 ATK-MS53L1M 两个传感器生成可指导后续代码实现的 Markdown 架构文档。 | 无。 |
| 是否提供了当前工程状态、文件路径、代码或日志 | 部分满足 | 已提供资料包路径；资料包内包含 Markdown 和两张截图。本机还搜索到 JY61P PDF、ATK-MS53L1M PDF 和已有参考框架代码。 | 补充最终要集成的 STM32CubeIDE 工程根目录、已有 `Core/Inc`、`Core/Src` 文件状态。 |
| 是否写清硬件、工具链、库版本和外设连接 | 部分满足 | 已说明 STM32C8T6/STM32F103C8T6、STM32CubeIDE、HAL、C 语言、I2C1 PB6/PB7。HAL 包版本、JY61P 最终通信方式仍需实物确认。 | 补充 STM32CubeIDE 版本、STM32CubeF1 HAL 包版本、JY61P 实物最终接线。 |
| 是否说明本轮允许修改和禁止修改范围 | 是 | 明确本轮禁止生成 `.c` / `.h` 实现代码，只生成架构文档。 | 无。 |
| 是否定义可观察、可测试的验收标准 | 部分满足 | 用户要求文档必须包含验收标准，但未给出现有项目的具体阈值。 | 本文给出建议验收标准，后续应按实车测试修订。 |
| 是否说明旧功能中哪些必须回归验证 | 部分满足 | 已提到后续电机控制、避障、姿态修正、路径控制，但没有完整旧功能清单。 | 补充树莓派通信、电机链路、安全停车、状态上报等旧功能是否必须回归。 |
| 是否要求输出测试步骤和未验证风险 | 是 | 明确要求包含测试步骤和未验证风险。 | 无。 |
| 如果是改进需求，是否同步修改验收标准 | 部分满足 | 本任务属于架构设计/改进需求，要求输出验收标准，但尚无旧验收标准。 | 后续代码实现后，将本文验收标准固化到 README 或测试记录。 |

## 2. 资料理解与确认结论

### 2.1 已读取资料

| 来源 | 读取结果 |
| --- | --- |
| `C:\Users\CloudyRain\Desktop\姿态模块资料包\智能物流小车-硬件平台技术手册V2.1.md` | 已读取“传感器连接与数据采集”“数据接收与分发”“推荐裸机调度”等相关段落。 |
| `C:\Users\CloudyRain\Desktop\姿态模块资料包\引脚原理图.png` | 已确认 PB6/PB7 与 JY61P、ATK-MS53L1M 的 I2C 连接关系。 |
| `C:\Users\CloudyRain\Desktop\姿态模块资料包\ioc配置.png` | 已确认 CubeMX 配置为 PB6 = I2C1_SCL，PB7 = I2C1_SDA。 |
| JY61P PDF | 资料包内未直接提供 PDF；本机搜索到 `JY61P产品IIC协议.pdf`、`JY61P产品规格书.pdf` 并读取。 |
| ATK-MS53L1M PDF | 本机搜索到 `ATK-MS53L1M_UserManual_V1.1.pdf`、`ATK-MS53L1M_V1.3.pdf` 并读取。 |
| 现有参考框架代码 | 本机存在 `stm32cubeide_atk_ms53l1m_i2c_framework`，其中包含 JY61P/ATK-MS53L1M 参考代码。本文只提取架构参数，不生成实现代码。 |

### 2.2 从项目 Markdown 文档提取到的需求

| 项目 | 结论 |
|---|---|
| 系统定位 | STM32F103C8T6 负责实时采集、通信转发、安全保护；树莓派负责高层任务。 |
| JY61P 职责 | 提供 Roll、Pitch、Yaw、三轴加速度、三轴角速度、温度，并带时间戳和有效标志。 |
| ATK-MS53LM 职责 | 提供前方距离 mm、测量状态、样本计数，并支持避障、减速和停车判断。 |
| I2C 总线 | 文档总体和变更记录确认 I2C1 使用 PB6/PB7，100 kHz 起步。 |
| 数据刷新 | IMU 建议 10-20 ms；激光测距建议 100-200 ms，已有资料中 Long 模式默认约 150 ms。 |
| 数据缓存 | 每个传感器数据应保留 `last_update_ms`、`valid`、错误计数和最近一次有效值。 |
| 实时性要求 | 避免长时间阻塞 I2C 操作，错误后快速返回并上报状态。 |
| 文档冲突 | Markdown 3.1 段曾写 PB8/PB9，JY61P 表格曾写 SCL/SDA 互换；与原理图和 IOC 冲突。本文以截图与 IOC 为准：PB6=SCL，PB7=SDA。 |

### 2.3 从 JY61P PDF 提取到的关键信息

| 项目 | 已确认信息 |
|---|---|
| 通信接口 | JY61P 支持 UART 和 IIC。本文按 IIC 架构设计，因为原理图和当前项目文档显示 JY61P 接 I2C1。若实物改接 UART，则标记为 `待确认`。 |
| IIC 地址 | 默认 7-bit 地址 `0x50`，HAL 8-bit 地址应使用 `0xA0`。 |
| IIC 速率 | 硬件 I2C 最大 400 kHz；项目调试阶段建议 100 kHz。 |
| 寄存器访问 | IIC 协议采用寄存器地址访问；每个寄存器为 16 位，占 2 字节；低字节在前，高字节在后。 |
| 数据解析类型 | 数据应按有符号 `int16_t` 解析。 |
| 加速度寄存器 | `0x34-0x36`，AX/AY/AZ。 |
| 角速度寄存器 | `0x37-0x39`，GX/GY/GZ。 |
| 磁场寄存器 | `0x3A-0x3C`，HX/HY/HZ，可保留但当前控制不强依赖。 |
| 姿态角寄存器 | `0x3D-0x3F`，Roll/Pitch/Yaw。 |
| 温度寄存器 | `0x40`，TEMP。 |
| 转换关系 | 加速度 `raw / 32768 * 16g`；角速度 `raw / 32768 * 2000 deg/s`；角度 `raw / 32768 * 180 deg`；温度 `raw / 100 ℃`。 |
| 写保护/解锁 | 写配置寄存器前需写 `KEY=0xB588` 到 `0x69` 解锁，之后写目标寄存器，最后写 `SAVE=0x0000` 到 `0x00` 保存。 |
| 校准寄存器 | `0x01 CALSW`：`0x01` 自动加计校准，`0x04` 航向角置零，`0x08` 设置角度参考，`0x07/0x09` 为磁场校准。 |
| 自动静止校准 | `GYROCALITHR=0x61`、`GYROCALTIME=0x63` 可配合静止识别；资料说明角速度变化小且持续指定时间后可自动将小角速度归零。 |
| 规格风险 | 规格书说明 6 轴航向动态存在积分累计误差；震动环境累计误差不可直接估计，需要实测。 |

### 2.4 从 ATK-MS53L1M PDF 提取到的关键信息

| 项目 | 已确认信息 |
| --- | --- |
| 通信接口 | 模块支持 UART/IIC；当前项目指定使用 I2C1，因此采用 IIC/VL53L1X 架构。 |
| 引脚 | VCC、GND、TXD、RXD、SCL、SDA；IIC 模式使用 SCL/SDA，TXD/RXD 不使用。 |
| 电气 | 供电 3.3V/5V；通信引脚仅支持 3.3V；模块 SCL/SDA 内部已上拉 10 kΩ。 |
| 测距范围 | 40 mm - 3900 mm；无光学镜片可到 4000 mm。 |
| 测距单位 | mm。 |
| 测量模式 | 短距离最远约 1.3 m，中距离约 3 m，长距离约 4 m；默认长距离。 |
| 默认周期 | 长距离默认 Timing Budget 140 ms，测量间隔 150 ms。 |
| 测量状态 | Range Valid、Sigma Fail、Signal Fail、Min Range Fail、Phase Fail、Hardware Fail、No Update 等状态需保留。 |
| IIC 工作模式 | IIC 模式下模块内部控制芯片释放传感器 IIC 总线，SDA/SCL 直接连接内部 VL53L1X 类传感器；实现应参考 VL53L1X API。 |
| 参考框架确认 | I2C 8-bit 地址 `0x52`，即 7-bit `0x29`；模块 ID 寄存器 `0x010F`，期望值 `0xEACC`；距离字段为 `RangeMilliMeter`。  |

### 2.5 从原理图截图确认的引脚连接

| 信号 | STM32 引脚 | 结论 |
|---|---:|---|
| I2C1_SCL | PB6 | 已确认。原理图中 ATK-SCL 与 JY61P-SCL 接 PB6；IOC 也显示 PB6 = I2C1_SCL。 |
| I2C1_SDA | PB7 | 已确认。原理图中 ATK-SDA 与 JY61P-SDA 接 PB7；IOC 也显示 PB7 = I2C1_SDA。 |
| ATK-MS53LM | I2C1 共总线 | 已确认使用 I2C1。 |
| JY61P | I2C1 共总线 | 从原理图和当前项目文档推断为 I2C1；若实物改用 UART，需重新确认。 |

### 2.6 已确认、缺失与待确认

| 类别  | 内容 |
| --- | --- |
| 已确认 | MCU 架构按 STM32F103C8T6；开发环境为 STM32CubeIDE + HAL + C；I2C1 使用 PB6/PB7；ATK 使用 I2C1；JY61P IIC 默认地址 `0x50`；ATK/VL53L1X I2C 默认地址 `0x29`；激光距离单位 mm；JY61P 数据转换关系。 |
| 缺失  | 最终 STM32CubeIDE 工程目录、HAL 库版本、是否已有 `sensors.c/h`、是否使用 DMA、是否使用 RTOS、电机控制接口定义、传感器安装方向、JY61P 实物最终通信方式。 |
| 待确认 | PB6/PB7 上拉电压是否为 3.3V；JY61P 是否确实工作在 IIC 模式；JY61P 坐标系与车体坐标系关系；激光安装高度和朝向；避障阈值。 |

## 3. 总体设计目标

JY61P 负责读取智能物流搬运小车的姿态与惯性数据，包括偏航角、俯仰角、横滚角、三轴角速度、三轴加速度和温度。ATK-MS53L1M 负责车头前方单点激光测距，输出前向障碍距离、测量状态和数据更新时间。

两个传感器的数据需要统一缓存，供后续电机控制、避障、姿态修正、路径控制、安全停车和上位机遥测使用。设计重点如下：

| 目标 | 说明 |
|---|---|
| 实时性 | JY61P 10-20 ms 更新；激光 20 ms 轮询 ready，约 150 ms 刷新一次有效距离。 |
| 非阻塞 | 主循环不能被长时间 I2C 等待卡住；I2C 超时要短，失败后快速返回。 |
| 可诊断 | 每个模块有状态机、错误计数、最近错误码、更新时间戳。 |
| 数据稳定 | 姿态做零偏校准和轻量滤波；距离做中值/滑动平均/异常值剔除。 |
| 上层友好 | 电机控制层读取快照，不直接访问 I2C 或底层驱动。 |

## 4. 模块拆分

### 4.1 文件列表

| 文件 | 职责 | 关键内容 |
|---|---|---|
| `Core/Inc/jy61p.h` | JY61P 对外接口声明 | 宏、状态枚举、姿态/原始/校准结构体、初始化/更新/读取/校准接口。 |
| `Core/Src/jy61p.c` | JY61P IIC 驱动与数据处理 | I2C 寄存器读写、数据转换、有效性判断、零偏校准、滤波、状态机。 |
| `Core/Inc/atk_ms53lm.h` | 激光测距对外接口声明 | 地址、测距模式、状态枚举、距离结构体、滤波缓存、初始化/更新/读取接口。 |
| `Core/Src/atk_ms53lm.c` | VL53L1X/ATK IIC 驱动适配 | 设备 ID 检查、测距启动、DataReady 轮询、距离读取、状态解析、滤波。 |
| `Core/Inc/sensors.h` | 可选统一传感器管理层 | 汇总 IMU/激光状态，向运动控制层提供统一快照。 |
| `Core/Src/sensors.c` | 可选统一调度与健康管理 | 周期调用两个底层模块，统一超时、错误恢复、遥测数据组织。 |

### 4.2 HAL 外设句柄关系

| 模块 | HAL 句柄 | 说明 |
| --- | --- | --- |
| JY61P | `I2C_HandleTypeDef *hi2c`，实际传入 `&hi2c1` | 驱动内部保存指针，不自行初始化 I2C 外设。 |
| ATK-MS53LM | `I2C_HandleTypeDef *hi2c`，实际传入 `&hi2c1` | 需确保 VL53L1X API 的平台层使用同一个 `hi2c1`。 |
| sensors | 同时持有 JY61P 和 MS53L1M 句柄 | 只做调度和数据聚合。 |

### 4.3 主循环、定时器、中断、DMA 关系

| 机制 | 设计建议 |
|---|---|
| 主循环 | 推荐初版使用主循环轮询状态机，调用 `sensor_update_all(HAL_GetTick())`。 |
| 定时器 | 可使用 1 ms 系统节拍或 `HAL_GetTick()` 做软定时，不必单独开硬件定时器。 |
| I2C 中断 | 初版不推荐，避免 HAL I2C 状态机复杂化。 |
| I2C DMA | 初版不推荐；后续若主循环阻塞明显，再引入。 |
| 串口中断 | 若电机或树莓派通信使用串口中断，ISR 只入队，不做复杂传感器处理。 |

## 5. 命名规范

| 类型 | 规范 |
|---|---|
| JY61P 宏 | `JY61P_I2C_ADDR_7BIT`、`JY61P_REG_AX`、`JY61P_UPDATE_PERIOD_MS` |
| JY61P 函数 | `jy61p_init`、`jy61p_update`、`jy61p_get_pose`、`jy61p_start_static_calibration` |
| JY61P 类型 | `JY61P_State_t`、`JY61P_Attitude_t`、`JY61P_Calib_t` |
| 激光宏 | `MS53LM_I2C_ADDR_7BIT`、`MS53LM_MEASURE_PERIOD_MS`、`MS53LM_FILTER_WINDOW` |
| 激光函数 | `ms53lm_init`、`ms53lm_update`、`ms53lm_get_distance`、`ms53lm_recover` |
| 激光类型 | `MS53LM_State_t`、`MS53LM_Distance_t`、`MS53LM_Filter_t` |
| 统一层宏/函数 | `SENSOR_FRONT_STOP_MM`、`sensor_init_all`、`sensor_update_all`、`sensor_get_snapshot` |
| 导航/车体状态 | `NAV_CarPose_t`、`car_pose_yaw_deg`、`nav_front_distance_mm` |

禁止在全局作用域使用 `data`、`buf`、`angle`、`distance` 等过泛名称。局部变量也建议写成 `jy61p_rx_bytes`、`ms53lm_raw_distance_mm`、`sensor_now_ms`。

## 6. 硬件连接与外设配置

| 项目 | 配置 |
|---|---|
| MCU | STM32F103C8T6；若实际为其他 STM32C8T6 兼容芯片，`待确认`。 |
| I2C 外设 | I2C1。 |
| SCL | PB6。 |
| SDA | PB7。 |
| HAL 句柄 | `hi2c1`。 |
| I2C 地址模式 | 7-bit addressing。 |
| I2C 速率 | 标准模式 100 kHz 起步；线短且波形干净后可评估 400 kHz。 |
| 上拉电阻 | ATK 模块内部 SCL/SDA 已 10 kΩ 上拉；整车总线是否还有外部上拉、上拉到 3.3V 还是 5V `待确认`。 |
| 电平风险 | STM32F103 I2C 不建议承受 5V 上拉；若实测 PB6/PB7 上拉到 5V，应改为 3.3V 或加电平转换。 |
| JY61P 通信 | 资料支持 UART/IIC；原理图显示接 I2C1，本文按 IIC 设计。若实物使用 UART，需另行调整。 |
| ATK 通信 | 当前项目指定 I2C1；TXD/RXD 不连接。 |

## 7. JY61P 架构设计

### 7.1 通信方式

JY61P 按 IIC 寄存器访问方式设计。默认 7-bit 地址 `0x50`，HAL 调用时使用 `0x50 << 1`。

注意：JY61P 也支持 UART 输出 `0x55` 帧，但本文不按 UART 主方案设计。若实物 TX/RX 已接到 STM32 串口，则 JY61P 模块需要改成 UART 解析状态机，标记为 `待确认`。

### 7.2 初始化流程

| 步骤 | 操作 |
|---|---|
| 1 | `jy61p_init(&jy61p_handle, &hi2c1)` 保存 I2C 句柄，清空状态、错误计数、滤波缓存。 |
| 2 | 等待模块启动，JY61P 规格书启动时间约 1000 ms。实际代码可在系统上电后整体延时，或状态机等待。 |
| 3 | 通过 I2C 读取版本寄存器 `0x2E` 或读取 `0x34` 起始数据，验证设备有响应。 |
| 4 | 读取一次加速度、角速度、姿态角、温度，检查数值范围。 |
| 5 | 状态进入 `JY61P_STATE_RUNNING`。若上电要求静止校准，则进入 `JY61P_STATE_CALIBRATING`。 |

初始化阶段默认不要写 JY61P 内部配置寄存器，避免误改模块参数。只有在明确需要改地址、校准或保存参数时，才执行解锁和保存流程。

### 7.3 数据寄存器与转换

| 数据 | 寄存器 | 类型 | 单位 | 转换 |
|---|---:|---|---|---|
| 加速度 X | `0x34` | `int16_t` | g | `raw / 32768 * 16` |
| 加速度 Y | `0x35` | `int16_t` | g | `raw / 32768 * 16` |
| 加速度 Z | `0x36` | `int16_t` | g | `raw / 32768 * 16` |
| 角速度 X | `0x37` | `int16_t` | deg/s | `raw / 32768 * 2000` |
| 角速度 Y | `0x38` | `int16_t` | deg/s | `raw / 32768 * 2000` |
| 角速度 Z | `0x39` | `int16_t` | deg/s | `raw / 32768 * 2000` |
| 磁场 X/Y/Z | `0x3A-0x3C` | `int16_t` | LSB | 当前保留原始值，是否参与航向修正 `待确认`。 |
| Roll | `0x3D` | `int16_t` | deg | `raw / 32768 * 180` |
| Pitch | `0x3E` | `int16_t` | deg | `raw / 32768 * 180` |
| Yaw | `0x3F` | `int16_t` | deg | `raw / 32768 * 180` |
| 温度 | `0x40` | `int16_t` | ℃ | `raw / 100` |

### 7.4 数据接收方式建议

| 方式 | 建议 | 原因 |
|---|---|---|
| 轮询 | 初版推荐 | 每 10-20 ms 做一次短 I2C 读取，逻辑简单，便于调试。 |
| 中断 | 初版不推荐 | HAL I2C 中断状态机复杂，和同总线激光模块容易产生资源争用。 |
| DMA | 后续优化 | 只有在主循环阻塞明显、数据量增大时再引入。 |

### 7.5 数据有效性判断

JY61P IIC 直接读取寄存器时没有 UART 帧校验，因此必须从以下方面判断有效性：

| 检查项 | 规则 |
|---|---|
| HAL 返回值 | I2C 读写必须返回 `HAL_OK`，否则本次数据无效。 |
| 数值范围 | Roll/Yaw 应在约 `-180~180 deg`，Pitch 应在约 `-90~90 deg` 或按模块输出范围判断。 |
| 加速度模长 | 静止时 `sqrt(ax^2+ay^2+az^2)` 应接近 1g；运动时允许偏离。 |
| 时间戳 | 超过 `JY61P_DATA_TIMEOUT_MS` 未更新则数据过期。 |
| 连续性 | 姿态角单次跳变过大时标记异常，除非角速度数据支持该变化。 |

### 7.6 滤波策略

| 数据 | 建议滤波 |
|---|---|
| 加速度 | 一阶低通，默认 `alpha=0.2-0.4`，用于降低震动噪声。 |
| 角速度 | 一阶低通，默认 `alpha=0.2-0.4`，校准时使用滤波或均值。 |
| Roll/Pitch | 轻量滑动平均 3-5 点，避免过大延迟。 |
| Yaw | 不建议强滤波；控制直线时使用相对 yaw，避免响应变慢。 |

滤波只能在新数据有效时更新。数据无效或超时时，保持最后稳定值，并将 `valid` 置 0 或 `stale` 置 1。

### 7.7 上电静止校准流程

| 步骤 | 说明 |
|---|---|
| 进入条件 | 小车上电后未允许运动，电机目标速度为 0，编码器速度为 0 或电机未使能。 |
| 静止判定 | 连续 500-1000 ms 内三轴角速度绝对值小于阈值，且加速度模长接近 1g。 |
| 推荐阈值 | `abs(gx/gy/gz) < 1.0 deg/s`；`abs(acc_norm_g - 1.0) < 0.15g`，需实测调整。 |
| 采样次数 | 100-200 组，周期 10 ms。 |
| 平均计算 | 计算 `gx/gy/gz` 均值作为软件零偏，记录当前 yaw 为 `yaw_reference_deg`。 |
| 保存策略 | 默认只保存到 RAM，不写 JY61P 内部寄存器；避免频繁写模块 Flash 或误改参数。 |
| 完成条件 | 采样数量达标且数据稳定，状态转 `RUNNING`。 |
| 失败条件 | 采样期间检测到运动、I2C 错误过多或超时，状态转 `DATA_INVALID` 或 `COMM_ERROR`。 |

### 7.8 运行中累计误差抑制策略

| 场景 | 策略 |
|---|---|
| 小车静止 | 若电机目标速度为 0、编码器速度为 0、角速度持续低于阈值，则缓慢更新软件零偏，更新增益建议 `0.001-0.01`。 |
| 直线行驶 | 不直接将 yaw 清零；记录直线起点 yaw，使用当前 yaw 与起点 yaw 的相对误差做 PID 纠偏。 |
| 转弯期间 | 禁止更新零偏，避免把真实转向角速度当成漂移。 |
| 长时间运行 | 每个任务段开始时调用 `jy61p_set_yaw_reference`，使用相对 yaw 控制。 |
| 外部融合 | 若后续有视觉、码盘里程计或磁力计标定，可由上层融合修正 yaw，传感器层不做复杂融合。 |
| 手动置零 | 可通过 JY61P `CALSW=0x04` 航向角置零，但只允许在小车静止且用户明确触发时执行。 |

### 7.9 与运动控制模块接口

JY61P 模块只提供姿态、角速度、加速度、温度、有效标志、时间戳和校准状态，不直接输出电机 PWM 或速度命令。直线纠偏、坡度判断、异常停车应由运动控制层或安全状态机完成。

## 8. ATK-MS53L1M 架构设计

### 8.1 型号与通信方式

本文按 ATK-MS53L1M 内部 VL53L1X IIC 方案设计。

| 项目 | 值 |
|---|---|
| I2C 7-bit 地址 | `0x29` |
| HAL 8-bit 地址 | `0x52` |
| 模块 ID 寄存器 | `0x010F` |
| 期望 ID | `0xEACC` |
| 距离单位 | mm |
| 推荐模式 | Long |

### 8.2 初始化流程

| 步骤  | 操作 |
| --- | --- |
| 1 | `ms53l1m_init(&ms53l1m_handle, &hi2c1)` 保存 I2C 句柄。 |
| 2 | 使用 `HAL_I2C_IsDeviceReady` 检测 `0x52` 是否响应。 |
| 3 | 读取 `0x010F`，检查是否为 `0xEACC`。 |
| 4 | 调用 VL53L1X 初始化流程：等待启动、DataInit、StaticInit。 |
| 5 | 设置距离模式为 Long。 |
| 6 | 设置 Timing Budget 为 140000 us。 |
| 7 | 设置 Inter Measurement Period 为 150 ms。 |
| 8 | 启动连续测量。 |
| 9 | 状态转 `MS53L1M_STATE_RUNNING`。 |

### 8.3 单次测量与连续测量

| 模式 | 建议 |
|---|---|
| 单次测量 | 不推荐作为初版主方案；每次启动/等待/读取会增加阻塞和延迟。 |
| 连续测量 | 推荐；初始化后持续测量，主循环只轮询 DataReady，ready 后读取结果并清中断启动下一次。 |

### 8.4 测距数据有效性判断

| 检查项 | 规则 |
|---|---|
| HAL/VL53L1X 返回值 | 任一底层错误都不更新稳定距离。 |
| DataReady | 只有 ready 为真才读取；not ready 不是错误。 |
| RangeStatus | 只有有效状态才更新 `filtered_distance_mm`。 |
| 距离范围 | 小于 40 mm 或大于 3900 mm 时标记无效；无镜片 4000 mm 上限 `待确认`。 |
| 时间戳 | 超过 `MS53LM_DATA_TIMEOUT_MS` 未获得有效数据，状态转 `DATA_TIMEOUT`。 |
| 跳变 | 与上一稳定值差值超过 `MS53LM_JUMP_REJECT_MM` 时先标记 suspect，不立即覆盖稳定值。 |

### 8.5 滤波与稳定输出

| 处理 | 设计 |
|---|---|
| 原始值 | 每次有效测量保存 `raw_distance_mm`。 |
| 中值滤波 | 保存最近 5 个有效样本，取中值抵抗单点毛刺。 |
| 滑动平均 | 对中值后的结果做 3-5 点平均，输出 `filtered_distance_mm`。 |
| 异常剔除 | 若新值与上次稳定值跳变超过 300-500 mm，且只出现 1 次，先标记 suspect。 |
| 靠近障碍 | 进入危险距离可快速响应；解除危险需连续 2-3 次有效距离恢复，避免抖动。 |
| 单传感器限制 | 单点激光只能检测正前方局部区域，不能替代视觉或多方向避障。 |

### 8.6 向上层提供的数据

| 字段 | 说明 |
|---|---|
| `raw_distance_mm` | 最新一次原始有效距离。 |
| `filtered_distance_mm` | 滤波后稳定距离，供控制和避障使用。 |
| `range_status` | VL53L1X/模块测量状态。 |
| `valid` | 当前稳定值是否有效。 |
| `too_close` | 是否小于停车阈值。 |
| `last_update_ms` | 最近一次有效距离更新时间。 |
| `sample_count` | 有效样本计数。 |
| `error_count` | I2C/VL53L1X 错误计数。 |

## 9. 持续测量与实时更新机制

### 9.1 初始化阶段

1. `HAL_Init()`。
2. 系统时钟初始化。
3. `MX_GPIO_Init()`。
4. `MX_I2C1_Init()`，PB6/PB7。
5. `sensor_init_all(&hi2c1)`。
6. JY61P 初始化，读取首帧。
7. MS53L1M 初始化，启动连续测量。
8. 若上电要求校准，执行 JY61P 静止校准，校准期间禁止电机运动。

### 9.2 主循环阶段

主循环每轮调用统一调度函数。调度函数根据 `HAL_GetTick()` 判断是否到达各模块更新时间：

| 任务 | 周期建议 | 行为 |
| --- | ---: | --- |
| JY61P 更新 |  10-20 ms | 读取寄存器、转换物理量、滤波、更新时间戳。 |
| MS53L1M ready 轮询 | 20 ms | 查询 DataReady；ready 后读取距离并滤波。 |
| 传感器健康检查 | 1-5 ms | 检查超时、错误计数、状态机转换。 |
| 状态上报 | 20-100 ms | 将快照给树莓派或调试输出。 |

### 9.3 数据缓存方式

底层模块维护自己的最新数据和状态，统一层提供快照。上层不得直接访问底层静态变量，也不得直接调用 I2C 读写函数。

| 缓存 | 更新者 | 读取者 |
|---|---|---|
| `JY61P_Attitude_t` | `jy61p_update` | `sensor_get_snapshot`、运动控制层。 |
| `JY61P_Motion_t` | `jy61p_update` | 安全状态机、运动控制层。 |
| `MS53LM_Distance_t` | `ms53lm_update` | 避障、安全状态机。 |
| `SENSOR_SystemState_t` | `sensor_update_all` | 电机控制、遥测、调试。 |

### 9.4 避免阻塞主循环

| 风险 | 处理 |
|---|---|
| I2C 读写卡住 | HAL 超时设置为 5-10 ms，不允许无限等待。 |
| 激光等待测量完成 | 不使用阻塞等待，改为 DataReady 轮询。 |
| 校准耗时 | 校准做成状态机，多次采样分散在主循环中，不一次性阻塞 2 秒。 |
| I2C 总线卡死 | 记录错误，必要时执行 bus recovery：临时 GPIO 输出 SCL 产生 9 个时钟，再重新初始化 I2C。 |

## 10. 与电机控制模块的配合方式

| 数据 | 用法 | 建议归属 |
|---|---|---|
| `yaw_deg` | 直线行驶纠偏，计算当前 yaw 与起始 yaw 的偏差。 | 运动控制层做 PID；传感器层只提供角度。 |
| `pitch_deg` | 判断坡度、上坡/下坡、异常翘头。 | 传感器层提供滤波值，上层判断阈值。 |
| `roll_deg` | 判断侧倾、碰撞、倾倒风险。 | 安全状态机处理。 |
| `ax/ay/az_g` | 判断启动、急停、震动、碰撞。 | 上层事件判断。 |
| `gx/gy/gz_dps` | 判断旋转速度、转向是否异常。 | 运动控制层使用。 |
| `front_distance_mm` | 避障、减速、停车。 | 传感器层提供 raw/filtered/status，上层生成限速或停车命令。 |

推荐控制逻辑：

| 场景 | 控制策略 |
|---|---|
| 直线行驶 | 记录起始 yaw，实时计算 yaw error，电机差速/麦轮控制用 PID 修正。 |
| 靠近障碍 | 距离小于预警阈值时限速，距离小于硬停车阈值时停车。 |
| 坡度变化 | Pitch 超过阈值时限速，并上报地形变化。 |
| 姿态异常 | Roll/Pitch 或角速度超过安全阈值时停车或降级。 |
| 传感器超时 | IMU 超时禁用姿态闭环；激光超时禁用自动前进或降速。 |

## 11. 状态机与错误处理

### 11.1 通用状态机

| 状态 | 进入条件 | 退出条件 | 上层处理 |
|---|---|---|---|
| `UNINIT` | 上电默认 | 调用 init | 不使用数据。 |
| `INITING` | 正在初始化 | 成功转 `RUNNING`，失败转 `COMM_ERROR` | 禁止运动。 |
| `RUNNING` | 初始化成功且数据有效 | 超时、错误或校准请求 | 正常使用数据。 |
| `CALIBRATING` | 用户或上电触发校准 | 校准完成或失败 | 电机保持停止。 |
| `DATA_TIMEOUT` | 超过超时阈值无新数据 | 恢复连续有效样本 | 可短时保留旧值，但必须标记过期。 |
| `COMM_ERROR` | HAL I2C 错误或设备无响应 | recover 成功 | 不使用新数据，保留最后有效值用于诊断。 |
| `DATA_INVALID` | 数值越界、状态无效、跳变异常 | 连续有效样本恢复 | 不直接覆盖稳定值。 |
| `NEED_REINIT` | 连续错误超过阈值 | 重新初始化成功 | 上层降级，必要时停车。 |

### 11.2 是否允许继续使用旧数据

| 状态 | 是否允许使用旧数据 | 说明 |
|---|---|---|
| `RUNNING` | 是 | 正常使用最新数据。 |
| `DATA_INVALID` | 有条件 | 可保留上次稳定值，但 `valid=0` 或 `stale=1`。 |
| `DATA_TIMEOUT` | 短时有条件 | IMU 可短时用于显示，不能用于闭环；激光超时不应用于放行前进。 |
| `COMM_ERROR` | 否 | 仅可用于诊断显示。 |
| `CALIBRATING` | 否 | 校准期间控制层应停止或保持锁定。 |
| `NEED_REINIT` | 否 | 必须恢复后再使用。 |

## 12. 推荐 API 设计

### 12.1 JY61P API

| 函数名 | 功能 | 输入参数 | 输出参数 | 返回值 | 调用时机 | 是否阻塞 | HAL 依赖 |
|---|---|---|---|---|---|---|---|
| `jy61p_init` | 初始化 JY61P 句柄和内部状态 | 句柄指针、`I2C_HandleTypeDef *hi2c` | 无 | 模块状态码 | HAL I2C 初始化后 | 短阻塞 | `hi2c1` |
| `jy61p_update` | 周期读取寄存器并刷新姿态 | 句柄指针、`now_ms` | 内部缓存 | 模块状态码 | 10-20 ms | 短阻塞 | `hi2c1` |
| `jy61p_get_attitude` | 获取姿态快照 | 句柄指针 | `JY61P_Attitude_t *` | 是否成功 | 控制层读取 | 非阻塞 | 无 |
| `jy61p_get_motion` | 获取加速度和角速度 | 句柄指针 | `JY61P_Motion_t *` | 是否成功 | 控制层读取 | 非阻塞 | 无 |
| `jy61p_start_static_calibration` | 启动静止校准 | 句柄指针、采样次数 | 无 | 状态码 | 上电或用户命令 | 非阻塞启动 | 无 |
| `jy61p_calibration_update` | 执行校准状态机 | 句柄指针、`now_ms` | 内部校准参数 | 状态码 | 主循环 | 短阻塞 | `hi2c1` |
| `jy61p_zero_yaw_reference` | 设置软件 yaw 参考 | 句柄指针 | 无 | 状态码 | 任务段开始 | 非阻塞 | 无 |
| `jy61p_write_register_unlocked` | 写配置寄存器 | 寄存器、值 | 无 | 状态码 | 明确需要写配置时 | 短阻塞 | `hi2c1` |
| `jy61p_recover` | I2C 错误恢复 | 句柄指针 | 无 | 状态码 | 连续错误后 | 可能短阻塞 | `hi2c1`/GPIO |

### 12.2 MS53LM API

| 函数名 | 功能 | 输入参数 | 输出参数 | 返回值 | 调用时机 | 是否阻塞 | HAL 依赖  |
| --- | --- | --- | --- | ----- | --- | --- | --- |
| `ms53l1m_init` | 初始化激光/VL53L1X  | 句柄指针、`I2C_HandleTypeDef *hi2c` | 无 | 模块状态码 | HAL I2C 初始化后 | 中等阻塞 | `hi2c1` |
| `ms53l1m_update` | 轮询 ready 并读取距离 | 句柄指针、`now_ms` | 内部缓存 | 模块状态码 | 20 ms | ready 时短阻塞 | `hi2c1` |
| `ms53l1m_get_distance` | 获取距离快照 | 句柄指针 | `MS53L1M_Distance_t *` | 是否成功  | 控制层读取 | 非阻塞 | 无 |
| `ms53l1m_set_mode` | 设置短/中/长距离模式 | 句柄指针、模式 | 无 | 状态码 | 初始化或调参 | 短阻塞 | `hi2c1` |
| `ms53l1m_start_continuous` | 启动连续测量 | 句柄指针 | 无 | 状态码 | 初始化后 | 短阻塞 | `hi2c1` |
| `ms53l1m_stop` | 停止测量 | 句柄指针 | 无 | 状态码 | 低功耗或恢复前 | 短阻塞 | `hi2c1` |
| `ms53l1m_recover` | 停止并重启测量 | 句柄指针 | 无 | 状态码 | 连续错误后 | 中等阻塞 | `hi2c1` |

### 12.3 统一传感器管理 API

| 函数名 | 功能 | 输入参数 | 输出参数 | 返回值 | 调用时机 | 是否阻塞 |
|---|---|---|---|---|---|---|
| `sensor_init_all` | 初始化全部传感器 | `I2C_HandleTypeDef *hi2c` | 内部状态 | 状态码 | `main.c` 外设初始化后 | 阻塞 |
| `sensor_update_all` | 统一调度更新 | `now_ms` | 内部快照 | 状态码 | 主循环每轮 | 非长阻塞 |
| `sensor_get_snapshot` | 获取统一快照 | 无 | `SENSOR_SystemState_t *` | 是否成功 | 电机/遥测读取 | 非阻塞 |
| `sensor_request_imu_calibration` | 请求 IMU 校准 | 校准类型 | 无 | 状态码 | 用户命令 | 非阻塞 |
| `sensor_recover_all` | 尝试恢复错误模块 | 无 | 内部状态 | 状态码 | 错误状态 | 可能短阻塞 |

## 13. 推荐数据结构设计

### 13.1 JY61P 状态枚举

| 枚举名 | 含义 |
|---|---|
| `JY61P_STATE_UNINIT` | 未初始化。 |
| `JY61P_STATE_INITING` | 初始化中。 |
| `JY61P_STATE_RUNNING` | 正常运行。 |
| `JY61P_STATE_CALIBRATING` | 校准中。 |
| `JY61P_STATE_DATA_TIMEOUT` | 数据超时。 |
| `JY61P_STATE_COMM_ERROR` | I2C 通信错误。 |
| `JY61P_STATE_DATA_INVALID` | 数据无效。 |
| `JY61P_STATE_NEED_REINIT` | 需要重新初始化。 |

### 13.2 JY61P 姿态数据结构

| 字段 | 类型建议 | 单位 | 范围 | 中断更新 | `volatile` | 上层权限 |
|---|---|---|---|---|---|---|
| `roll_deg` | `float` | deg | 约 -180 到 180 | 否 | 否 | 只读 |
| `pitch_deg` | `float` | deg | 约 -90 到 90 | 否 | 否 | 只读 |
| `yaw_deg` | `float` | deg | 约 -180 到 180 | 否 | 否 | 只读 |
| `yaw_relative_deg` | `float` | deg | -180 到 180 | 否 | 否 | 只读 |
| `temperature_c` | `float` | ℃ | 传感器范围 | 否 | 否 | 只读 |
| `last_update_ms` | `uint32_t` | ms | tick | 否 | 否 | 只读 |
| `valid` | `uint8_t` | 无 | 0/1 | 否 | 否 | 只读 |

### 13.3 JY61P 原始数据结构

| 字段 | 类型建议 | 单位 | 说明 |
|---|---|---|---|
| `raw_ax/raw_ay/raw_az` | `int16_t` | LSB | 来自 `0x34-0x36`。 |
| `raw_gx/raw_gy/raw_gz` | `int16_t` | LSB | 来自 `0x37-0x39`。 |
| `raw_hx/raw_hy/raw_hz` | `int16_t` | LSB | 来自 `0x3A-0x3C`，可选。 |
| `raw_roll/raw_pitch/raw_yaw` | `int16_t` | LSB | 来自 `0x3D-0x3F`。 |
| `raw_temp` | `int16_t` | LSB | 来自 `0x40`。 |

### 13.4 JY61P 校准参数结构

| 字段 | 类型建议 | 单位 | 说明 |
|---|---|---|---|
| `gyro_bias_x_dps` | `float` | deg/s | 软件计算的 X 轴角速度零偏。 |
| `gyro_bias_y_dps` | `float` | deg/s | 软件计算的 Y 轴角速度零偏。 |
| `gyro_bias_z_dps` | `float` | deg/s | 软件计算的 Z 轴角速度零偏。 |
| `acc_bias_x_g` | `float` | g | 加速度偏置，初版可只记录不主动修正。 |
| `acc_bias_y_g` | `float` | g | 加速度偏置。 |
| `acc_bias_z_g` | `float` | g | 加速度偏置。 |
| `yaw_reference_deg` | `float` | deg | 相对航向参考。 |
| `sample_count` | `uint16_t` | 次 | 当前校准采样数。 |
| `is_calibrated` | `uint8_t` | 无 | 是否完成校准。 |
| `calib_time_ms` | `uint32_t` | ms | 校准完成时间。 |

### 13.5 MS53LM 距离数据结构

| 字段 | 类型建议 | 单位 | 范围 | 中断更新 | `volatile` | 上层权限 |
|---|---|---|---|---|---|---|
| `raw_distance_mm` | `uint16_t` | mm | 0-4000 | 否 | 否 | 只读 |
| `filtered_distance_mm` | `uint16_t` | mm | 0-4000 | 否 | 否 | 只读 |
| `range_status` | `uint8_t` | 无 | 传感器状态码 | 否 | 否 | 只读 |
| `valid` | `uint8_t` | 无 | 0/1 | 否 | 否 | 只读 |
| `too_close` | `uint8_t` | 无 | 0/1 | 否 | 否 | 只读 |
| `last_update_ms` | `uint32_t` | ms | tick | 否 | 否 | 只读 |
| `sample_count` | `uint32_t` | 次 | 递增 | 否 | 否 | 只读 |
| `error_count` | `uint32_t` | 次 | 递增 | 否 | 否 | 只读 |

### 13.6 MS53LM 滤波缓存结构

| 字段 | 类型建议 | 单位 | 说明 |
|---|---|---|---|
| `window_mm[MS53LM_FILTER_WINDOW]` | `uint16_t[]` | mm | 最近有效样本。 |
| `window_count` | `uint8_t` | 个 | 当前有效窗口数量。 |
| `write_index` | `uint8_t` | 下标 | 环形写入位置。 |
| `last_stable_mm` | `uint16_t` | mm | 上一次稳定输出。 |
| `suspect_count` | `uint8_t` | 次 | 连续可疑跳变次数。 |

### 13.7 统一传感器状态结构

| 字段 | 类型建议 | 说明 |
|---|---|---|
| `jy61p_state` | `JY61P_State_t` | IMU 状态。 |
| `ms53lm_state` | `MS53LM_State_t` | 激光状态。 |
| `imu_attitude` | `JY61P_Attitude_t` | 姿态快照。 |
| `imu_motion` | `JY61P_Motion_t` | 加速度/角速度快照。 |
| `front_distance` | `MS53LM_Distance_t` | 前方距离快照。 |
| `system_valid` | `uint8_t` | 传感器系统整体是否可用。 |
| `fault_flags` | `uint32_t` | 故障位。 |
| `last_update_ms` | `uint32_t` | 统一层最近更新时间。 |

## 14. 关键参数表

| 推荐宏名 | 默认值建议 | 单位 | 所属模块 | 是否需要实测调整 |
|---|---:|---|---|---|
| `JY61P_I2C_ADDR_7BIT` | `0x50` | 地址 | JY61P | 否，除非改地址。 |
| `JY61P_I2C_ADDR_8BIT` | `0xA0` | 地址 | JY61P | 否。 |
| `JY61P_I2C_TIMEOUT_MS` | 10 | ms | JY61P | 是。 |
| `JY61P_UPDATE_PERIOD_MS` | 10 或 20 | ms | JY61P | 是。 |
| `JY61P_DATA_TIMEOUT_MS` | 100 | ms | JY61P | 是。 |
| `JY61P_STATIC_CALIB_SAMPLES` | 200 | 次 | JY61P | 是。 |
| `JY61P_STATIC_GYRO_THRESHOLD_DPS` | 1.0 | deg/s | JY61P | 是。 |
| `JY61P_ACC_NORM_TOLERANCE_G` | 0.15 | g | JY61P | 是。 |
| `JY61P_FILTER_ALPHA` | 0.3 | 无 | JY61P | 是。 |
| `MS53LM_I2C_ADDR_7BIT` | `0x29` | 地址 | MS53LM | 否，除非改地址。 |
| `MS53LM_I2C_ADDR_8BIT` | `0x52` | 地址 | MS53LM | 否。 |
| `MS53LM_ID_REG` | `0x010F` | 寄存器 | MS53LM | 否。 |
| `MS53LM_ID_EXPECTED` | `0xEACC` | ID | MS53LM | 待确认实物。 |
| `MS53LM_TIMING_BUDGET_US` | 140000 | us | MS53LM | 是。 |
| `MS53LM_INTER_MEASURE_MS` | 150 | ms | MS53LM | 是。 |
| `MS53LM_READY_POLL_MS` | 20 | ms | MS53LM | 是。 |
| `MS53LM_VALID_MIN_MM` | 40 | mm | MS53LM | 否。 |
| `MS53LM_VALID_MAX_MM` | 3900 | mm | MS53LM | 是。 |
| `MS53LM_FILTER_WINDOW` | 5 | 样本 | MS53LM | 是。 |
| `MS53LM_JUMP_REJECT_MM` | 400 | mm | MS53LM | 是。 |
| `MS53LM_DATA_TIMEOUT_MS` | 500 | ms | MS53LM | 是。 |
| `SENSOR_FRONT_WARN_MM` | 300-500 | mm | 统一层 | 必须实车调整。 |
| `SENSOR_FRONT_STOP_MM` | 100-200 | mm | 统一层 | 必须实车调整。 |

## 15. 文件组织建议

推荐目录结构：

```text
Core/
  Inc/
    jy61p.h
    atk_ms53lm.h
    sensors.h
  Src/
    jy61p.c
    atk_ms53lm.c
    sensors.c
Drivers/
  VL53L1X/
    core/
    platform/
```

若继承现有 ATK 框架文件名 `atk_ms53l1m.h/.c`，可以保持该名称，但必须全工程一致，不要同时存在 `atk_ms53lm` 和 `atk_ms53l1m` 两套 API。

### 15.1 CubeIDE 生成代码注意事项

| 项目 | 要求 |
|---|---|
| `main.c` | 用户调用代码必须放在 `USER CODE BEGIN` / `USER CODE END` 区域。 |
| `i2c.c` | CubeMX 生成 I2C1 初始化，PB6/PB7，不应手动写在用户驱动里。 |
| 新增驱动文件 | `jy61p.c/h`、`atk_ms53lm.c/h`、`sensors.c/h` 不应被 CubeMX 覆盖。 |
| Include Path | 若使用 VL53L1X API，需要把 `Drivers/VL53L1X/core/inc` 和 `Drivers/VL53L1X/platform/inc` 加入 include path。 |

### 15.2 main.c 调用流程

```text
HAL_Init
SystemClock_Config
MX_GPIO_Init
MX_I2C1_Init
sensor_init_all(&hi2c1)

while (1)
{
    sensor_update_all(HAL_GetTick())
    motor_control_update()
    telemetry_update()
}
```

注意：以上是伪流程，不是 `.c` 实现代码。

## 16. 验收标准

| 层面 | 验收标准 |
|---|---|
| 编译层面 | 工程无编译错误；无重复符号；无未声明 HAL 句柄；新增文件被 CubeIDE 正确编译。 |
| 初始化层面 | 上电 2 秒内 JY61P 与 MS53LM 均进入 `RUNNING` 或明确错误状态；错误计数可见。 |
| JY61P 数据读取 | 静止时 Roll/Pitch/Yaw 持续刷新，`last_update_ms` 间隔 10-20 ms；角速度接近 0；加速度模长接近 1g。 |
| JY61P 校准 | 静止校准期间电机不允许运动；校准后静止 60 秒 yaw 漂移建议先验收 `< 3 deg/min`，再按实测收紧。 |
| JY61P 异常处理 | 断开 JY61P 后，系统在 100 ms 级别进入超时或通信错误状态，主循环不死锁。 |
| ATK-MS53LM 测距 | 在 100、300、500、1000 mm 固定障碍测试中，filtered 距离稳定刷新；RangeStatus 有效时才更新稳定值。 |
| ATK-MS53LM 异常处理 | 激光断开或遮挡异常时，状态进入 `DATA_TIMEOUT` 或 `DATA_INVALID`，不使用错误距离覆盖稳定值。 |
| 连续运行稳定性 | 两传感器同时运行 30 分钟，无 I2C 总线卡死；错误计数无持续快速增长。 |
| 与电机控制接口 | 电机控制只能读取传感器快照，不直接访问底层 I2C；前方距离低于停车阈值时安全状态可覆盖速度为 0。 |

## 17. 测试步骤

| 测试 | 测试目的 | 操作方法 | 预期现象 | 失败时检查 |
|---|---|---|---|---|
| JY61P 单独测试 | 验证 IMU I2C 通信和数据转换 | 只接 JY61P，上电读取姿态 | 数据按周期刷新，静止角速度接近 0 | 地址、SCL/SDA、供电、上拉、IIC 模式。 |
| JY61P 静止测试 | 验证零偏和噪声 | 小车静止放置 1-5 分钟 | Roll/Pitch 基本稳定，yaw 漂移可量化 | 震动、供电、校准流程、安装松动。 |
| JY61P 姿态变化测试 | 验证坐标方向 | 手动俯仰、横滚、旋转模块 | Pitch/Roll/Yaw 方向和变化合理 | 坐标系映射、安装方向、符号定义。 |
| JY61P 校准测试 | 验证上电静止校准 | 小车静止执行校准 | 状态从 `CALIBRATING` 到 `RUNNING` | 静止阈值、采样次数、电机是否锁死。 |
| ATK-MS53LM 单独测试 | 验证激光 I2C 通信 | 只接激光，放置固定障碍 | 距离 mm 稳定，状态 valid | I2C 地址、ID、IIC 模式、VL53L1X 驱动。 |
| 距离变化测试 | 验证滤波和响应 | 将障碍从 100 mm 移到 1000 mm | raw 快速变化，filtered 平滑变化 | 滤波窗口、跳变阈值、反射材质。 |
| 双传感器同时运行 | 验证 I2C 共总线 | 两者同挂 I2C1，连续运行 | 更新周期互不阻塞 | I2C 总线冲突、超时过长、上拉电阻。 |
| 小车移动测试 | 验证实车动态数据 | 低速直行和转向 | yaw 可用于纠偏，距离可触发减速 | 震动滤波、坐标系、电机干扰。 |
| 前方障碍测试 | 验证避障接口 | 小车低速靠近障碍 | 预警距离限速，停车距离停车 | 阈值、安装位置、滤波延迟。 |
| 通信异常测试 | 验证错误处理 | 短时断开传感器或拔线 | 状态进入错误/超时，主循环继续 | 错误恢复、超时阈值、bus recovery。 |
| 长时间运行测试 | 验证稳定性 | 连续运行 30-60 分钟 | 无死锁，错误计数可诊断 | I2C 卡死、内存越界、tick 溢出处理。 |

## 18. 未验证风险

| 风险 | 影响 | 建议处理方式 |
| --- | --- | --- |
| PB6/PB7 上拉电压不确定 | 若上拉到 5V，可能损坏或影响 STM32 I2C | 必须万用表/示波器确认；必要时改 3.3V 上拉或加电平转换。 |
| HAL 库版本未确认 | API 和工程配置可能有差异 | 后续实现前固定 STM32CubeF1 版本，并记录在 README。 |
| 是否使用 RTOS/DMA 未确认 | 调度和数据保护方式不同 | 初版按裸机轮询；后续再迁移任务或 DMA。 |
| 电机控制接口未定义 | 传感器到控制的字段可能对接不顺 | 传感器层只提供快照，不耦合电机实现。 |
| IMU 坐标系与车体坐标系未标定 | 姿态方向可能反，导致纠偏错误 | 安装后做方向标定表，必要时在 `sensors` 层做轴映射。 |
| 实车震动影响姿态稳定性 | 角速度和加速度噪声增加，yaw 漂移加剧 | 实测调整 JY61P 滤波、静止阈值、校准策略。 |
| 单点激光视场有限 | 只能检测正前方小区域，可能漏检侧向障碍 | 只作为前向辅助；结合视觉或多方向传感器。 |
| I2C 共总线卡死 | 一个设备异常可能影响另一个设备 | 加短超时、错误计数、bus recovery 和重新初始化策略。 |

## 19. 后续代码实现注意事项

1. 后续模型必须先确认最终工程路径，再创建或修改 `Core/Inc`、`Core/Src` 文件。
2. 不要在驱动中重复初始化 I2C1，只接收 `hi2c1` 指针。
3. 不要在传感器层直接控制电机。
4. 所有对上层输出的数据必须带 `valid` 和 `last_update_ms`。
5. 所有未确认参数必须保留宏定义，方便实测后修改。
6. 对 JY61P 内部寄存器写操作必须经过解锁、写目标、保存三个步骤，且默认不要自动写内部参数。
7. 对 MS53LM 距离数据，只有状态有效且范围合理时才更新稳定距离。
8. 初版优先保证稳定可调试，再考虑 I2C DMA 或 RTOS。
