Chemcrin/IntelligentTransformCart/代码/VibeCoding/提示词.docx

你现在是一位优秀的嵌入式开发者，精通stm32和C语言编程。 现在需要你接手一个智能物流搬运小车的项目，并且将项目拆解为多个模块，你需要负责两个传感器的姿态解算模块，需要完成代码编写，分别是陀螺仪JY61P和激光传感器ATK-MS53LM，编写二者的.c\.h文件。开发工具是stm32cubeIDE（HAL库），主控芯片是stm32C8T6

本轮对话不需要你生成代码，只需要给我生成一个详细的代码架构文件。

接下来我将详细描述这两个传感器的细节要求:见md文档中的陀螺仪与传感器部分

两个传感器的资料见PDF，这是官方的示例。引脚使用见嘉立创原理图截图

现在我需要你先完成文档的理解，建立合理的工作计划，逐个完成任务。验收的要求是：生成一份逻辑清晰，细节完善的代码架构文档，保证另一个低成本模型阅读后可以直接完成无误代码的填充任务。代码框架包含传感器连接引脚的位置（i2c1，pb6、pb7引脚）；后期电机与陀螺仪、激光传感器的配合方式；为一些重要参数设定变量名，保证导入工程后代码不出变量冲突的问题；包含陀螺仪激光传感器初始化设定，校准方式（能消除陀螺仪累计误差）；初始化启动后两个传感器如何保持持续测量，并且不断回传更新姿态位置数值，保证小车能实时读取地形距离、姿态，偏航角，俯仰，加速度等重要数值信息；激光传感器位于车头，在只有一个激光传感器的情况下保证数据读取的稳定性。

- 另外，在工程开始前，在md文档之外的对话框里，向我反馈这些内容：
- 我是否说明了最终目标，而不是只描述了一个模糊愿望？
- 我是否提供了当前工程状态、文件路径、代码或日志？
- 我是否写清了硬件、工具链、库版本和外设连接？
- 我是否说明了本轮允许修改和禁止修改的范围？
- 我是否定义了可观察、可测试的验收标准？
- 我是否说明了旧功能中哪些必须回归验证？
- 我是否要求输出测试步骤和未验证风险？
- 如果是改进需求，我是否同步修改了验收标准？

你现在是一位资深嵌入式开发工程师，精通 STM32、HAL 库、C 语言、步进电机控制、PID 控制、传感器融合和麦克纳姆轮全向运动控制。

## 一、项目背景

你需要接手一个“智能物流搬运小车”项目，当前负责其中的“小车移动系统”。

项目已有硬件与软件基础如下：

- 开发工具：STM32CubeIDE

- 库：STM32 HAL 库

- 主控芯片：STM32F103C8T6

- 工程路径：`D:\STM32CubeIDE\workspace_1.19.0\ATK-YJ`

- 已接入传感器：

- 陀螺仪：JY61P

- 激光测距传感器：ATK-MS53LM

- JY61P 与 ATK-MS53LM 的 `.c/.h` 文件已经写好，不需要重新设计底层驱动

- 项目中另有文档：`传感器数值函数与读取.md`

- 该文档记录了传感器读取函数、变量名和数据含义

- 后续架构设计必须适配该文档中的函数名和变量名

- 不允许设计会与现有变量冲突的新变量名

## 二、本轮任务目标

本轮对话 **不需要生成代码**。

你的任务是：

1. 阅读并理解我提供的 ZDT-X42-V2 步进电机开发文档。

2. 梳理 ZDT-X42-V2 步进电机的控制方式、关键函数、通信逻辑和运行模式。

3. 基于智能物流搬运小车的移动需求，设计一份完整的**代码逻辑架构文档**。

4. 文档需要让另一个低成本模型阅读后，可以直接、稳定、无歧义地完成代码填充。

5. 架构必须覆盖：

- 电机控制模块

- 麦克纳姆轮运动控制模块

- JY61P 陀螺仪参与方向修正的方式

- ATK-MS53LM 激光测距参与避障、停车或距离控制的方式

- PID 调参逻辑和参数规划

- 与现有传感器变量名、函数名的适配方式

## 三、工程开始前必须先反馈

在正式输出架构文档之前，请先在对话框中单独反馈以下检查结果，不要写进最终 md 文档里：

1. 我是否说明了最终目标，而不是只描述了一个模糊愿望？

2. 我是否提供了当前工程状态、文件路径、代码或日志？

3. 我是否写清了硬件、工具链、库版本和外设连接？

4. 我是否说明了本轮允许修改和禁止修改的范围？

5. 我是否定义了可观察、可测试的验收标准？

6. 我是否说明了旧功能中哪些必须回归验证？

7. 我是否要求输出测试步骤和未验证风险？

8. 如果这是改进需求，我是否同步修改了验收标准？

请逐条评价，并指出缺失信息。

如果某些信息缺失，请不要停止任务，而是在后续架构中做出明确假设，并将假设写入“前置假设与待确认项”。

## 四、输入资料

我将提供以下资料，你需要优先阅读并提取有效信息：

1. ZDT-X42-V2 步进电机开发与编程细节文档

2. `传感器数值函数与读取.md`

3. 如有必要，我会补充 ZDT 官方麦轮万向运动例程中的关键片段

关于 ZDT 官方麦轮例程：

- 如果当前 ZDT 文档已经足够说明控制协议、速度模式、位置模式、同步控制和电机方向配置，则不需要完整例程。

- 如果文档不足以确认麦轮四电机控制逻辑，请要求我只提供核心片段，而不是一次性发送完整大文件。

- 优先请求以下片段：

- 电机初始化

- 速度控制函数

- 位置控制函数

- 同步启动函数

- 停止/急停函数

- 麦轮前进、后退、左移、右移、旋转示例

- CAN/UART/RS485 协议帧格式，视项目实际通信方式而定

## 五、禁止事项

本轮禁止：

- 不要直接生成 `.c` 或 `.h` 代码

- 不要修改工程文件

- 不要虚构已经存在的函数名、变量名、宏定义或文件名

- 不要重写 JY61P 和 ATK-MS53LM 的底层驱动

- 不要忽略 `传感器数值函数与读取.md` 中已有的变量名

- 不要把架构写成泛泛的理论说明

- 不要只写“前进、后退、左转、右转”，必须细化到四个麦轮电机的方向、速度符号和控制关系

## 六、最终输出要求

请生成一份 Markdown 格式的代码架构文档，建议命名为：

`智能物流小车移动系统代码架构设计.md`

文档必须包含以下章节：

### 1. 项目目标与控制对象

说明小车移动系统要实现的目标，包括：

- 前进

- 后退

- 左平移

- 右平移

- 左前斜行

- 右前斜行

- 左后斜行

- 右后斜行

- 原地左旋

- 原地右旋

- 指定角度转向

- 指定距离前进/后退

- 基于激光传感器的停车或限距

- 基于陀螺仪的航向保持

### 2. 现有工程资源梳理

根据我提供的文档，整理：

- 已有文件

- 已有函数

- 已有全局变量

- 已有宏定义

- 传感器数据读取方式

- 不应重复定义的变量名

- 后续代码应新增的模块文件建议

### 3. ZDT-X42-V2 电机控制抽象层设计

规划电机基础控制接口，但不写具体代码。

至少包括：

- 电机编号定义

- 四个电机在小车上的安装位置

- 电机正反方向约定

- 速度模式

- 位置模式

- 停止模式

- 急停模式

- 同步启动模式

- 电机使能/失能

- 速度单位、角度单位、脉冲单位之间的关系

- 需要从 ZDT 文档确认的参数

请给出建议函数名、参数含义和返回值含义。

### 4. 麦克纳姆轮运动学规划

详细说明四轮速度分配关系。

至少覆盖：

- 前进

- 后退

- 左平移

- 右平移

- 左前斜行

- 右前斜行

- 左后斜行

- 右后斜行

- 原地左旋

- 原地右旋

- 任意方向矢量运动

- 平移 + 自转叠加控制

需要明确四个轮子的速度符号关系，例如：

- Front_Left

- Front_Right

- Rear_Left

- Rear_Right

如果电机安装方向会影响符号，请将方向修正参数单独设计为变量，不要硬编码在运动函数里。

### 5. 移动控制函数规划

设计上层运动函数，不写具体实现代码。

至少包含：

- `Move_Forward`

- `Move_Backward`

- `Move_Left`

- `Move_Right`

- `Move_Stop`

- `Move_Rotate_Left`

- `Move_Rotate_Right`

- `Move_Set_Vector`

- `Move_Set_Vx_Vy_Wz`

- `Move_Forward_With_YawHold`

- `Move_Distance_With_LaserLimit`

- `Move_To_TargetYaw`

每个函数需要说明：

- 功能

- 输入参数

- 内部调用关系

- 使用哪些传感器数据

- 是否使用 PID

- 退出条件

- 异常处理方式

### 6. JY61P 陀螺仪配合方式

结合 `传感器数值函数与读取.md` 中已有的变量名，规划：

- 航向角 yaw 的读取方式

- yaw 零点校准方式

- 航向保持控制

- 指定角度转向控制

- 角速度辅助判断

- 陀螺仪数据异常处理

- PID 输出如何转化为四轮差速修正

### 7. ATK-MS53LM 激光传感器配合方式

结合 `传感器数值函数与读取.md` 中已有的变量名，规划：

- 距离值读取方式

- 距离阈值变量

- 前方障碍停车逻辑

- 指定距离靠近目标逻辑

- 低速接近逻辑

- 距离异常值过滤

- 激光传感器失效时的安全策略

### 8. PID 控制规划

分别规划：

- 航向保持 PID

- 指定角度转向 PID

- 距离控制 PID

- 速度平滑控制

- PID 参数变量名

- 输出限幅

- 积分限幅

- 死区处理

- 调参步骤

要求说明每个 PID 的：

- 输入

- 目标值

- 当前值

- 误差计算方式

- 输出含义

- 输出如何作用到电机速度

- 推荐初始参数范围

- 调参顺序

### 9. 参数与变量命名规范

设计重要参数变量名，必须避免和已有传感器变量冲突。

至少包括：

- 四电机 ID

- 四电机方向修正系数

- 默认速度

- 最大速度

- 最小启动速度

- 加速度

- yaw 目标值

- yaw 当前值引用方式

- 激光距离阈值

- PID 参数结构体

- 运动状态枚举

- 错误状态枚举

如果变量需要适配 `传感器数值函数与读取.md`，请明确写出“直接使用已有变量”还是“新增封装变量”。

### 10. 模块文件规划

规划建议新增或调整的文件，例如：

- `motor_zdt.h`

- `motor_zdt.c`

- `mecanum_chassis.h`

- `mecanum_chassis.c`

- `chassis_pid.h`

- `chassis_pid.c`

- `chassis_config.h`

- `chassis_task.h`

- `chassis_task.c`

每个文件需要说明：

- 职责

- 依赖关系

- 对外接口

- 不应包含的内容

### 11. 主循环或任务调度逻辑

说明在 `main.c` 或任务函数中如何组织：

- 传感器更新

- 控制目标更新

- PID 计算

- 电机输出刷新

- 安全检查

- 状态机切换

需要给出清晰的执行顺序。

### 12. 状态机设计

设计小车移动系统状态机，至少包含：

- 空闲

- 初始化

- 手动速度控制

- 航向保持运动

- 指定距离运动

- 指定角度旋转

- 避障停车

- 错误状态

- 急停状态

说明每个状态的进入条件、退出条件和执行动作。

### 13. 测试与验收步骤

必须输出可执行的测试步骤，包括：

- 单电机方向测试

- 四电机编号测试

- 麦轮方向组合测试

- 前进直线性测试

- 横移偏航测试

- 原地旋转角度测试

- 激光限距停车测试

- 陀螺仪航向保持测试

- PID 调参测试

- 异常断连或传感器异常测试

每项测试需要说明：

- 操作步骤

- 预期现象

- 通过标准

- 如果失败，优先检查哪些参数

### 14. 回归验证要求

说明旧功能需要回归验证的内容，包括：

- JY61P 数据读取是否正常

- ATK-MS53LM 数据读取是否正常

- 串口/I2C/CAN/定时器等外设是否仍正常

- 原有 main 循环是否被破坏

- 原有中断回调是否被覆盖

- 编译是否无重复定义、无隐式声明、无链接错误

### 15. 未验证风险与待确认项

列出所有无法从当前资料确认的信息，例如：

- ZDT-X42-V2 实际通信方式

- 四个电机 ID

- 电机安装方向

- 麦轮安装姿态

- 轮径

- 轮距

- 轴距

- 减速比

- 速度单位

- 脉冲与距离换算关系

- 传感器刷新频率

- 外设资源占用情况

不要隐藏这些风险，必须明确列出。

## 七、输出风格要求

- 文档必须结构清晰

- 语言必须适合低成本模型继续执行

- 每个模块都要说明“为什么存在”和“如何被调用”

- 函数规划要接近真实 C 工程接口

- 不写完整代码，但可以写函数原型级别的接口规划

- 对不确定的信息必须标记为“待确认”

- 不允许用空泛描述代替工程细节

你现在是一位优秀的嵌入式开发者，精通stm32和C语言编程。 现在需要你接手一个智能物流搬运小车的项目。在此之前，小车已经增加了两个传感器，分别是陀螺仪JY61P和激光传感器ATK-MS53LM，二者的.c\.h文件均已写好，详见IDE工作区D:\STM32CubeIDE\workspace_1.19.0\ATK-YJ。开发工具是stm32cubeIDE（HAL库），主控芯片是stm32C8T6

我需要你现在阅读检查这份陀螺仪与激光传感器有关的工程代码，并且确定以下内容：两个传感器是否都已经处于i2c1上；是否已经正确分配从机地址，可以正常读取回传数据；陀螺仪是否有矫正累计误差值的办法；如何在调试时获取回传的数据

你是一位资深嵌入式开发工程师，精通 STM32、STM32CubeIDE、HAL 库、I2C 通信和 C 语言工程代码分析。

## 项目背景

我现在接手一个智能物流搬运小车项目。

项目已经新增两个传感器：

1. 陀螺仪 / 姿态传感器：JY61P

2. 激光测距传感器：ATK-MS53LM

这两个传感器的 `.c` / `.h` 驱动文件已经写好。

开发环境：

- IDE：STM32CubeIDE

- HAL 库工程

- 主控芯片：STM32F103C8T6 / STM32C8T6

- 工程路径：`D:\STM32CubeIDE\workspace_1.19.0\ATK-YJ`

## 你的任务

请只阅读和分析工程代码，不要直接修改工程文件。

重点检查与 JY61P 和 ATK-MS53LM 两个传感器相关的代码，包括但不限于：

- `Core/Src`

- `Core/Inc`

- `.ioc` 配置文件

- I2C 初始化代码

- 传感器驱动 `.c` / `.h`

- `main.c`

- 调试输出相关代码，如 UART

## 需要确认的问题

请逐项检查并给出明确结论：

### 1. 两个传感器是否都挂载在 I2C1 上

请确认：

- JY61P 是否使用 `hi2c1`

- ATK-MS53LM 是否使用 `hi2c1`

- 是否存在使用 `I2C2`、软件 I2C、UART 或其他接口的情况

- `.ioc` 和实际代码是否一致

- 数据返回有没有使用重定向（并不需要，但是在之前的工程中疑似加入了

### 2. I2C 从机地址是否正确

请检查两个传感器驱动中的 I2C 地址定义和使用方式。

重点确认：

- 传感器的 7-bit 地址是多少

- HAL 函数中传入的地址是否已经左移 1 位

- 是否存在地址重复、地址写错、重复左移或漏左移的问题

- 是否调用了正确的 HAL I2C 读写函数，例如：

- `HAL_I2C_Master_Transmit`

- `HAL_I2C_Master_Receive`

- `HAL_I2C_Mem_Read`

- `HAL_I2C_Mem_Write`

### 3. 是否可以正常读取回传数据

请检查：

- 初始化流程是否调用了两个传感器的初始化函数

- 主循环或任务中是否调用了数据读取函数

- 读取函数是否检查 HAL 返回值

- 是否有超时、错误处理或重试机制

- 读取到的数据是否经过正确解析、单位换算或结构体保存

- 当前代码是否已经具备“可正常读取数据”的条件

如果无法确定硬件是否正常，请明确说明“代码层面看起来是否具备读取条件”，不要假设硬件连接一定正确。

### 4. 陀螺仪是否有校正累计误差的办法

请检查 JY61P 相关代码中是否存在：

- 零偏校准

- 上电静止校准

- 角度归零

- Z 轴航向角清零

- 累计误差补偿

- 写寄存器进行校准的函数

- 手动设置 yaw / pitch / roll 初值的逻辑

请说明：

- 当前代码是否已有校准接口

- 如果有，函数名是什么、在哪里调用、如何使用

- 如果没有，应在什么位置增加校准逻辑

- 调试或运行时应如何触发校准，例如按键、串口命令、上电延时静止校准等

### 5. 调试时如何获取传感器回传数据

请检查工程中已有的调试方式：

- 是否启用了 UART

- 是否通过串口打印传感器数据

- 是否可以通过 STM32CubeIDE Debug 观察变量

- 是否可以通过 Live Expressions / Watch 查看结构体数据

请给出具体建议：

- 推荐使用哪个串口

- 波特率是多少

- 应该在哪些函数或主循环位置添加打印

- 建议打印哪些关键数据

- 推荐的调试输出格式示例

## 输出要求

请将最终检查结果整理成一份 Markdown 文档。
