Chemcrin/IntelligentTransformCart/代码/VibeCoding/麦轮框架项目设计资料包/电机prompt.docx

你是一名资深嵌入式系统工程师，精通 STM32、C 语言以及基于麦克纳姆轮的全向移动机器人运动控制。现在你需要接手一个智能物流搬运小车的移动系统开发项目，并输出一份 **《麦轮运动控制系统技术设计文档》（MD 格式）**。文档将作为后续代码实现和团队协作的依据，因此必须逻辑清晰、细节完整，但不要求直接写出完整的 C 代码。

## 一、项目背景与已有资源

- **硬件平台**：STM32C8T6，基于 STM32CubeIDE（HAL 库）开发。

- **已有传感器**：

- 陀螺仪 JY61P（姿态 / 航向角）

- 激光传感器 ATK-MS53LM（距离 / 环境感知）

二者的 `.c/.h` 文件已就绪，位于工作区 `D:\STM32CubeIDE\workspace_1.19.0\ATK-YJ`。

- **执行器**：四个 ZDT-X42-V2 闭环步进电机，通过麦克纳姆轮呈 X 形布局。

- **通信方式**：

- 核心板 PA9（TX）、PA10（RX）配置为 UART1，通过 RS485 模块连接四个电机的驱动器。

- 驱动器端子对应关系：`R/A/H` → RS485 A 线，`T/B/L` → RS485 B 线（或根据驱动器手册)。

- 所有电机共用一条 RS485 总线，采用 **Modbus-RTU 协议**，通信参数 `115200波特率`。

- **控制模式**：不使用 PWM，完全通过 Modbus 寄存器读写实现速度给定与反馈。

- **电机资料及参考例程**：

- 说明书路径：`C:\Users\CloudyRain\Desktop\待办\个性化-物流小车\项目资料包\【3】步进电机\ZDT闭环步进资料\ZDT_X42_V2闭环步进资料\说明书`

- 官方 STM32F1 例程路径：`...\串口_RS232_RS485通讯控制`（建议从中提取初始化、CRC 校验、帧收发等基础代码片段）。

- **机械参数**（麦克纳姆轮 X 形布局）：

| 参数 | 值 | 来源 |

| 麦克纳姆轮直径 | 75 mm | 用户提供 |

| 单轮厚度 | 33 mm | 用户提供 |

| 轮距（左右麦轮外表面中心间距） | 320 mm | 用户测量 |

| 轴距（前后麦轮中心间距） | 220 mm | 用户测量 |

## 二、文档需要完成的核心分析与设计任务

请以**问题驱动**的方式组织文档，依次深入探讨并给出明确的技术方案或推导过程，必要时可用公式、伪代码、流程框图来描述。

### 1. 多电机 RS485 总线通信与寻址

- 分析 Modbus-RTU 协议如何在单总线上区分四个电机：是通过修改每个电机驱动器的**从机地址**（类似 I²C 设备地址）实现，还是有其他方式？请说明地址设置方法或默认地址区间。

- 详细描述**向单个电机发送速度指令**的数据帧结构（从机地址、功能码、寄存器地址、数据、CRC），以及如何在一帧内完成“多电机同步速度更新”（如广播指令或连续单播循环）。

- 给出**发送速度指令的软件流程**（例如：组装帧 → RS485 发送使能 → 发送 → 等待发送完成 → 取消发送使能），并强调如何处理 RS485 半双工的收发切换时序。

### 2. 电机实时转速反馈与闭环控制

- 说明如何通过 Modbus 协议**读取单个电机的实时转速**（相应寄存器地址、数据类型、换算关系），以及采用何种轮询或并行读取策略来同步获得四个电机的当前转速，同时避免总线冲突。

- 设计**转速闭环负反馈控制策略**：既然不使用 PWM，而电机自身具备位置/速度闭环（闭环步进），请分析主控侧是否需要再做速度 PID？如果需要，解释原因（例如克服打滑、提高响应带宽），并给出速度环控制框图：期望转速计算 → PID 调节 → Modbus 速度指令写入 → 电机实际转速回读 → 作为反馈量。

- 明确 PID 的**控制周期**如何选择，以及如何处理回读速度的滤波与异常值。

### 3. 麦克纳姆轮运动学模型与速度分解

- 建立 X 形布局的麦克纳姆轮逆运动学方程：根据期望的小车中心速度 `(v_x, v_y, ω)`，推导四个轮子的目标线速度 `(v_1, v_2, v_3, v_4)`，并转换成电机的目标转速（RPM 或 rps）。请写出含有轮距、轴距、轮径的完整公式，并明确各轮的正方向定义（建议绘制坐标系与轮序号示意图）。

- 给出在代码中实现逆运动学计算的**函数原型和伪代码**，包括输入为全局速度矢量，输出为四轮目标转速数组，以及如果某个轮速超限时的等比缩放处理逻辑。

### 4. 传感器融合与航向稳定控制

- **利用陀螺仪 JY61P**：设计基于航向角的**角度闭环控制**或**角速度阻尼控制**，使小车在直线行驶或转向时能自动修正航向偏差。阐述如何将陀螺仪的航向角与运动学模型结合，形成“期望运动指令 + 航向修正量 → 最终电机速度指令”的级联控制架构。可讨论 P 控制或串级 PID。

- **利用激光传感器 ATK-MS53L1M**：分析如何通过测距数据辅助定位（例如沿墙走、点到点距离校准、环境特征匹配），并与里程计（由电机速度积分得到）融合提升位置估计精度。不要求实现 SLAM，但需给出简单的**距离/位置修正逻辑**（如到目标距离缩短时减速、突然的测距变化作为位置重置线索）。

- 综合说明：如何协调两种传感器数据，最终在“保持面向目标方向”这一核心需求上实现稳健的移动控制，并指出可能的状态机流程（初始化对准 → 目标方向计算 → 实时偏差纠正 → 到达判定）。

### 5. 文档整合与可实施性要求

- 在文档最后，提供一个**总结性的控制流程总图**（文字描述或 Mermaid 流程图均可），覆盖从高层指令（如前进给定距离、旋转指定角度）到底层 Modbus 发送的全过程。

- 明确列出**所有需要调用的 HAL 外设**（UART1、TIM 用于控制周期、GPIO 用于 RS485 方向切换）及其配置要点。

- 给出进一步细化的建议：如优先级划分（控制周期中断 vs. Modbus 接收中断）、电机同步启动/停止机制等。

## 三、输出规范

- 请生成一份完整的 **Markdown** 文档，层次分明，可包含代码块（仅用于伪代码、寄存器表格、帧结构示例），但不输出可编译的完整 C 源码。

- 文档命名建议：`麦轮运动控制系统设计文档.md`。

- 所有路径、参数、引脚必须与上文提供的信息保持一致，无随意捏造。

现在，请开始按上述要求逐步分析并撰写出这份技术设计文档。
