Chemcrin/IntelligentTransformCart/PCB/电路板抄板问题.docx

1. 这块板子为什么设计了3个降压模块（TPS5450降压模块）他们分别给谁供电
2. 这块板子上有几个体积比较大的电容，我能不能用0603或0805的贴片电容来替代他们
3. 这块板子是几层的
4. 这块电路板的电源由谁提供，是板子上的dc口还是褐黄色的端子
5. 陀螺仪区的禁止铺铜是通过什么快捷键实现的，还有，禁止铺铜区的右下角有两根sda线贴的比较近，是否会有影响
