Chemcrin/IntelligentTransformCart/建模资料/pi外壳/fan 3030.SLDPRT

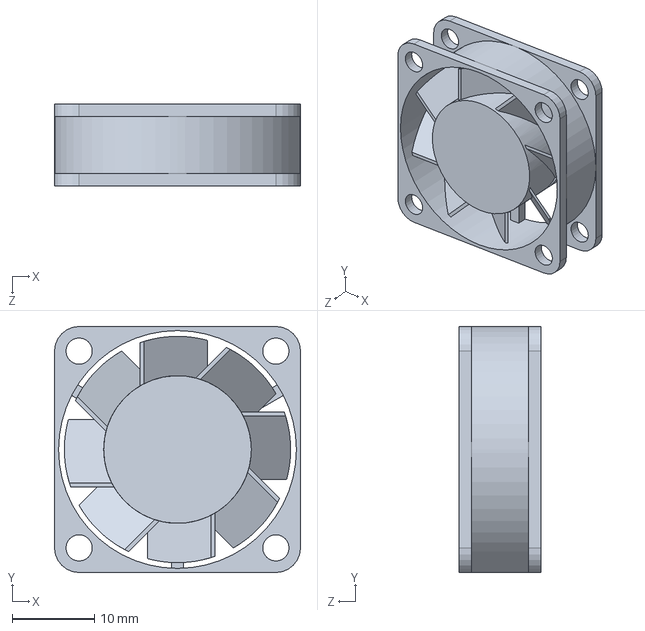
[picture p11: CAD file, 2026-07-06]
建模资料/pi外壳/fan 3030.SLDPRT
30.0 x 30.0 x 10.0 mm
