Chemcrin/IntelligentTransformCart/建模资料/小车装配体/底板一层V4.SLDPRT

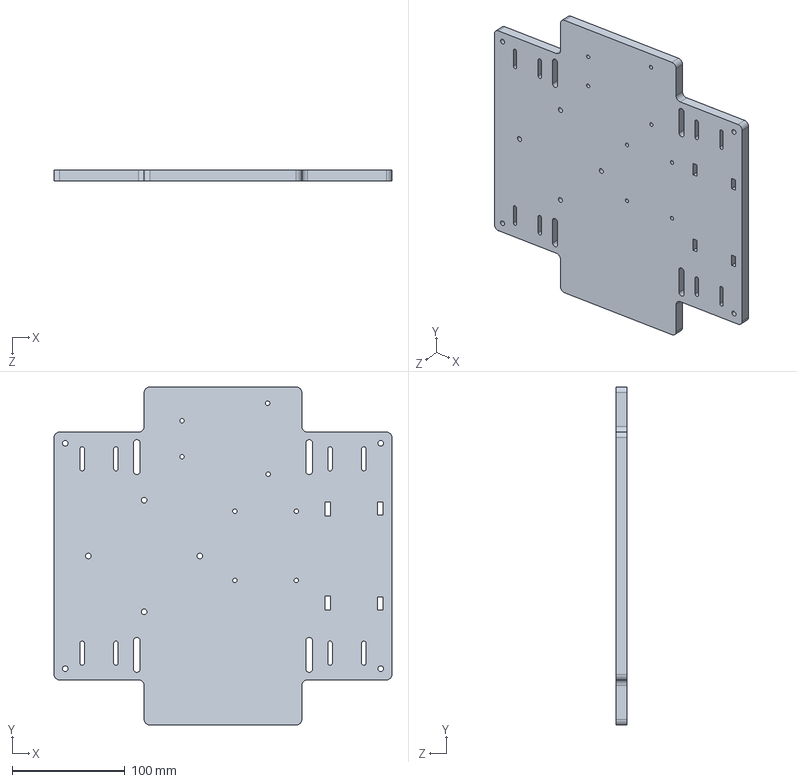
[picture p12: CAD file, 2026-07-06]
建模资料/小车装配体/底板一层V4.SLDPRT
300.0 x 300.0 x 10.0 mm
