Chemcrin/IntelligentTransformCart/建模资料/小车装配体/铜柱.SLDPRT

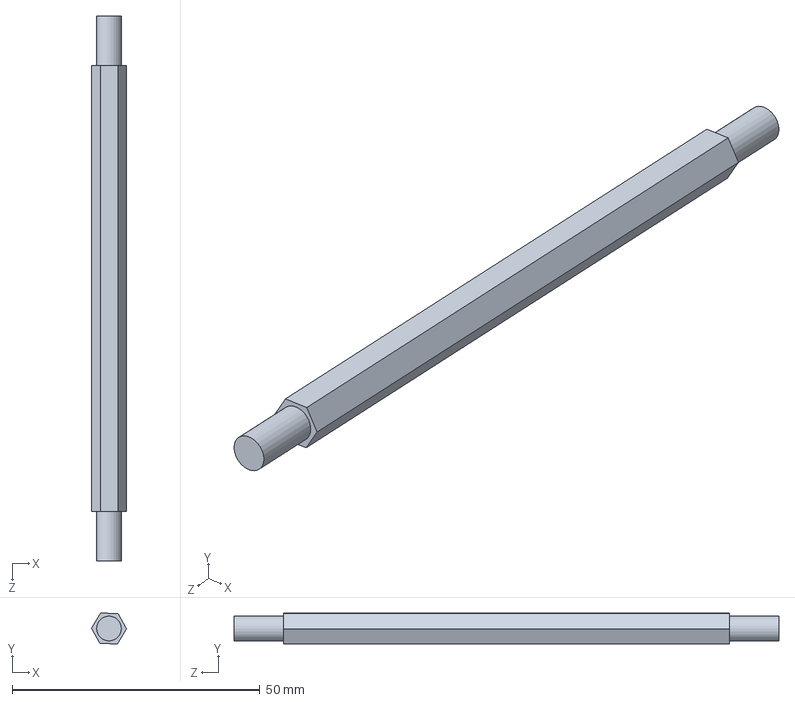
[picture p13: CAD file, 2026-07-06]
建模资料/小车装配体/铜柱.SLDPRT
7.10 x 6.20 x 110.0 mm
