Chemcrin/IntelligentTransformCart/建模资料/小车装配体/电池.SLDPRT

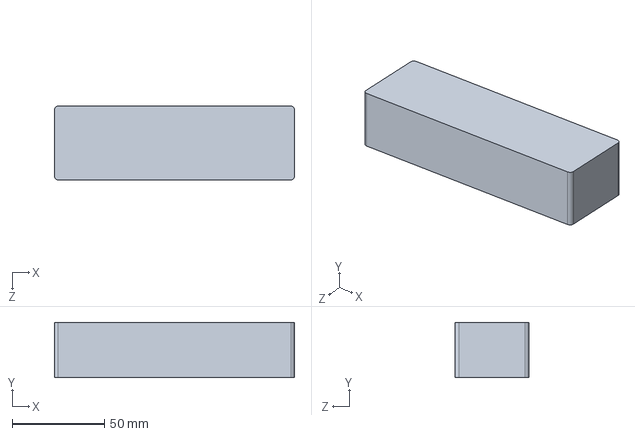
[picture p14: CAD file, 2026-07-06]
建模资料/小车装配体/电池.SLDPRT
130.0 x 30.0 x 40.0 mm
