Chemcrin/IntelligentTransformCart/建模资料/小车装配体/充电宝.SLDPRT

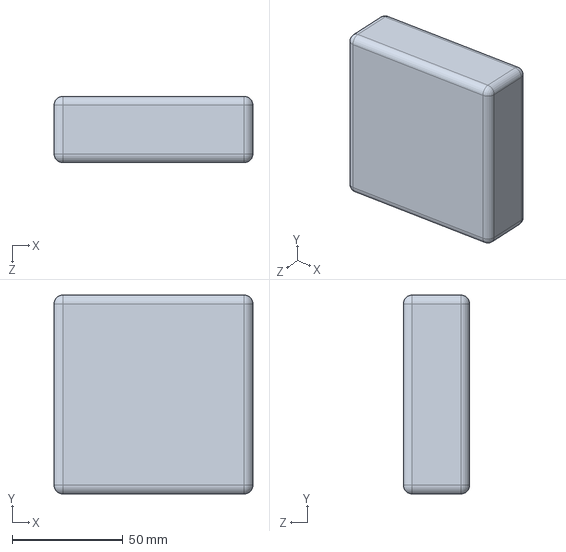
[picture p15: CAD file, 2026-07-06]
建模资料/小车装配体/充电宝.SLDPRT
90.0 x 90.0 x 30.0 mm
