Chemcrin/IntelligentTransformCart/建模资料/小车装配体/42步进电机支架.step.SLDPRT

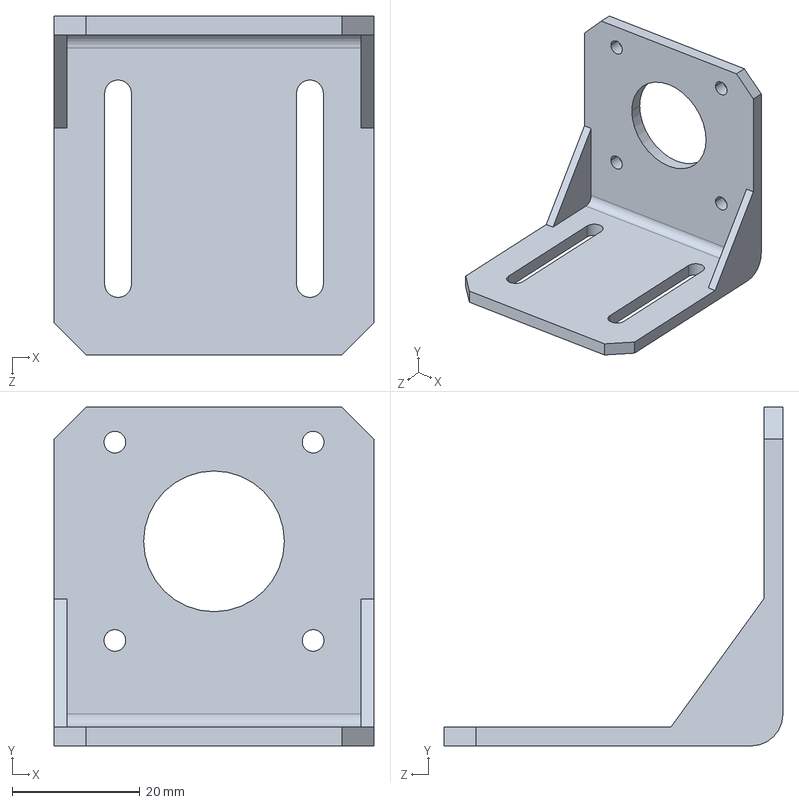
[picture p16: CAD file, 2026-07-06]
建模资料/小车装配体/42步进电机支架.step.SLDPRT
50.0 x 53.0 x 53.0 mm
