Chemcrin/IntelligentTransformCart/建模资料/小车装配体/方形料框.SLDPRT

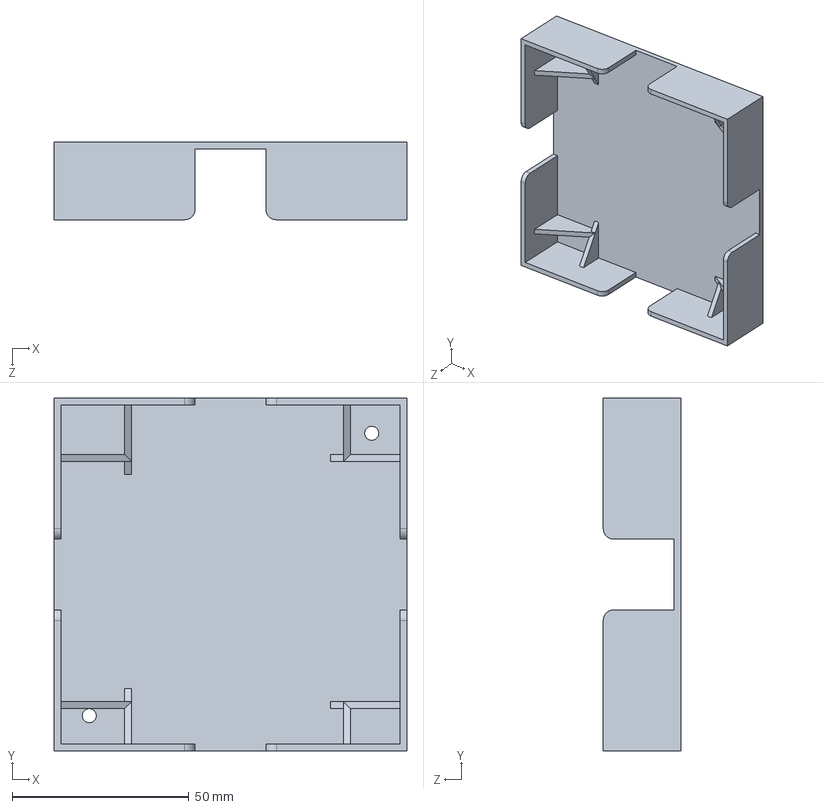
[picture p17: CAD file, 2026-05-22]
建模资料/小车装配体/方形料框.SLDPRT
100.0 x 100.0 x 22.0 mm
