Chemcrin/IntelligentTransformCart/建模资料/小车装配体/圆形料盘.SLDPRT

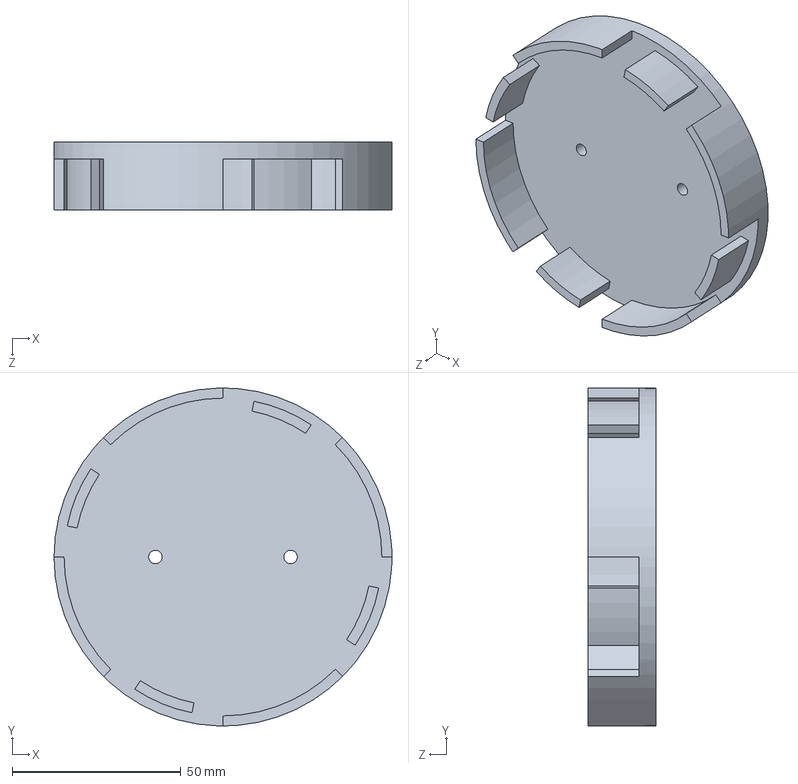
[picture p18: CAD file, 2026-05-22]
建模资料/小车装配体/圆形料盘.SLDPRT
100.0 x 100.0 x 20.0 mm
