Chemcrin/IntelligentTransformCart/建模资料/小车装配体/第二层(2).SLDPRT

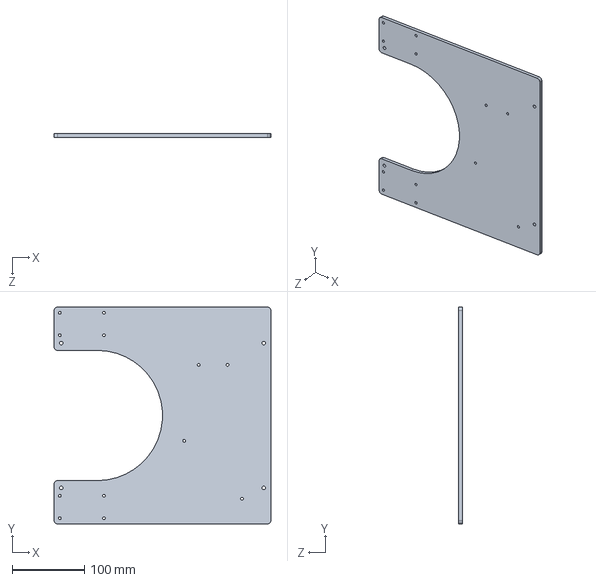
[picture p19: CAD file, 2026-05-22]
建模资料/小车装配体/第二层(2).SLDPRT
300.0 x 300.0 x 5.00 mm
