Chemcrin/IntelligentTransformCart/建模资料/小车装配体/机械爪a_mod.SLDPRT

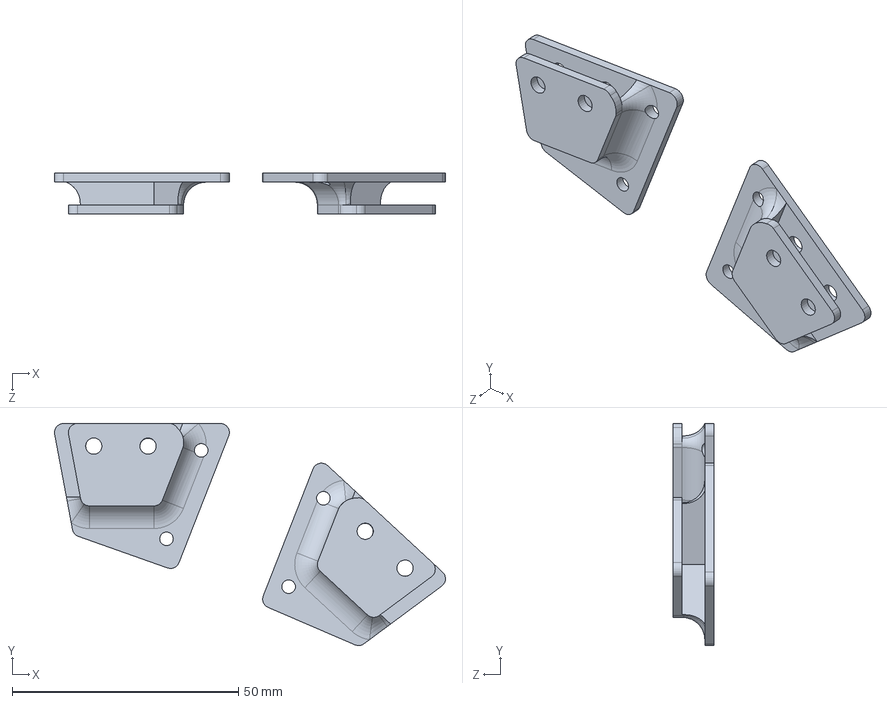
[picture p20: CAD file, 2026-05-22]
建模资料/小车装配体/机械爪a_mod.SLDPRT
86.4 x 49.1 x 9.00 mm
